ONEARMY/Precious-plastic-starterkit-extrusion/0. Start/Intro - Extrusion Workspace.pdf

www.preciousplastic.com/starterkits/showcase/extrusion

tiny.cc/starterkit-extrusion

Hi there!
Good to see you managed to get the download package of the

Extrusion Workspace Starter Kit!
If you haven’t done yet, make sure to have a look at the showcase page and quick introduction of this Starter Kit.

This package contains all the files you need to learn, plan and set up your Extrusion Workspace. It goes hand in hand with the step-by-step guide how to “Set up an Injection Workspace”.

There we explain the whole process of getting started, how to use the files in this download package and include links to relevant videos and documents. So don’t miss that!

Feel free to use whatever you need. Good luck!

-The Precious Plastic crew

# introduction
