ONEARMY/Precious-plastic-starterkit-extrusion/2. Plan your Business/2. Example (Extrusion)/Beamtastic - Action plan.png

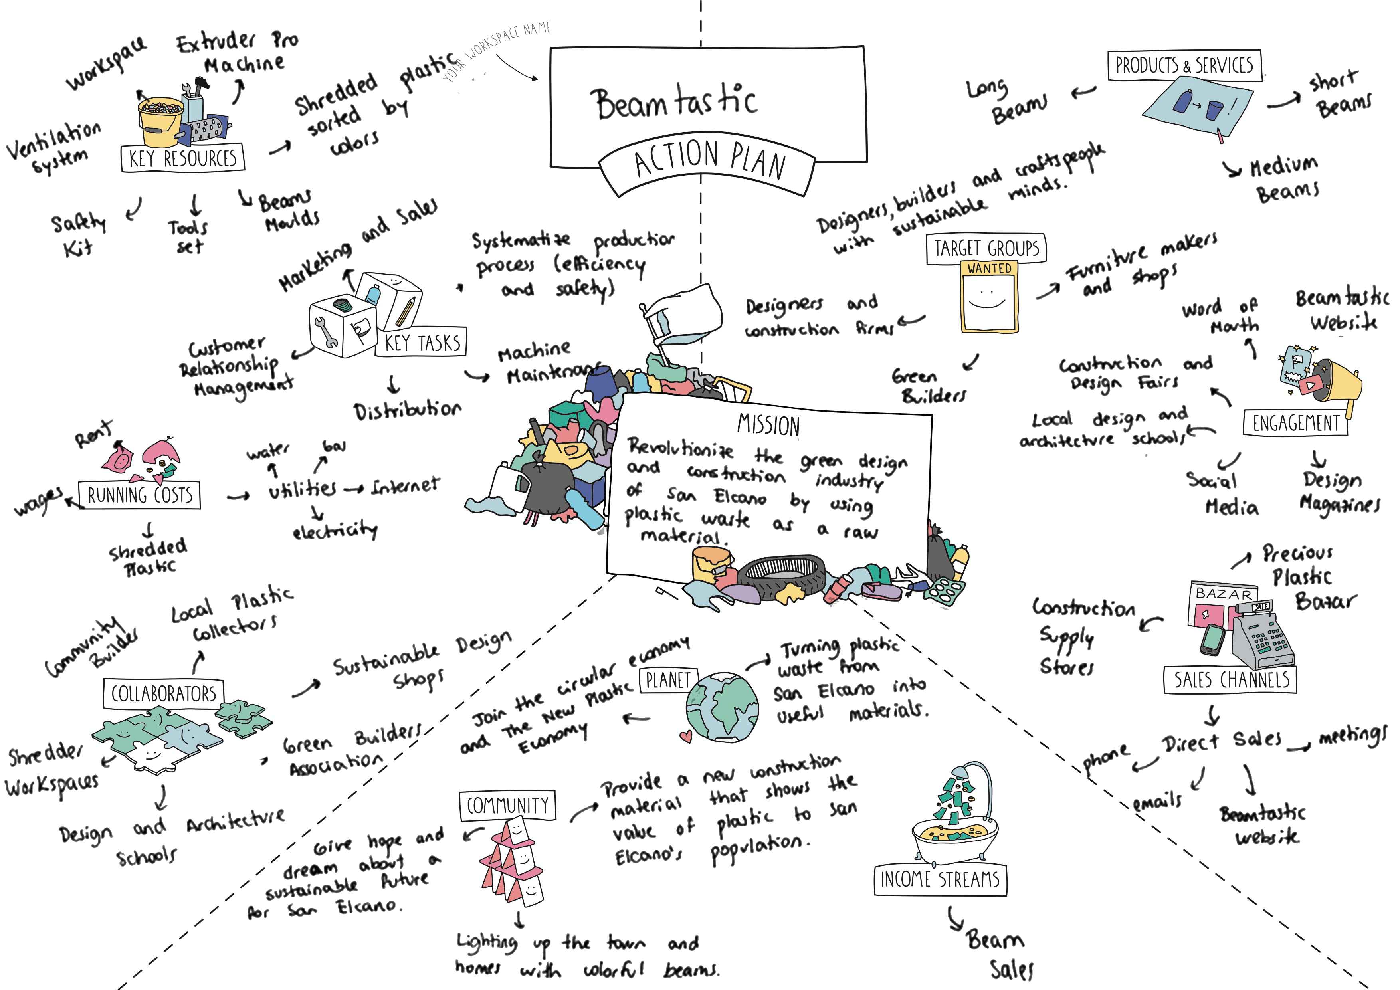
2. Plan your Business/2. Example (Extrusion)/Beamtastic - Action plan.png
