ONEARMY/Precious-plastic-starterkit-extrusion/6. Run your Workspace/1. Plastic Type Stamps/Stamps/HDPE.png

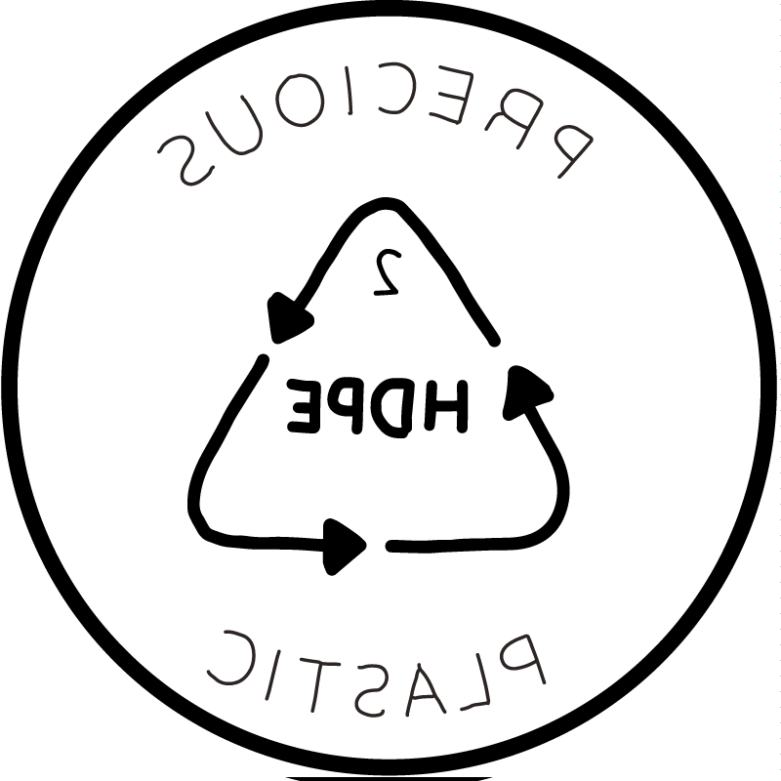
6. Run your Workspace/1. Plastic Type Stamps/Stamps/HDPE.png
