ONEARMY/Precious-plastic-starterkit-extrusion/6. Run your Workspace/3. Share/2. Project Images/Process/Recycling-process-2.jpg

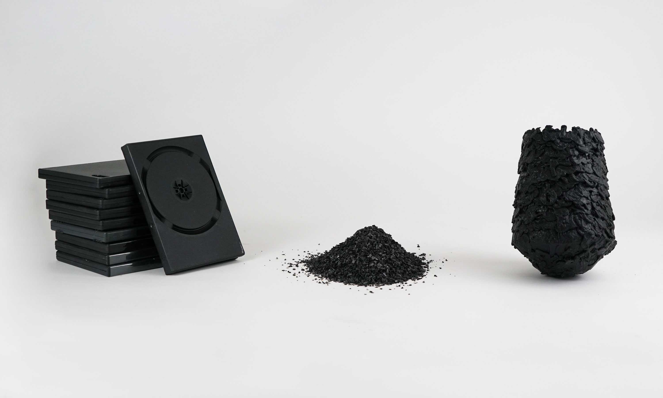
6. Run your Workspace/3. Share/2. Project Images/Process/Recycling-process-2.jpg
