ONEARMY/Precious-plastic-starterkit-extrusion/6. Run your Workspace/3. Share/2. Project Images/Products/Dome.jpg

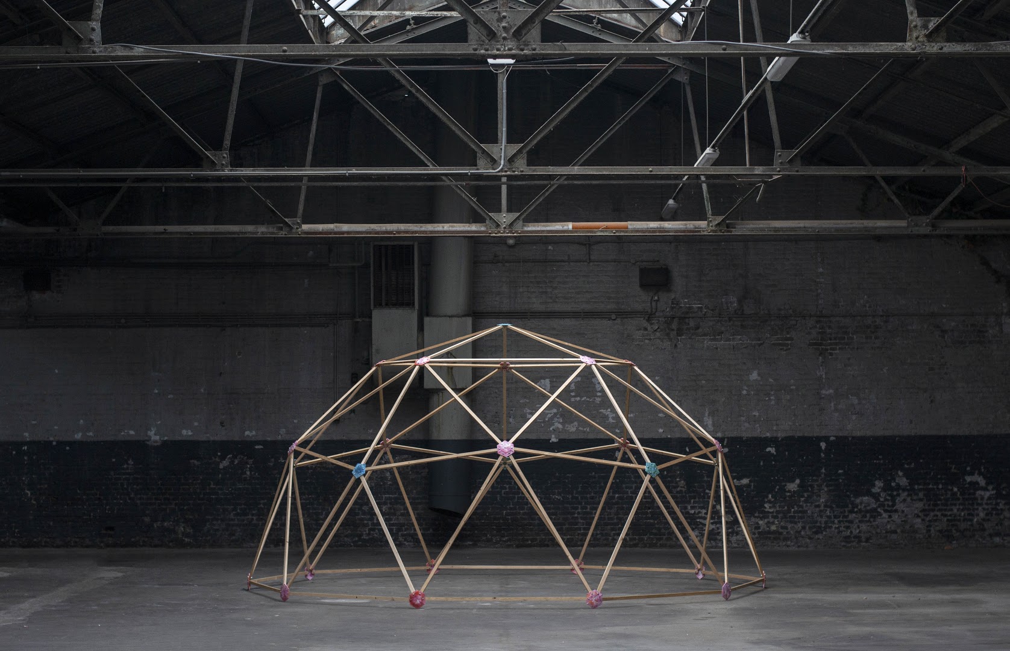
6. Run your Workspace/3. Share/2. Project Images/Products/Dome.jpg
