ONEARMY/Precious-plastic-starterkit-extrusion/3. Build the machine/Extrusion-Pro-Files/1-3D CAD/Extruder Solidworks CAD/EXTPRO-V1 1140.00-A Barrel.SLDASM

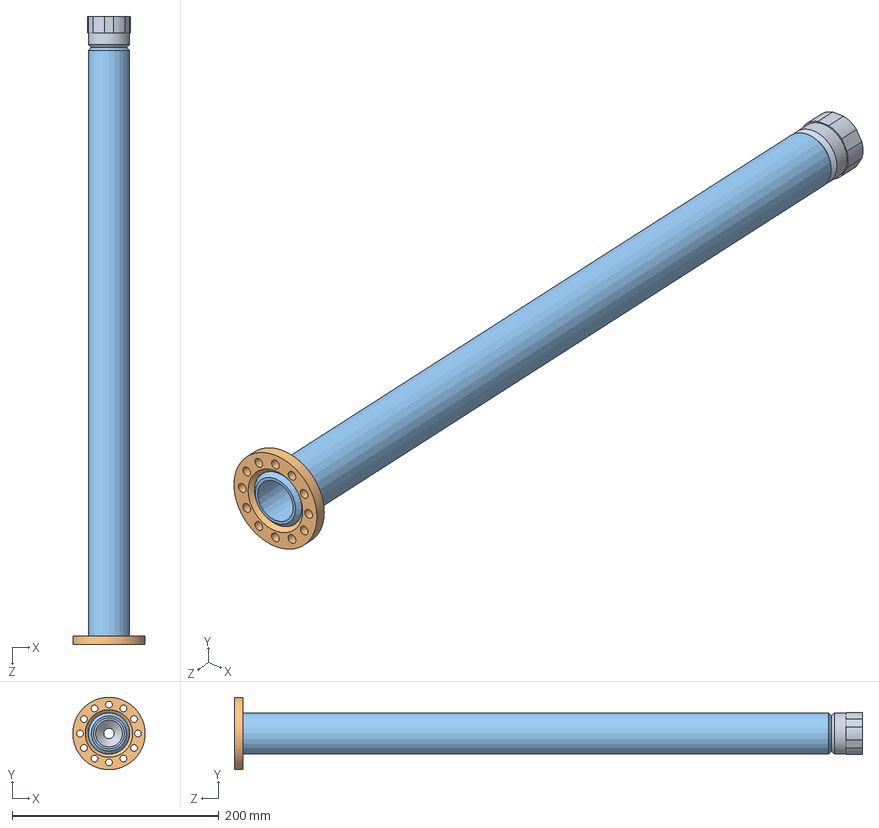
[picture p52: CAD file, 2020-01-07]
3. Build the machine/Extrusion-Pro-Files/1-3D CAD/Extruder Solidworks CAD/EXTPRO-V1 1140.00-A Barrel.SLDASM
70.0 x 70.0 x 608.0 mm
EXTPRO-V1 1140.01-A Barrel
EXTPRO-V1 1140.02-A Barrel flange
EXTPRO-V1 1140.03-A Barrel tip
