ONEARMY/Precious-plastic-starterkit-extrusion/3. Build the machine/Extrusion-Pro-Files/1-3D CAD/Extruder Solidworks CAD/EXTPRO-V1 1110.00-A Gearbox flange.sldasm

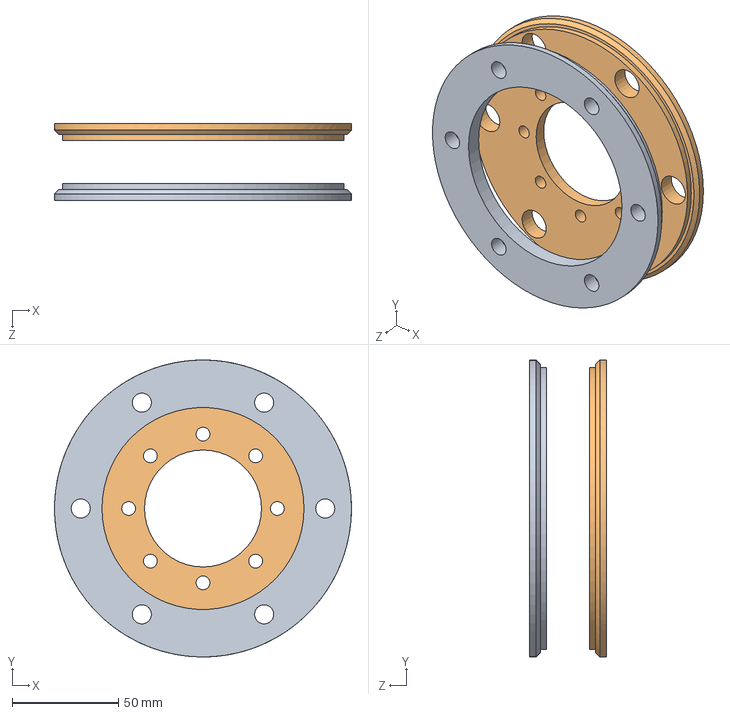
[picture p53: CAD file, 2020-01-07]
3. Build the machine/Extrusion-Pro-Files/1-3D CAD/Extruder Solidworks CAD/EXTPRO-V1 1110.00-A Gearbox flange.sldasm
139.7 x 139.7 x 36.0 mm
EXTPRO-V1 1110.02-A Flange 1
EXTPRO-V1 1110.03-A Flange 2
