ONEARMY/Precious-plastic-starterkit-extrusion/3. Build the machine/Extrusion-Pro-Files/1-3D CAD/Extruder Solidworks CAD/EXTPRO-V1 1121.00-A Bearing body.SLDASM

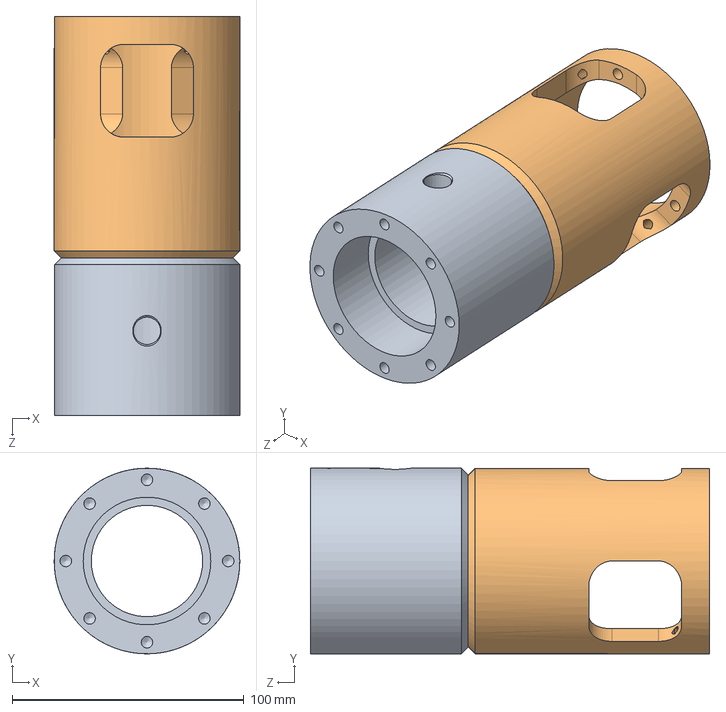
[picture p54: CAD file, 2020-01-07]
3. Build the machine/Extrusion-Pro-Files/1-3D CAD/Extruder Solidworks CAD/EXTPRO-V1 1121.00-A Bearing body.SLDASM
80.0 x 80.0 x 172.0 mm
EXTPRO-V1 1121.01-A Transition Piece
EXTPRO-V1 1121.02-A Bearing body
