ONEARMY/Precious-plastic-starterkit-extrusion/4. Set up the space/CAD Files/Adjustable mould support surface/Adjustmable mould support surface.STEP

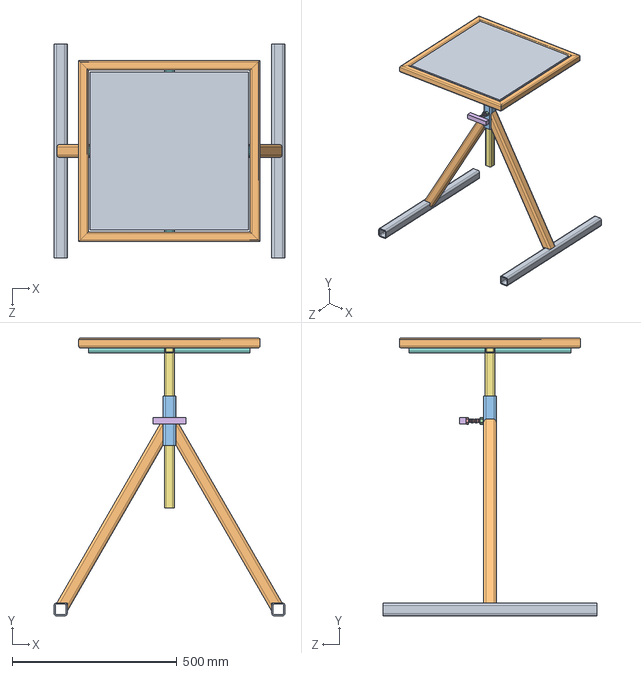
[picture p65: CAD file, 2020-01-07]
4. Set up the space/CAD Files/Adjustable mould support surface/Adjustmable mould support surface.STEP
700.0 x 843.0 x 650.0 mm
