ONEARMY/Precious-plastic-starterkit-extrusion/4. Set up the space/CAD Files/Beam mould hanger/Beam mould hanger.STEP

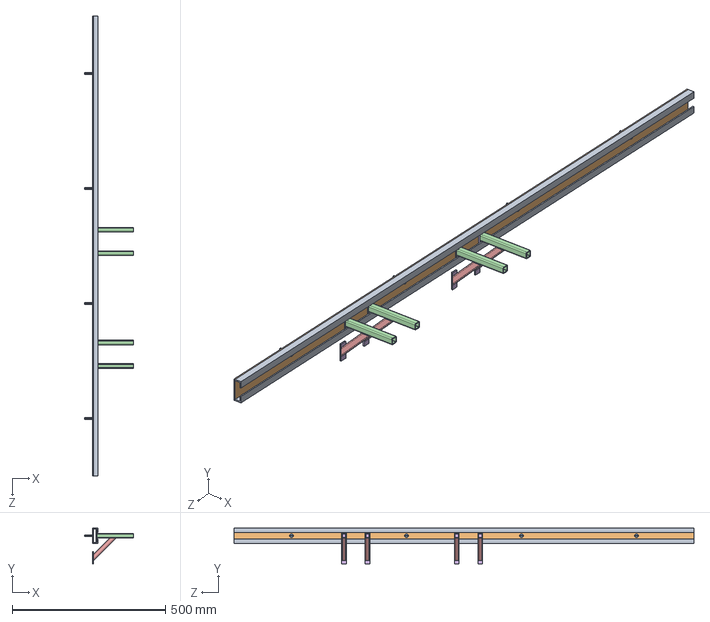
[picture p66: CAD file, 2020-01-07]
4. Set up the space/CAD Files/Beam mould hanger/Beam mould hanger.STEP
161.0 x 116.7 x 1500.0 mm
