ONEARMY/Precious-plastic-starterkit-extrusion/4. Set up the space/CAD Files/Beam storage rack/Beam storage rack.STEP

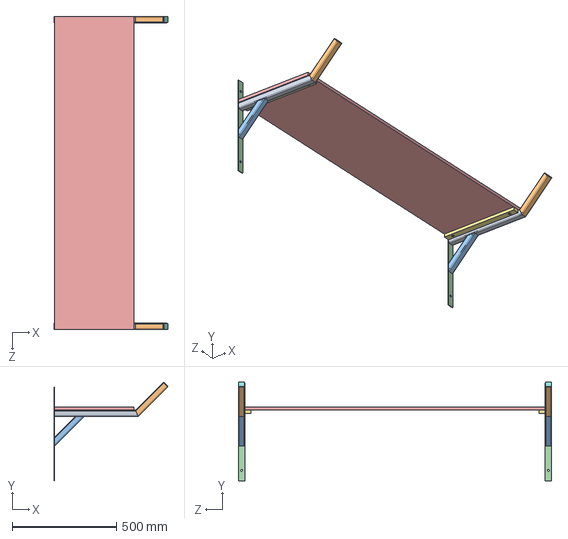
[picture p67: CAD file, 2020-01-07]
4. Set up the space/CAD Files/Beam storage rack/Beam storage rack.STEP
545.8 x 472.6 x 1500.0 mm
