ONEARMY/Precious-plastic-starterkit-extrusion/4. Set up the space/CAD Files/Mobile tool station/Mobile tool station.STEP

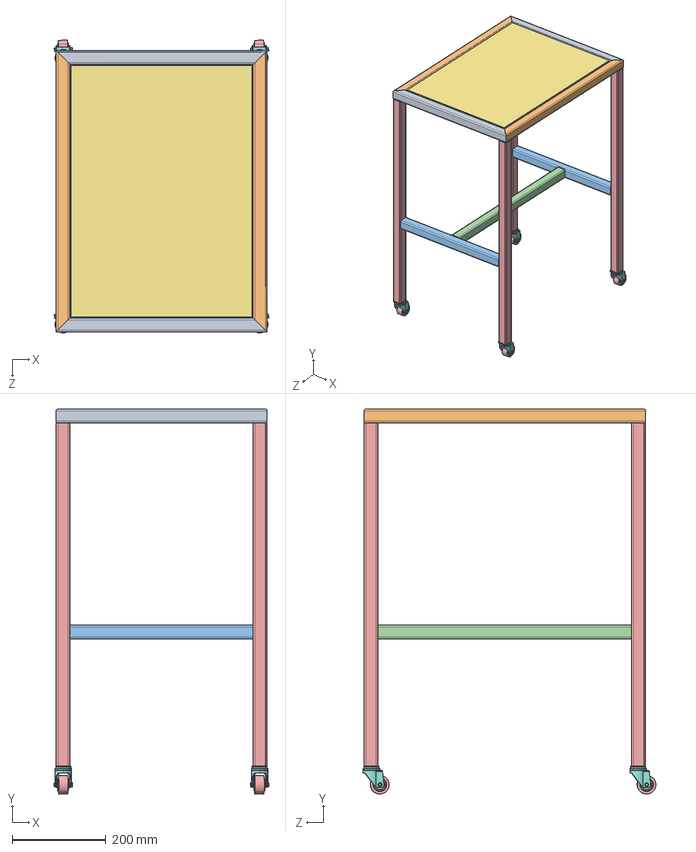
[picture p68: CAD file, 2020-01-07]
4. Set up the space/CAD Files/Mobile tool station/Mobile tool station.STEP
457.0 x 820.0 x 623.8 mm
