ONEARMY/Precious-plastic-starterkit-extrusion/4. Set up the space/CAD Files/Shredded plastic storage shelf/Shredded plastic storage shelf.STEP

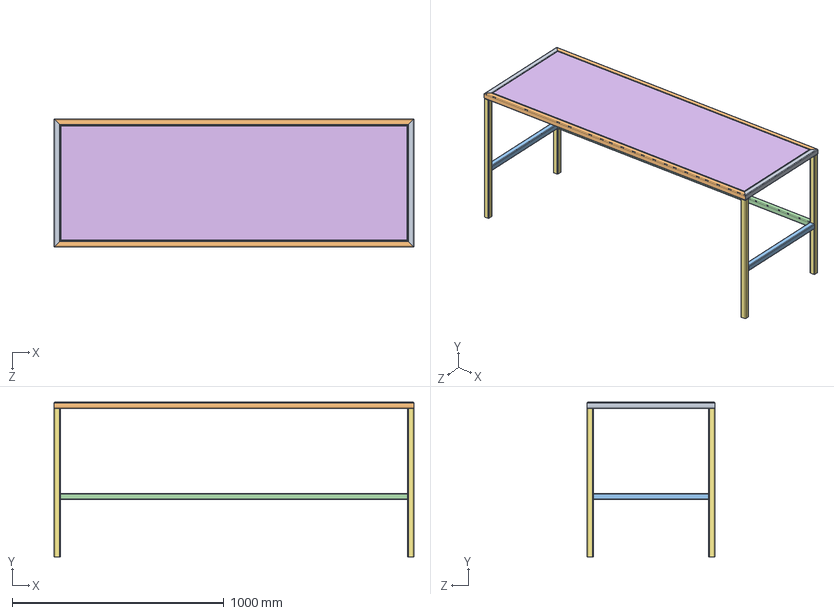
[picture p69: CAD file, 2020-01-07]
4. Set up the space/CAD Files/Shredded plastic storage shelf/Shredded plastic storage shelf.STEP
1700.0 x 730.0 x 605.0 mm
