ONEARMY/Precious-plastic-starterkit-extrusion/4. Set up the space/CAD Files/Shredded plastic trolley/Shredded plastic trolley.STEP

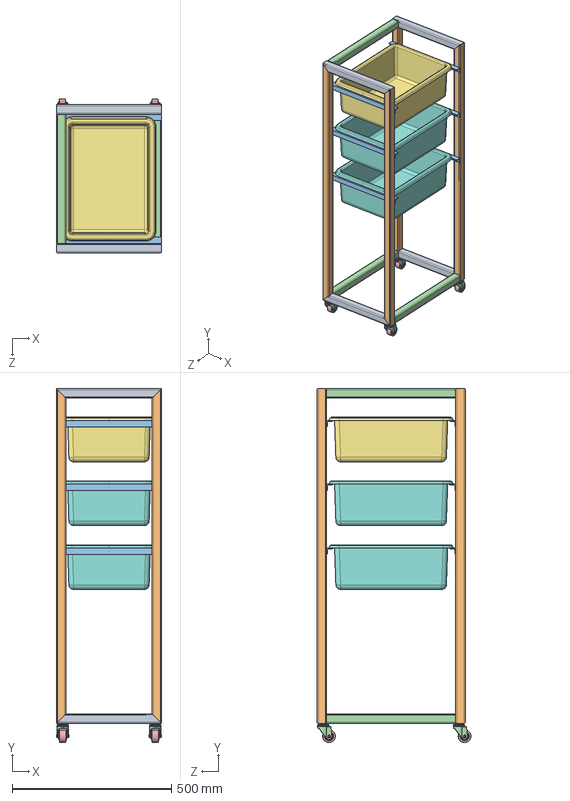
[picture p70: CAD file, 2020-01-07]
4. Set up the space/CAD Files/Shredded plastic trolley/Shredded plastic trolley.STEP
330.0 x 1110.0 x 482.9 mm
