ONEARMY/Precious-plastic-starterkit-extrusion/4. Set up the space/CAD Files/Workbench/Workbench.STEP

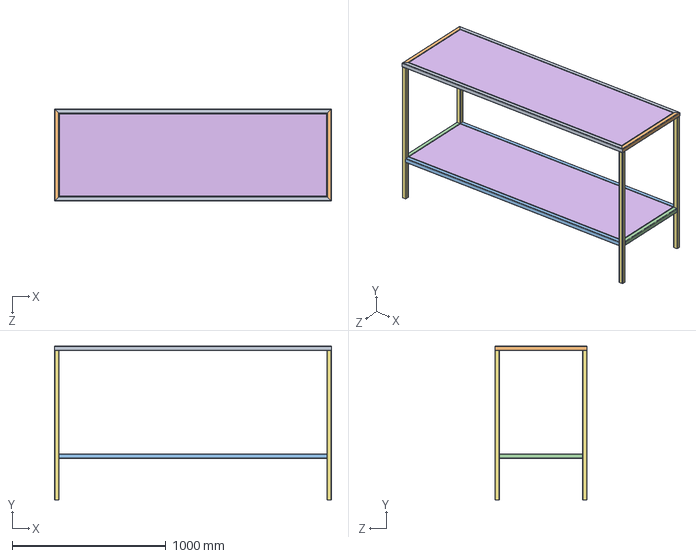
[picture p71: CAD file, 2020-01-07]
4. Set up the space/CAD Files/Workbench/Workbench.STEP
1800.0 x 1000.0 x 600.0 mm
