ONEARMY/Precious-plastic-starterkit-extrusion/3. Build the machine/Extrusion-Pro-Files/2-Laser cut files/STEP/Electronics box (CarbonSteel)/EXTPRO-V1 2100.06-A Cover attachment - QTY_4.STEP

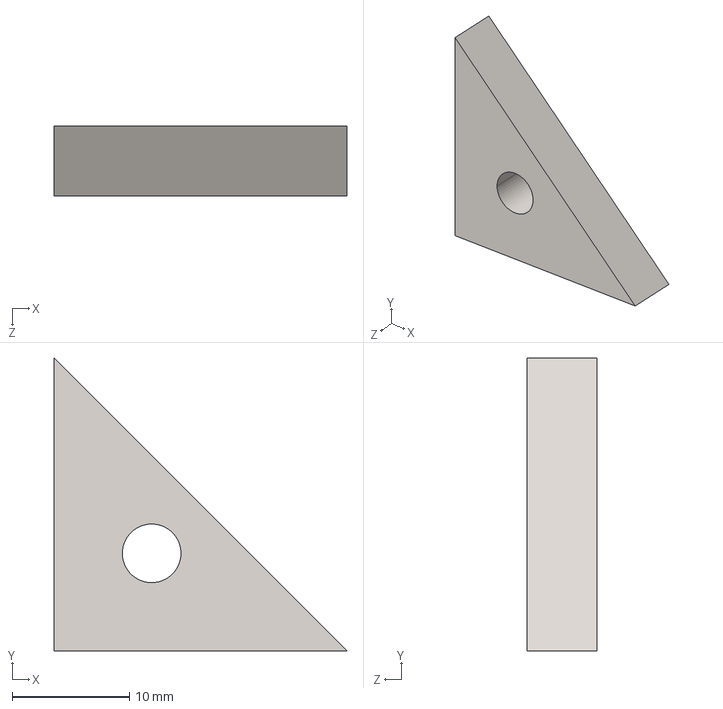
[picture p74: CAD file, 2020-01-07]
3. Build the machine/Extrusion-Pro-Files/2-Laser cut files/STEP/Electronics box (CarbonSteel)/EXTPRO-V1 2100.06-A Cover attachment - QTY_4.STEP
25.0 x 25.0 x 6.00 mm
