ONEARMY/Precious-plastic-starterkit-extrusion/3. Build the machine/Extrusion-Pro-Files/2-Laser cut files/STEP/Flanges (CarbonSteel)/EXTPRO-V1 1140.02-A Barrel flange - QTY_1.STEP

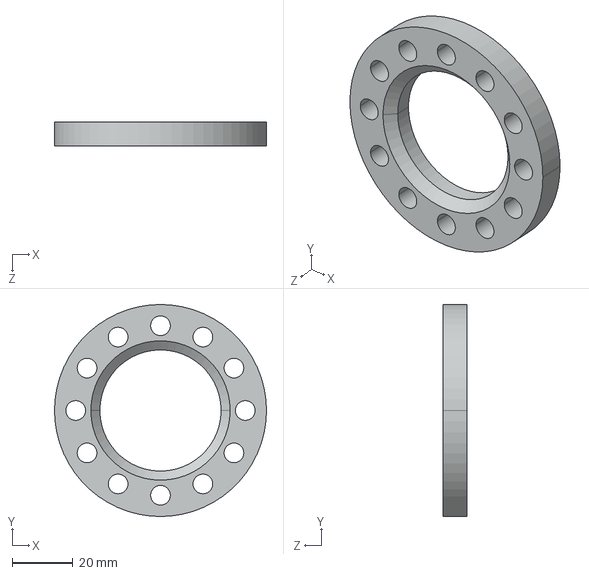
[picture p75: CAD file, 2020-01-07]
3. Build the machine/Extrusion-Pro-Files/2-Laser cut files/STEP/Flanges (CarbonSteel)/EXTPRO-V1 1140.02-A Barrel flange - QTY_1.STEP
70.0 x 70.0 x 8.00 mm
