ONEARMY/Precious-plastic-starterkit-extrusion/3. Build the machine/Upgrades/Barrel Support/1-3D CAD/EXTPRO-V1 3000.05-A Barrel support 2.SLDPRT

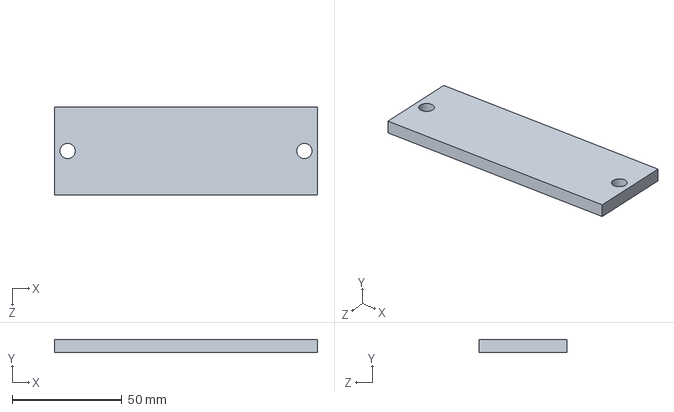
[picture p76: CAD file, 2020-01-07]
3. Build the machine/Upgrades/Barrel Support/1-3D CAD/EXTPRO-V1 3000.05-A Barrel support 2.SLDPRT
120.0 x 6.00 x 40.0 mm
