ONEARMY/Precious-plastic-starterkit-extrusion/3. Build the machine/Extrusion-Pro-Files/2-Laser cut files/DXF/Electronics box (1mm_CarbonSteel)/EXTPRO-V1 2100.03-A Side 2 - QTY_1.DXF

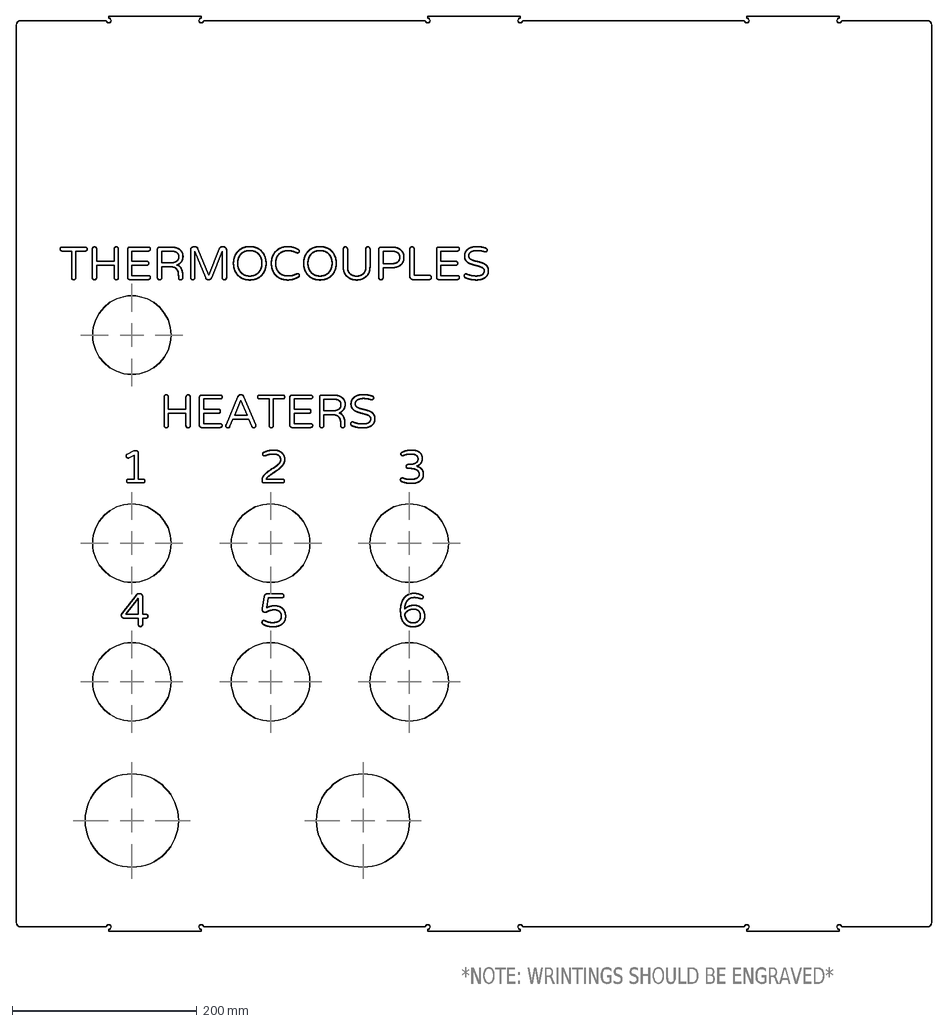
[picture p77: CAD file, 2020-01-07]
3. Build the machine/Extrusion-Pro-Files/2-Laser cut files/DXF/Electronics box (1mm_CarbonSteel)/EXTPRO-V1 2100.03-A Side 2 - QTY_1.DXF
*NOTE: WRINTINGS SHOULD BE ENGRAVED*
