ONEARMY/Precious-plastic-starterkit-extrusion/3. Build the machine/Extrusion-Pro-Files/2-Laser cut files/DXF/Flanges (8mm_CarbonSteel)/EXTPRO-V1 1110.03-A Flange 2 - QTY_1.DXF

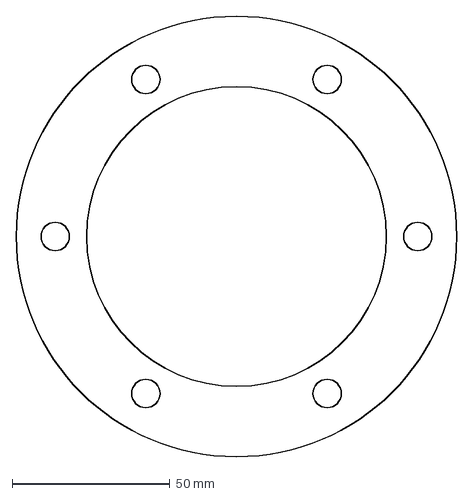
[picture p78: CAD file, 2020-01-07]
3. Build the machine/Extrusion-Pro-Files/2-Laser cut files/DXF/Flanges (8mm_CarbonSteel)/EXTPRO-V1 1110.03-A Flange 2 - QTY_1.DXF
139.7 x 139.7 mm
