ONEARMY/Precious-plastic-starterkit-extrusion/3. Build the machine/Extrusion-Pro-Files/2-Laser cut files/DXF/Electronics box (1mm_CarbonSteel)/EXTPRO-V1 2100.04-A Side 1 - QTY_1.DXF

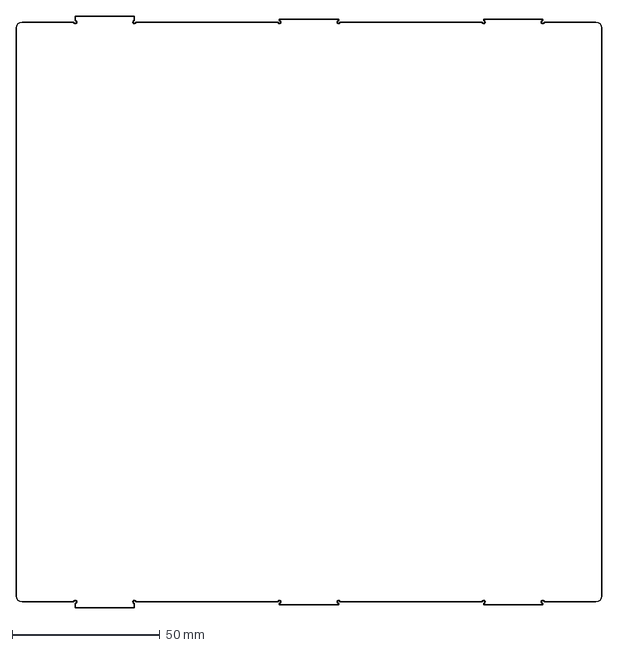
[picture p80: CAD file, 2020-01-07]
3. Build the machine/Extrusion-Pro-Files/2-Laser cut files/DXF/Electronics box (1mm_CarbonSteel)/EXTPRO-V1 2100.04-A Side 1 - QTY_1.DXF
198.0 x 200.0 mm
