ONEARMY/Precious-plastic-starterkit-extrusion/3. Build the machine/Extrusion-Pro-Files/2-Laser cut files/DXF/Flanges (8mm_CarbonSteel)/EXTPRO-V1 1130.03-A Barrel flange 2 - QTY_1.DXF

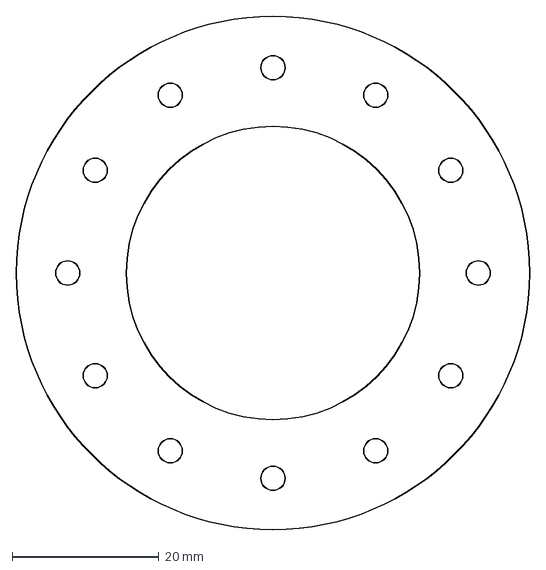
[picture p81: CAD file, 2020-01-07]
3. Build the machine/Extrusion-Pro-Files/2-Laser cut files/DXF/Flanges (8mm_CarbonSteel)/EXTPRO-V1 1130.03-A Barrel flange 2 - QTY_1.DXF
70.0 x 70.0 mm
