ONEARMY/Precious-plastic-starterkit-extrusion/3. Build the machine/Extrusion-Pro-Files/2-Laser cut files/STEP/Electronics box (CarbonSteel)/EXTPRO-V1 2100.03-A Side 2 - QTY_1.STEP

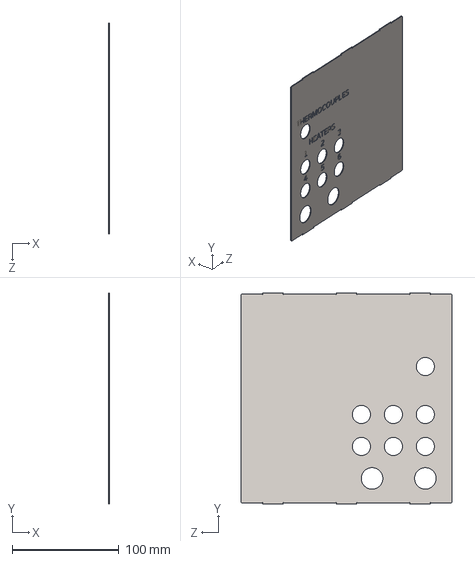
[picture p82: CAD file, 2020-01-07]
3. Build the machine/Extrusion-Pro-Files/2-Laser cut files/STEP/Electronics box (CarbonSteel)/EXTPRO-V1 2100.03-A Side 2 - QTY_1.STEP
1.00 x 198.0 x 198.0 mm
