ONEARMY/Precious-plastic-starterkit-extrusion/3. Build the machine/Extrusion-Pro-Files/2-Laser cut files/STEP/Flanges (CarbonSteel)/EXTPRO-V1 1110.03-A Motor side flange - QTY_1.STEP

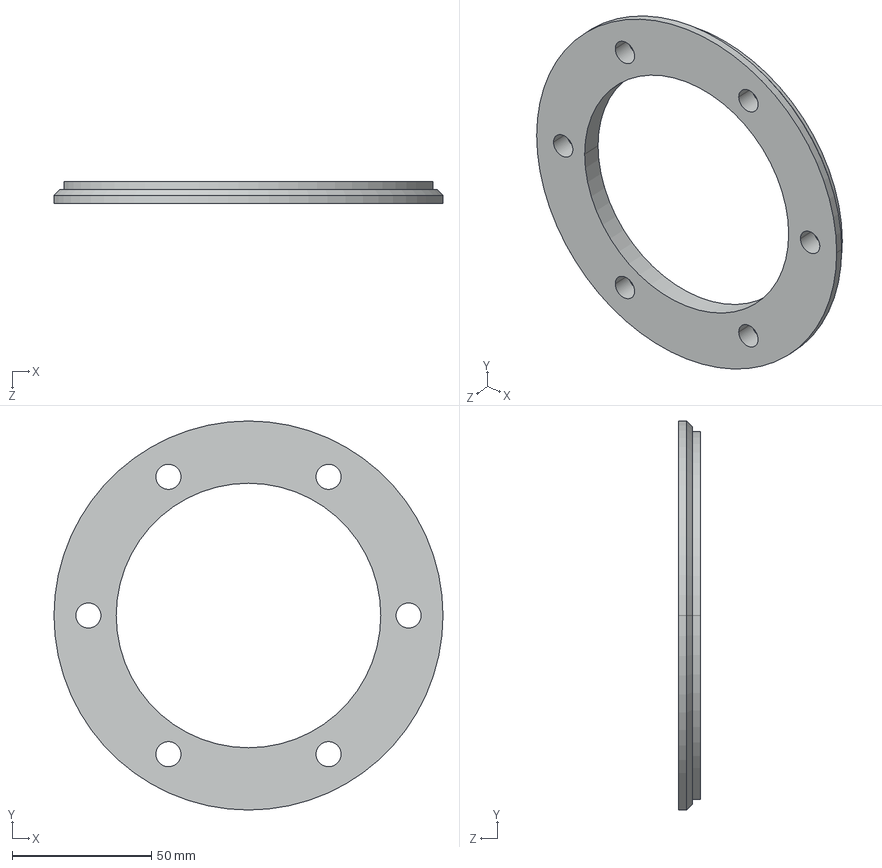
[picture p83: CAD file, 2020-01-07]
3. Build the machine/Extrusion-Pro-Files/2-Laser cut files/STEP/Flanges (CarbonSteel)/EXTPRO-V1 1110.03-A Motor side flange - QTY_1.STEP
139.7 x 139.7 x 8.00 mm
