ONEARMY/Precious-plastic-starterkit-extrusion/3. Build the machine/Extrusion-Pro-Files/1-3D CAD/Extruder Solidworks CAD/EXTPRO-V1 03 Shaft Clamp.sldprt

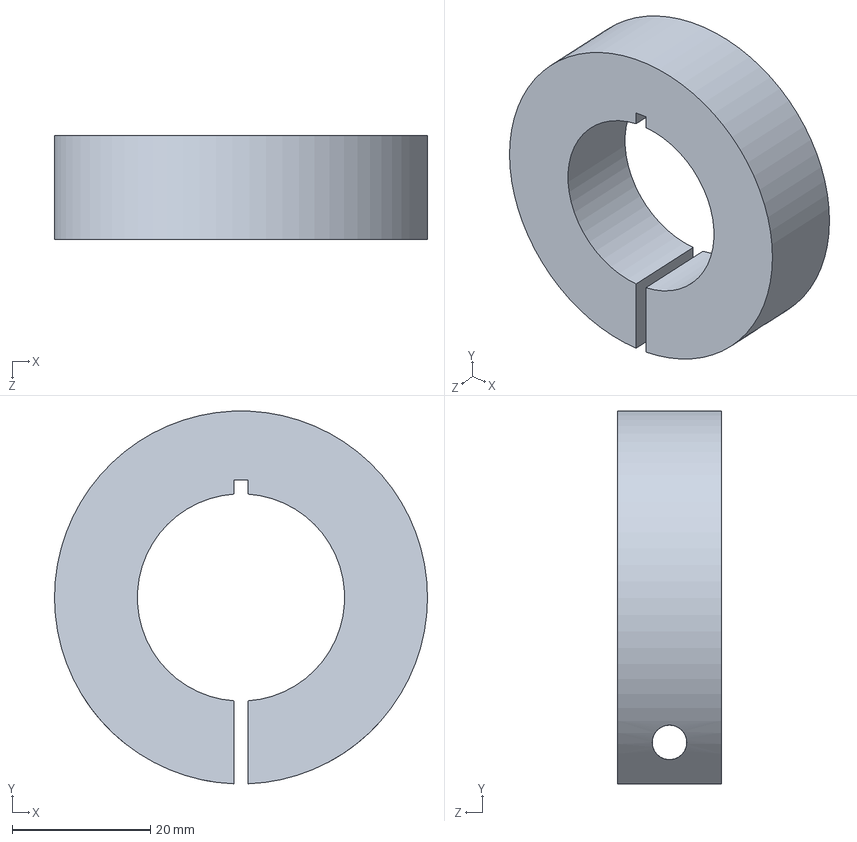
[picture p84: CAD file, 2020-01-07]
3. Build the machine/Extrusion-Pro-Files/1-3D CAD/Extruder Solidworks CAD/EXTPRO-V1 03 Shaft Clamp.sldprt
54.0 x 54.0 x 15.0 mm
