ONEARMY/Precious-plastic-starterkit-extrusion/3. Build the machine/Extrusion-Pro-Files/2-Laser cut files/DXF/Electronics box (1mm_CarbonSteel)/EXTPRO-V1 2100.01-A Cover - QTY_1.DXF

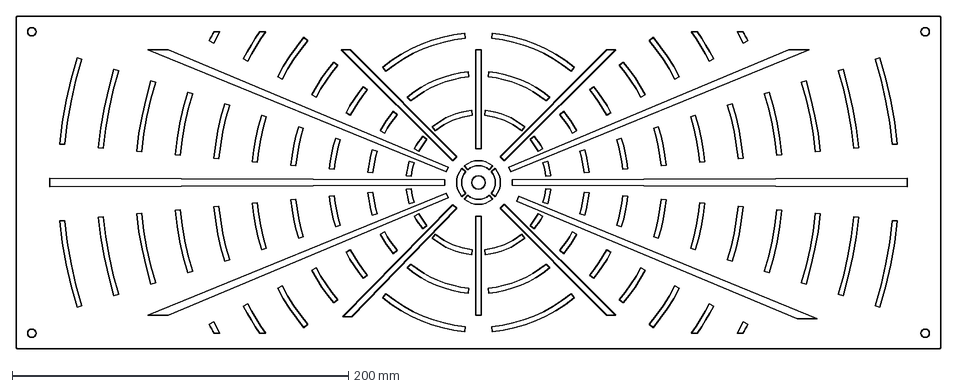
[picture p85: CAD file, 2020-01-07]
3. Build the machine/Extrusion-Pro-Files/2-Laser cut files/DXF/Electronics box (1mm_CarbonSteel)/EXTPRO-V1 2100.01-A Cover - QTY_1.DXF
550.0 x 198.0 mm
