ONEARMY/Precious-plastic-starterkit-extrusion/3. Build the machine/Extrusion-Pro-Files/2-Laser cut files/STEP/Electronics box (CarbonSteel)/EXTPRO-V1 2100.05-A Side 3 - QTY_2.STEP

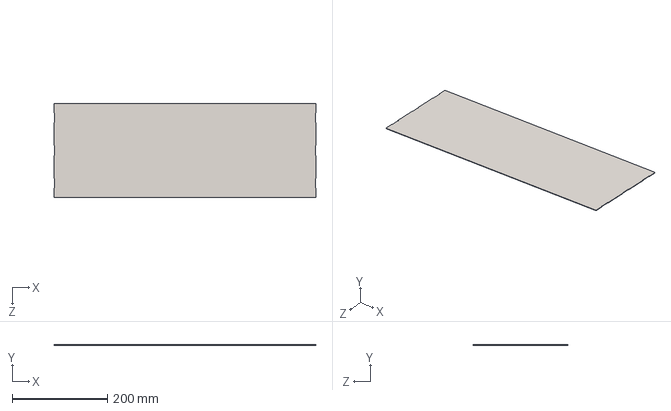
[picture p86: CAD file, 2020-01-07]
3. Build the machine/Extrusion-Pro-Files/2-Laser cut files/STEP/Electronics box (CarbonSteel)/EXTPRO-V1 2100.05-A Side 3 - QTY_2.STEP
550.0 x 1.00 x 198.0 mm
