ONEARMY/Precious-plastic-starterkit-extrusion/3. Build the machine/Extrusion-Pro-Files/2-Laser cut files/STEP/Electronics box (CarbonSteel)/EXTPRO-V1 2100.02-A Front - QTY_1.STEP

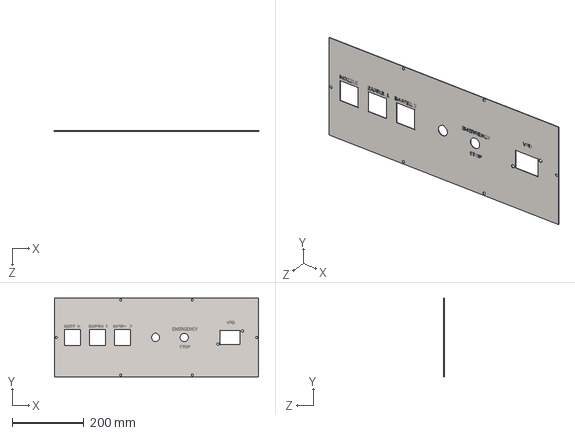
[picture p87: CAD file, 2020-01-07]
3. Build the machine/Extrusion-Pro-Files/2-Laser cut files/STEP/Electronics box (CarbonSteel)/EXTPRO-V1 2100.02-A Front - QTY_1.STEP
570.0 x 220.0 x 1.00 mm
