ONEARMY/Precious-plastic-starterkit-extrusion/3. Build the machine/Extrusion-Pro-Files/1-3D CAD/Extruder Solidworks CAD/EXTPRO-V1 1140.03-A Barrel tip.sldprt

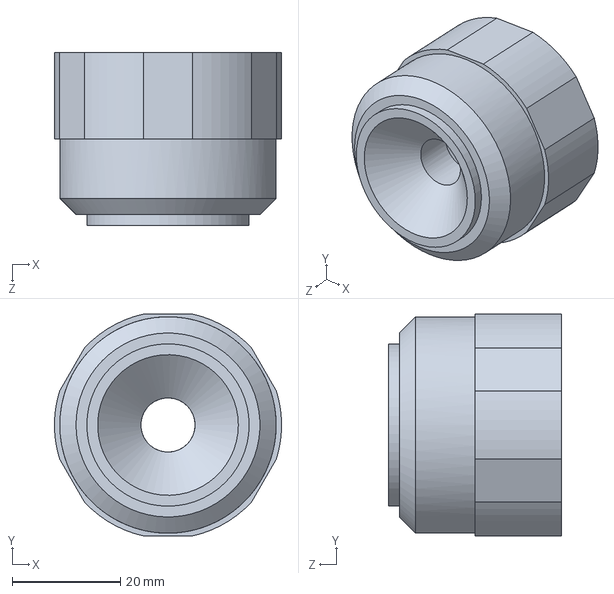
[picture p88: CAD file, 2020-01-07]
3. Build the machine/Extrusion-Pro-Files/1-3D CAD/Extruder Solidworks CAD/EXTPRO-V1 1140.03-A Barrel tip.sldprt
42.0 x 41.0 x 32.0 mm
