ONEARMY/Precious-plastic-starterkit-extrusion/3. Build the machine/Extrusion-Pro-Files/1-3D CAD/Extruder Solidworks CAD/EXTPRO-V1 02 Bearing seal-din3760-as_42x55x8-fkm.SLDPRT

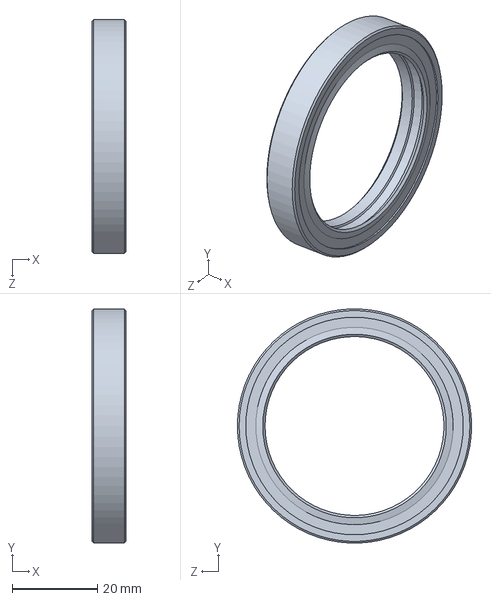
[picture p93: CAD file, 2020-01-07]
3. Build the machine/Extrusion-Pro-Files/1-3D CAD/Extruder Solidworks CAD/EXTPRO-V1 02 Bearing seal-din3760-as_42x55x8-fkm.SLDPRT
8.00 x 54.9 x 55.0 mm
