ONEARMY/Precious-plastic-starterkit-extrusion/3. Build the machine/Extrusion-Pro-Files/1-3D CAD/Extruder Solidworks CAD/EXTPRO-V1 3000.04-A Frame foot.SLDPRT

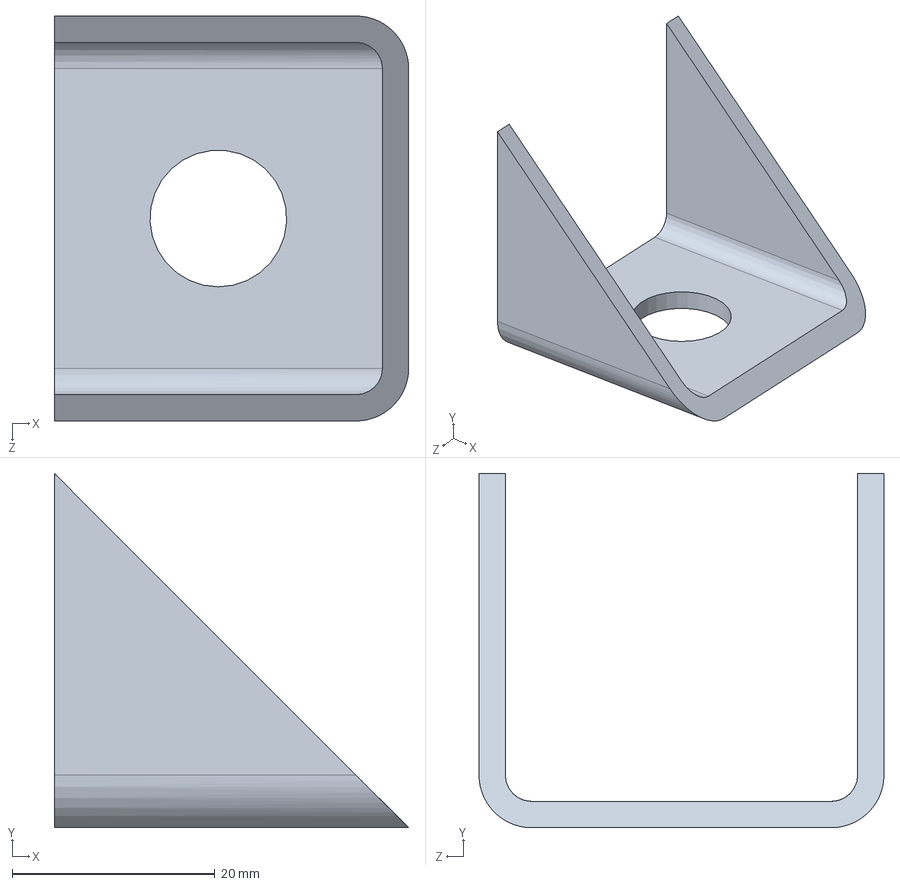
[picture p94: CAD file, 2020-01-07]
3. Build the machine/Extrusion-Pro-Files/1-3D CAD/Extruder Solidworks CAD/EXTPRO-V1 3000.04-A Frame foot.SLDPRT
35.0 x 35.0 x 40.0 mm
