ONEARMY/Precious-plastic-starterkit-extrusion/3. Build the machine/Extrusion-Pro-Files/1-3D CAD/Extruder Solidworks CAD/EXTPRO-V1 2000.01-A Electronics box support.SLDPRT

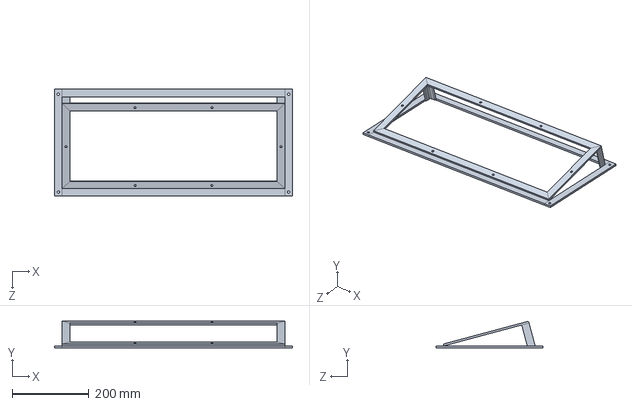
[picture p95: CAD file, 2020-01-07]
3. Build the machine/Extrusion-Pro-Files/1-3D CAD/Extruder Solidworks CAD/EXTPRO-V1 2000.01-A Electronics box support.SLDPRT
620.0 x 69.4 x 278.1 mm
