ONEARMY/Precious-plastic-starterkit-extrusion/3. Build the machine/Extrusion-Pro-Files/1-3D CAD/Extruder Solidworks CAD/EXTPRO-V1 1120.01-A Seal bearing spacer.sldprt

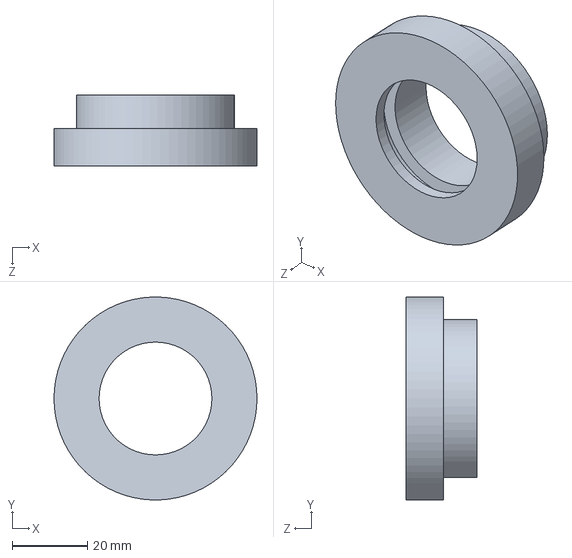
[picture p98: CAD file, 2020-01-07]
3. Build the machine/Extrusion-Pro-Files/1-3D CAD/Extruder Solidworks CAD/EXTPRO-V1 1120.01-A Seal bearing spacer.sldprt
54.0 x 53.9 x 19.0 mm
