ONEARMY/Precious-plastic-starterkit-extrusion/3. Build the machine/Extrusion-Pro-Files/1-3D CAD/Extruder Solidworks CAD/EXTPRO-V1 1120.02-A Coupling Shaft.sldprt

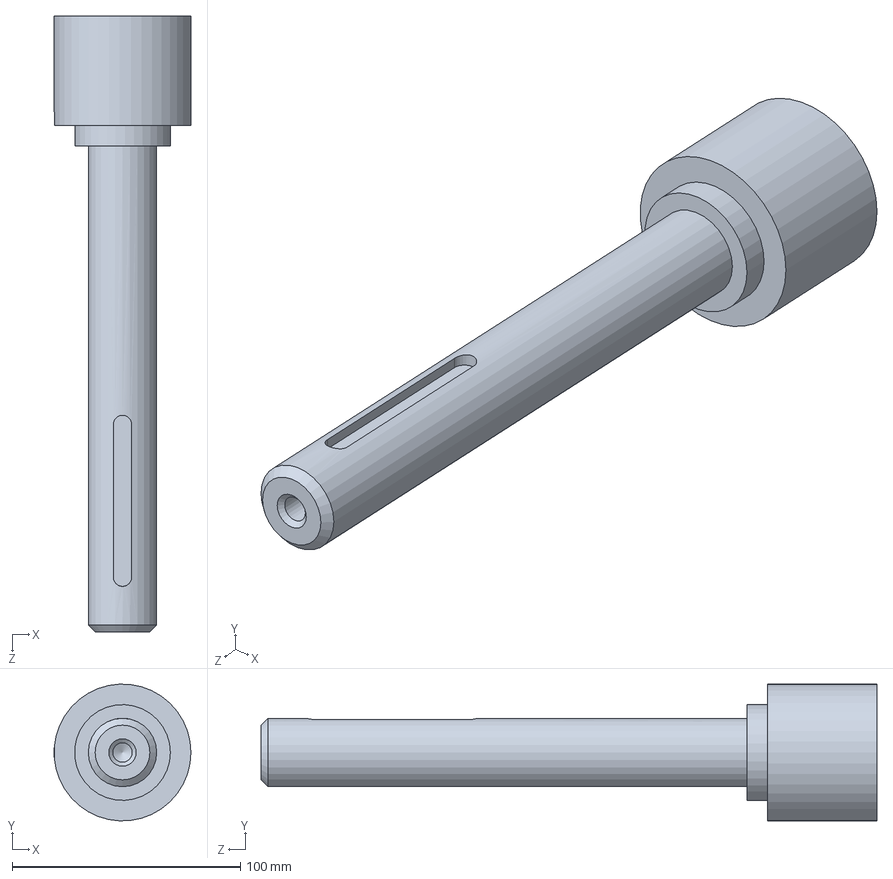
[picture p103: CAD file, 2020-01-07]
3. Build the machine/Extrusion-Pro-Files/1-3D CAD/Extruder Solidworks CAD/EXTPRO-V1 1120.02-A Coupling Shaft.sldprt
60.0 x 60.0 x 270.0 mm
