ONEARMY/Precious-plastic-starterkit-extrusion/3. Build the machine/Extrusion-Pro-Files/1-3D CAD/Extruder Solidworks CAD/EXTPRO-V1 3000.02-A Top shelf.SLDPRT

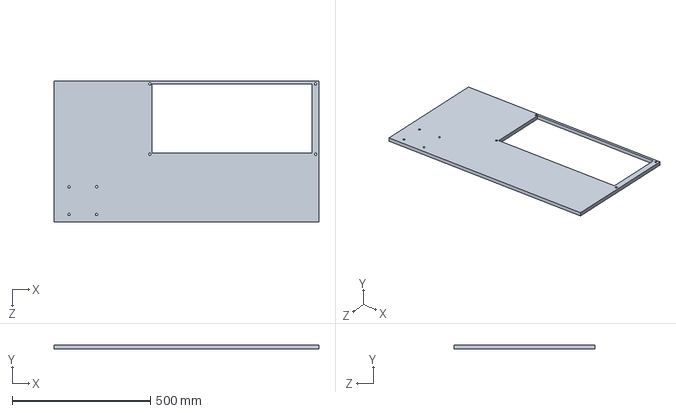
[picture p107: CAD file, 2020-01-07]
3. Build the machine/Extrusion-Pro-Files/1-3D CAD/Extruder Solidworks CAD/EXTPRO-V1 3000.02-A Top shelf.SLDPRT
960.0 x 15.0 x 510.0 mm
