ONEARMY/Precious-plastic-starterkit-extrusion/3. Build the machine/Extrusion-Pro-Files/1-3D CAD/Extruder Solidworks CAD/EXTPRO-V1 11 Heating element 40x50 350W.SLDPRT

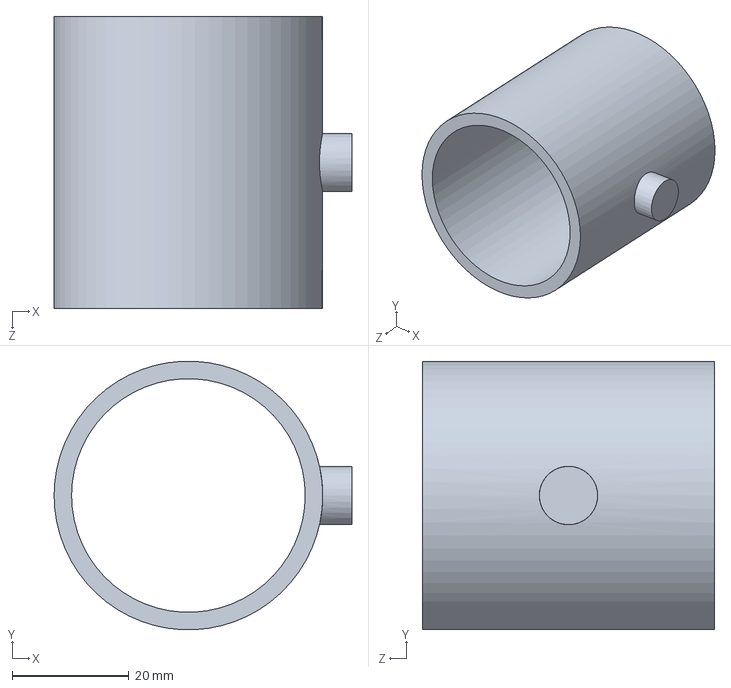
[picture p110: CAD file, 2020-01-07]
3. Build the machine/Extrusion-Pro-Files/1-3D CAD/Extruder Solidworks CAD/EXTPRO-V1 11 Heating element 40x50 350W.SLDPRT
51.0 x 45.9 x 50.0 mm
