ONEARMY/Precious-plastic-starterkit-extrusion/3. Build the machine/Extrusion-Pro-Files/1-3D CAD/Extruder Solidworks CAD/EXTPRO-V1 13 Heating element 40x20 150W.SLDPRT

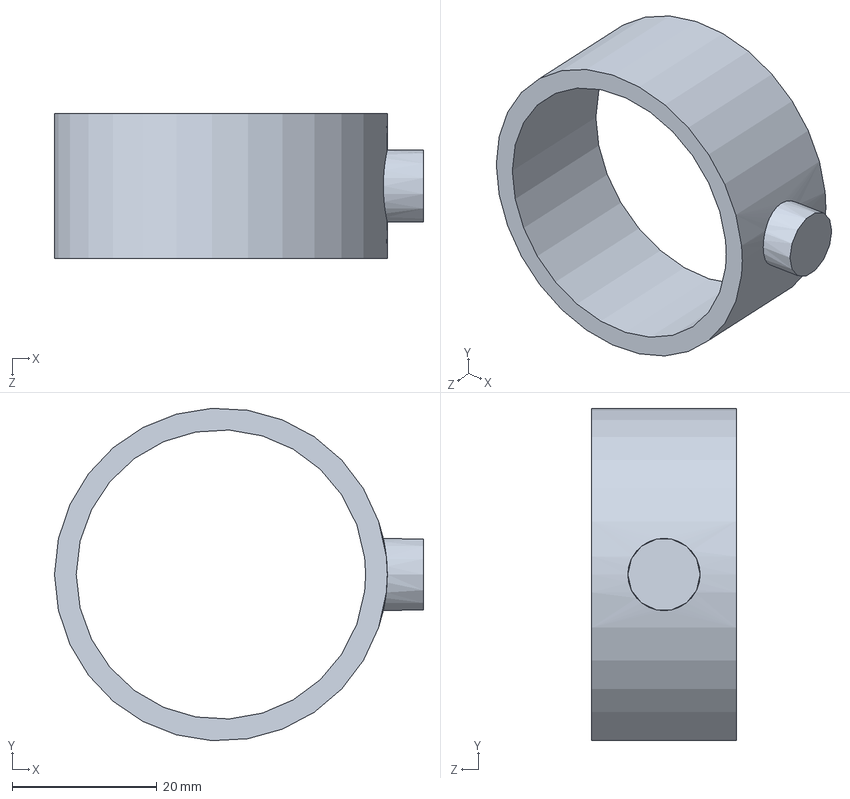
[picture p111: CAD file, 2020-01-07]
3. Build the machine/Extrusion-Pro-Files/1-3D CAD/Extruder Solidworks CAD/EXTPRO-V1 13 Heating element 40x20 150W.SLDPRT
51.0 x 45.9 x 20.0 mm
