ONEARMY/Precious-plastic-starterkit-extrusion/3. Build the machine/Extrusion-Pro-Files/1-3D CAD/Extruder Solidworks CAD/EXTPRO-V1 1130.02-A Barrel flange 1.SLDPRT

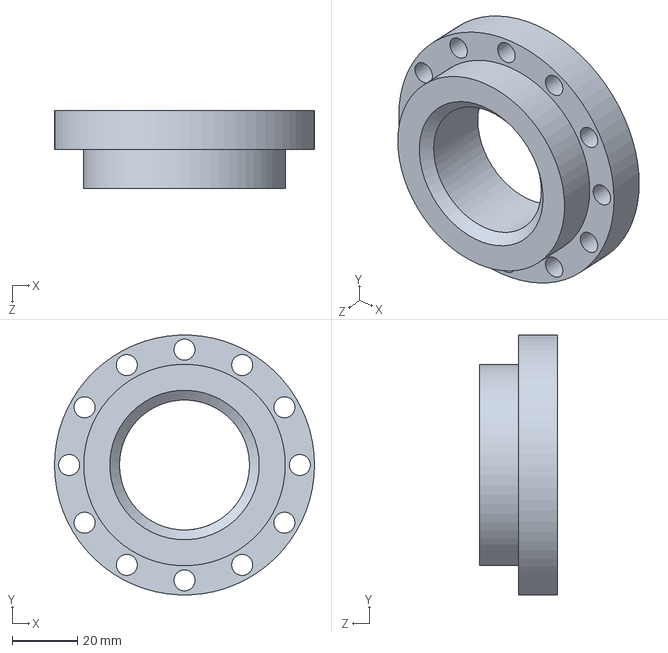
[picture p113: CAD file, 2020-01-07]
3. Build the machine/Extrusion-Pro-Files/1-3D CAD/Extruder Solidworks CAD/EXTPRO-V1 1130.02-A Barrel flange 1.SLDPRT
80.0 x 79.9 x 24.0 mm
