ONEARMY/Precious-plastic-starterkit-extrusion/3. Build the machine/Extrusion-Pro-Files/1-3D CAD/Extruder Solidworks CAD/EXTPRO-V1 01 Motor BAZ39-LE100ZLSB4P.SLDPRT

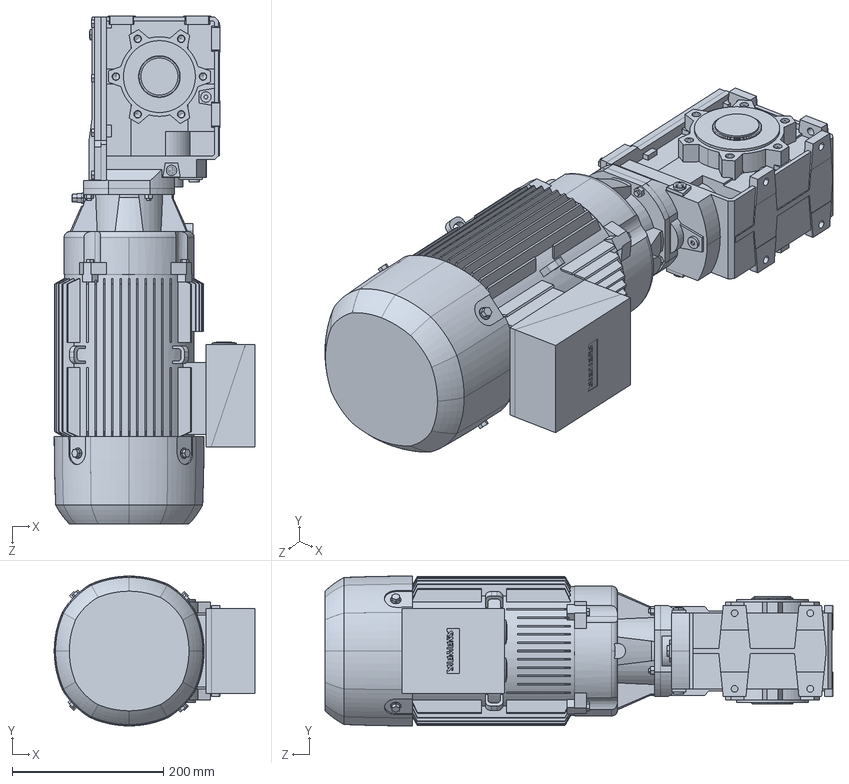
[picture p117: CAD file, 2020-01-07]
3. Build the machine/Extrusion-Pro-Files/1-3D CAD/Extruder Solidworks CAD/EXTPRO-V1 01 Motor BAZ39-LE100ZLSB4P.SLDPRT
265.0 x 198.0 x 671.0 mm
