ONEARMY/Precious-plastic-starterkit-extrusion/3. Build the machine/Extrusion-Pro-Files/1-3D CAD/Extruder Solidworks CAD/EXTPRO-V1 04 Tapered bearing 32006X.SLDPRT

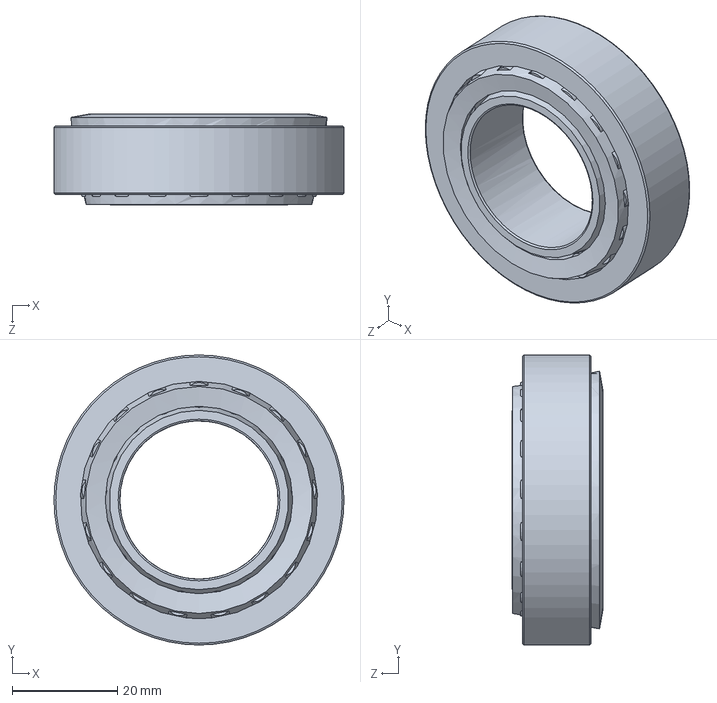
[picture p118: CAD file, 2020-01-07]
3. Build the machine/Extrusion-Pro-Files/1-3D CAD/Extruder Solidworks CAD/EXTPRO-V1 04 Tapered bearing 32006X.SLDPRT
55.0 x 55.0 x 17.3 mm
