ONEARMY/Precious-plastic-starterkit-extrusion/3. Build the machine/Extrusion-Pro-Files/1-3D CAD/Extruder Solidworks CAD/EXTPRO-V1 1130.01-A Barrel inlet.SLDPRT

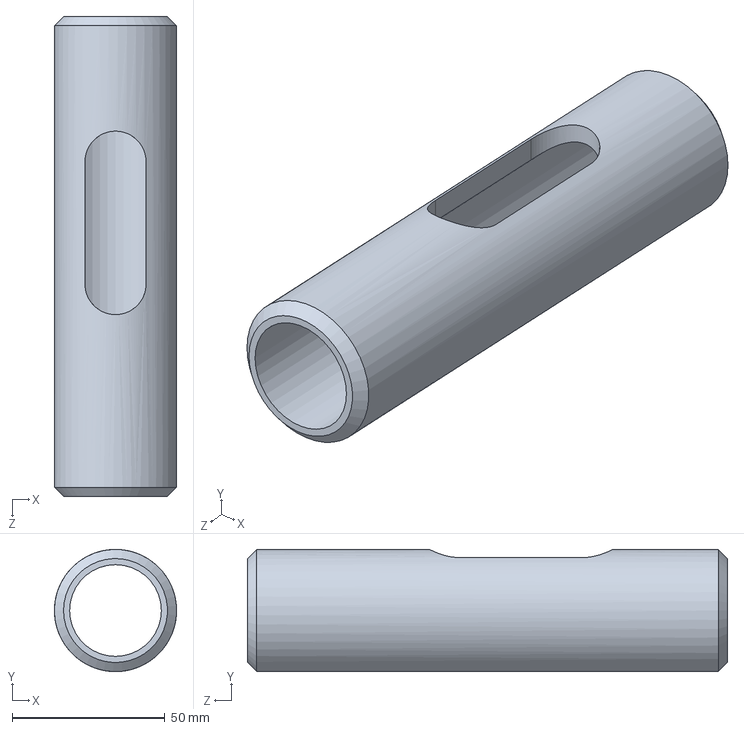
[picture p124: CAD file, 2020-01-07]
3. Build the machine/Extrusion-Pro-Files/1-3D CAD/Extruder Solidworks CAD/EXTPRO-V1 1130.01-A Barrel inlet.SLDPRT
40.0 x 40.0 x 157.0 mm
