ONEARMY/Precious-plastic-starterkit-extrusion/3. Build the machine/Extrusion-Pro-Files/1-3D CAD/Extruder Solidworks CAD/EXTPRO-V1 1130.00-A Barrel inlet.SLDASM

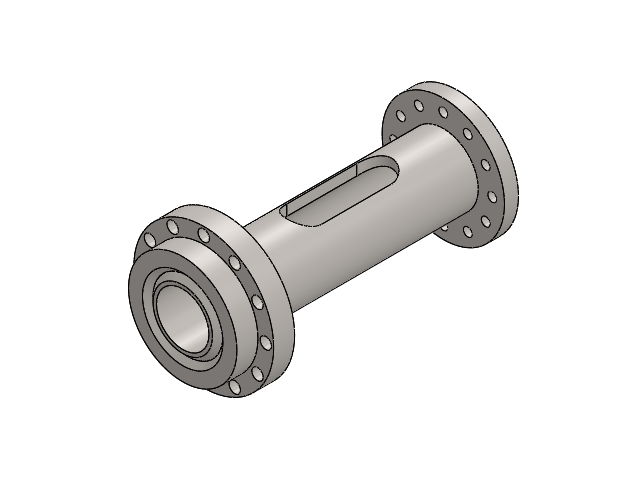
[picture p126: CAD file, 2020-01-07]
3. Build the machine/Extrusion-Pro-Files/1-3D CAD/Extruder Solidworks CAD/EXTPRO-V1 1130.00-A Barrel inlet.SLDASM
EXTPRO-V1 1130.01-A Barrel inlet
EXTPRO-V1 1130.02-A Barrel flange 1
EXTPRO-V1 1130.03-A Barrel flange 2
