ONEARMY/Precious-plastic-starterkit-extrusion/3. Build the machine/Extrusion-Pro-Files/3-2D blueprints/EXTPRO-V1 1120.00-A Bearing Body _ Shaft.PDF

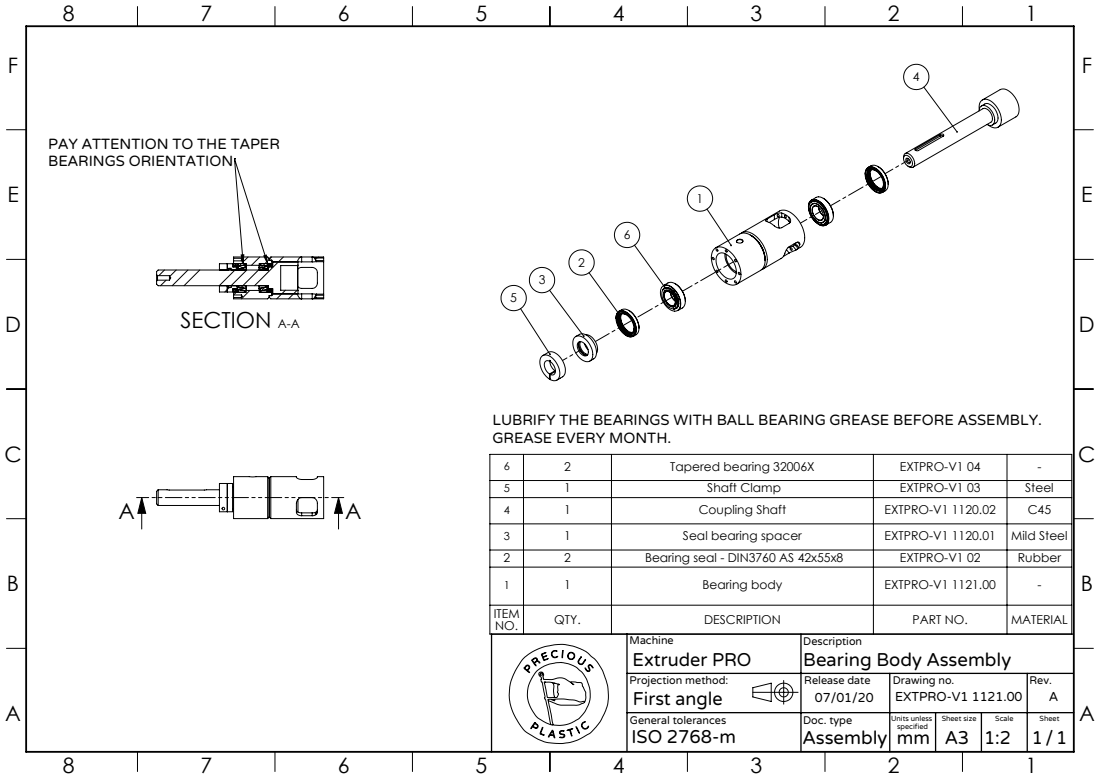
[picture p142: page 1]
SECTION A-A

PAY ATTENTION TO THE TAPER
BEARINGS ORIENTATION

LUBRIFY THE BEARINGS WITH BALL BEARING GREASE BEFORE ASSEMBLY.
GREASE EVERY MONTH.

6 | 2 | Tapered bearing 32006X | EXTPRO-V1 04 | -
5 | 1 | Shaft Clamp | EXTPRO-V1 03 | Steel
4 | 1 | Coupling Shaft | EXTPRO-V1 1120.02 | C45
3 | 1 | Seal bearing spacer | EXTPRO-V1 1120.01 | Mild Steel
2 | 2 | Bearing seal - DIN3760 AS 42x55x8 | EXTPRO-V1 02 | Rubber
1 | 1 | Bearing body | EXTPRO-V1 1121.00 | -
ITEM NO. | QTY. | DESCRIPTION | PART NO. | MATERIAL

Machine Extruder PRO | Description Bearing Body Assembly
Projection method: First angle | Release date 07/01/20 | Drawing no. EXTPRO-V1 1121.00 | Rev. A
General tolerances ISO 2768-m | Doc. type Assembly | Units unless specified mm | Sheet size A3 | Scale 1:2 | Sheet 1 1 /
