ONEARMY/Precious-plastic-starterkit-extrusion/3. Build the machine/Extrusion-Pro-Files/3-2D blueprints/EXTPRO-V1 1120.01-A Seal bearing spacer.PDF

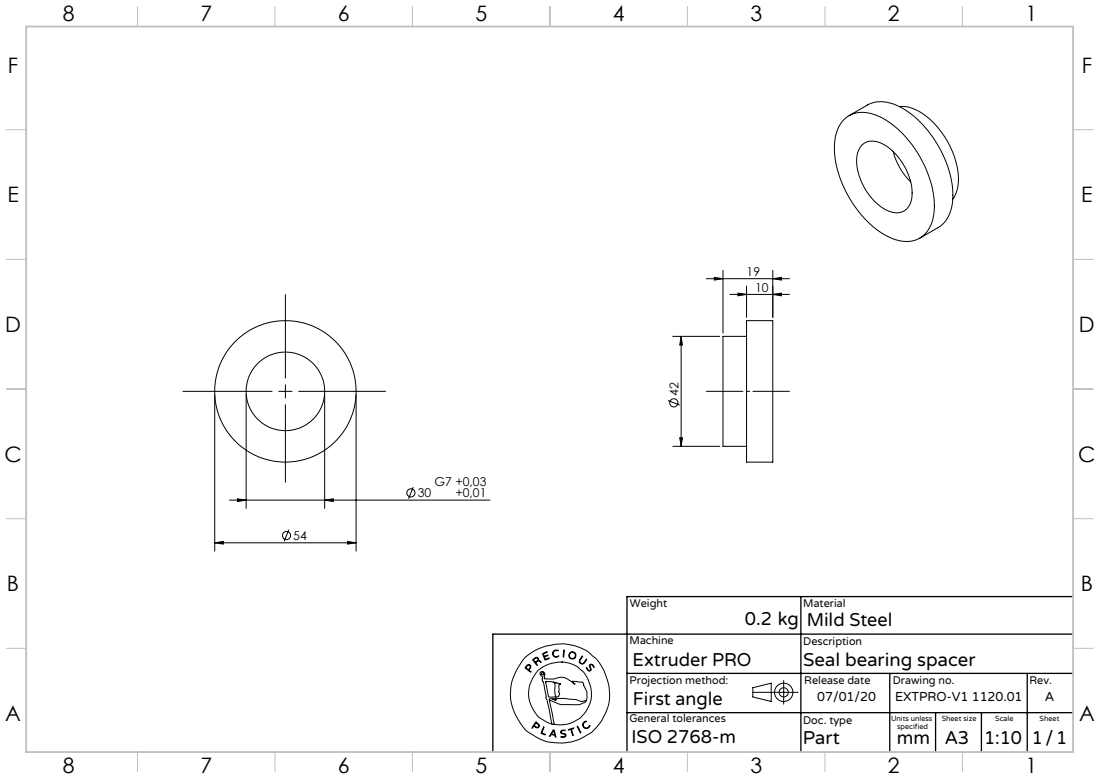
[picture p143: page 1]

Weight 0.2 kg | Material Mild Steel

Machine Extruder PRO | Description Seal bearing spacer
Projection method: First angle | Release date 07/01/20 | Drawing no. EXTPRO-V1 1120.01 | Rev. A
General tolerances ISO 2768-m | Doc. type Part | Units unless specified mm | Sheet size A3 | Scale 1:10 | Sheet 1 1 /
