ONEARMY/Precious-plastic-starterkit-extrusion/3. Build the machine/Extrusion-Pro-Files/3-2D blueprints/EXTPRO-V1 1120.02-A Coupling shaft.PDF

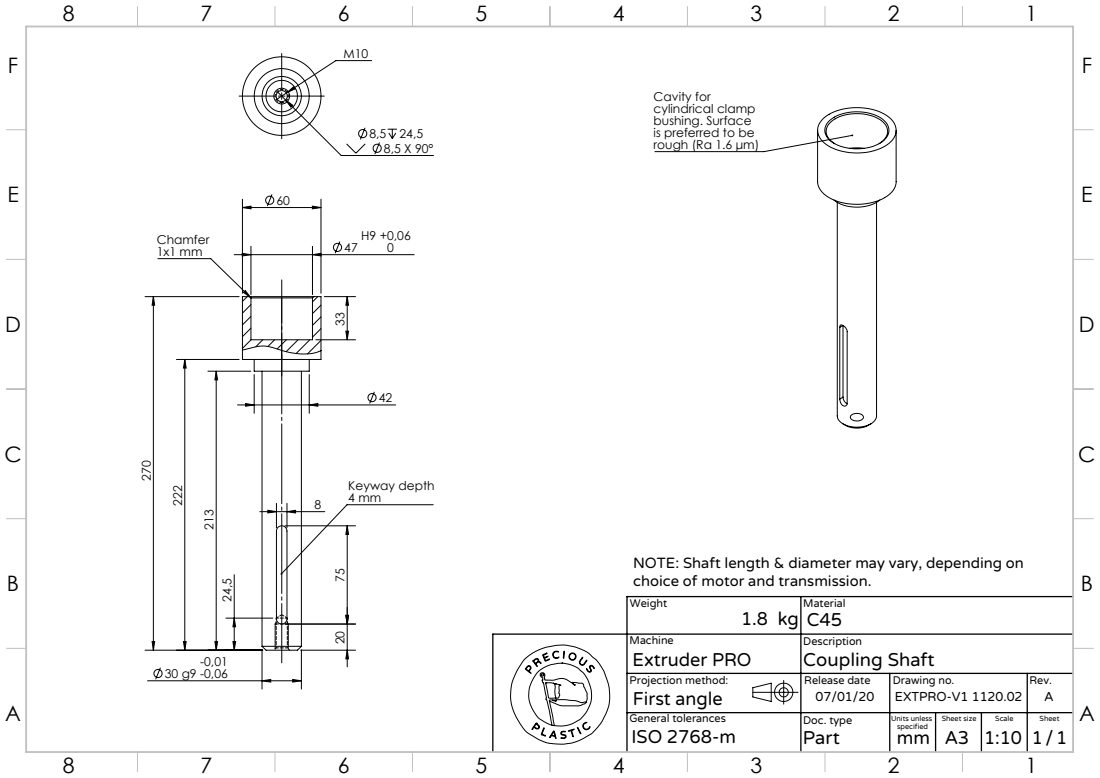
[picture p144: page 1]
Keyway depth 4 mm

Cavity for
cylindrical clamp
bushing. Surface
is preferred to be
rough (Ra 1.6 μm)

NOTE: Shaft length & diameter may vary, depending on
choice of motor and transmission.

Weight 1.8 kg | Material C45

Machine Extruder PRO | Description Coupling Shaft
Projection method: First angle | Release date 07/01/20 | Drawing no. EXTPRO-V1 1120.02 | Rev. A
General tolerances ISO 2768-m | Doc. type Part | Units unless specified mm | Sheet size A3 | Scale 1:10 | Sheet 1 1 /
