ONEARMY/Precious-plastic-starterkit-extrusion/3. Build the machine/Extrusion-Pro-Files/3-2D blueprints/EXTPRO-V1 1121.00-A Bearing Body.PDF

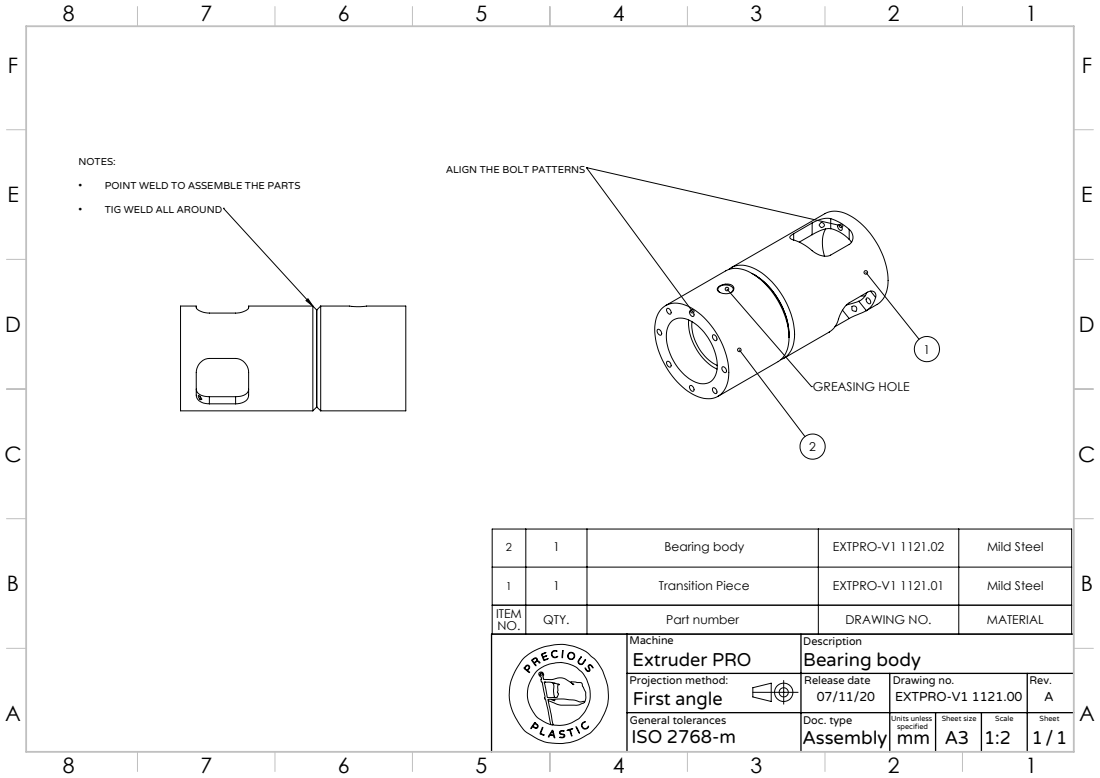
[picture p145: page 1]
GREASING HOLE; First angle; Projection method:

ALIGN THE BOLT PATTERNS

• POINT WELD TO ASSEMBLE THE PARTS

• TIG WELD ALL AROUND

2 | 1 | Bearing body | EXTPRO-V1 1121.02 | Mild Steel

1 | 1 | Transition Piece | EXTPRO-V1 1121.01 | Mild Steel
ITEM NO. | QTY. | Part number | DRAWING NO. | MATERIAL

Machine Extruder PRO | Description Bearing body

Release date 07/11/20 | Drawing no. EXTPRO-V1 1121.00 | Rev. A

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
