ONEARMY/Precious-plastic-starterkit-extrusion/3. Build the machine/Extrusion-Pro-Files/3-2D blueprints/EXTPRO-V1 1121.01-A Transition Piece.PDF

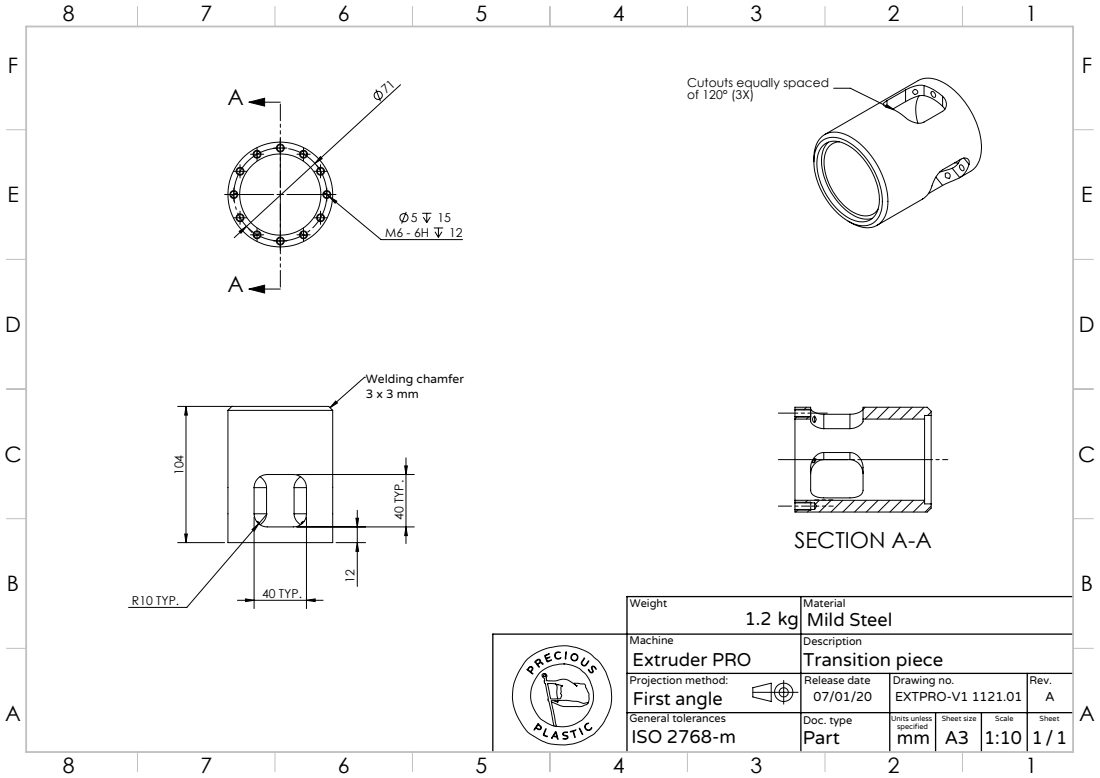
[picture p146: page 1]
SECTION A-A; 40 TYP.; R10 TYP.; Welding chamfer 3 x 3 mm

Cutouts equally spaced

Weight 1.2 kg | Material Mild Steel

Machine Extruder PRO | Description Transition piece
Projection method: First angle | Release date 07/01/20 | Drawing no. EXTPRO-V1 1121.01 | Rev. A
General tolerances ISO 2768-m | Doc. type Part | Units unless specified mm | Sheet size A3 | Scale 1:10 | Sheet 1 1 /
