ONEARMY/Precious-plastic-starterkit-extrusion/3. Build the machine/Extrusion-Pro-Files/3-2D blueprints/EXTPRO-V1 1121.02-A Bearing body.PDF

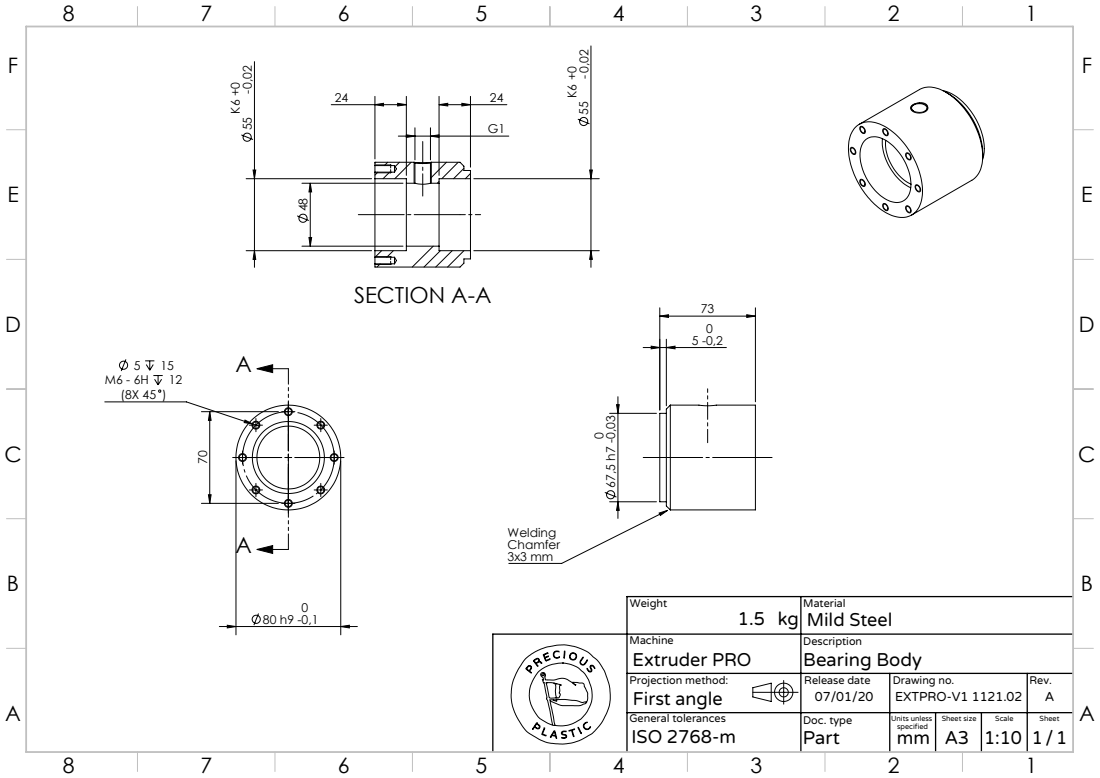
[picture p147: page 1]
SECTION A-A

Weight 1.5 kg | Material Mild Steel

Machine Extruder PRO | Description Bearing Body
Projection method: First angle | Release date 07/01/20 | Drawing no. EXTPRO-V1 1121.02 | Rev. A
General tolerances ISO 2768-m | Doc. type Part | Units unless specified mm | Sheet size A3 | Scale 1:10 | Sheet 1 1 /
