ONEARMY/Precious-plastic-starterkit-extrusion/3. Build the machine/Extrusion-Pro-Files/3-2D blueprints/EXTPRO-V1 1130.00-A Barrel inlet.PDF

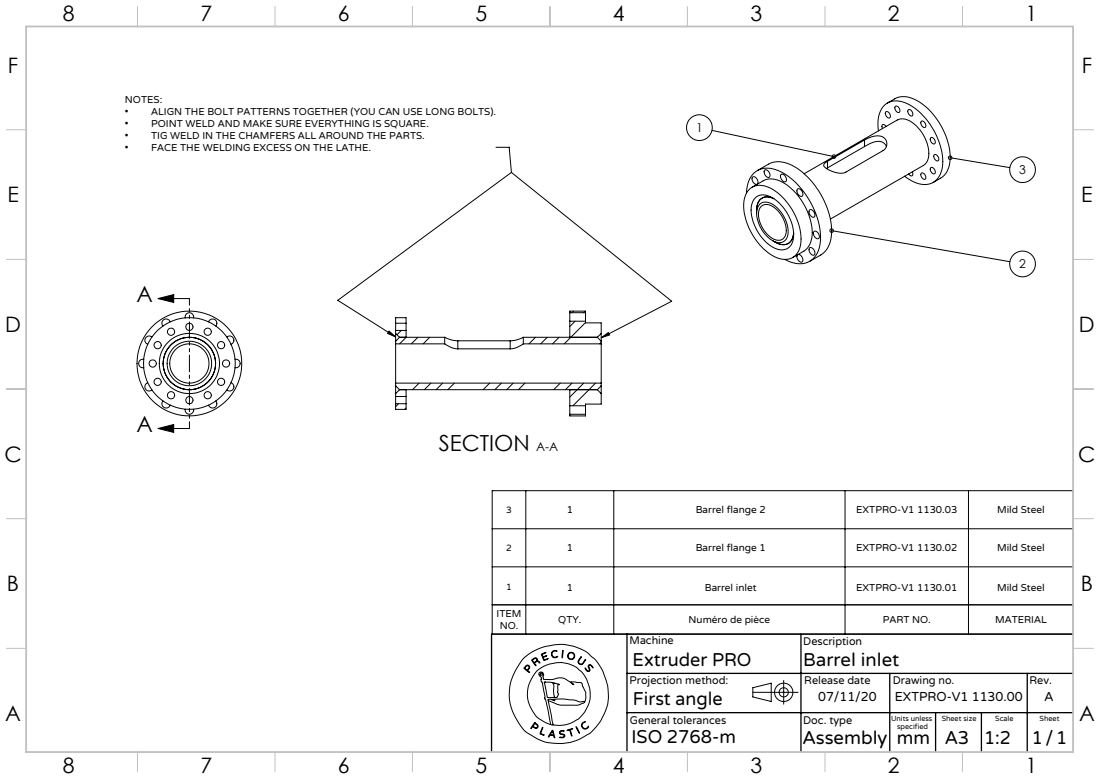
[picture p148: page 1]
SECTION A-A; First angle; Projection method:

NOTES:
• ALIGN THE BOLT PATTERNS TOGETHER (YOU CAN USE LONG BOLTS).
• POINT WELD AND MAKE SURE EVERYTHING IS SQUARE.
• TIG WELD IN THE CHAMFERS ALL AROUND THE PARTS.
• FACE THE WELDING EXCESS ON THE LATHE.

3 | 1 | Barrel flange 2 | EXTPRO-V1 1130.03 | Mild Steel

2 | 1 | Barrel flange 1 | EXTPRO-V1 1130.02 | Mild Steel

1 | 1 | Barrel inlet | EXTPRO-V1 1130.01 | Mild Steel

ITEM NO. | QTY. | Numéro de pièce | PART NO. | MATERIAL

Machine Extruder PRO | Description Barrel inlet

Release date 07/11/20 | Drawing no. EXTPRO-V1 1130.00 | Rev. A

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
