ONEARMY/Precious-plastic-starterkit-extrusion/3. Build the machine/Extrusion-Pro-Files/3-2D blueprints/EXTPRO-V1 1130.01-A Barrel inlet.PDF

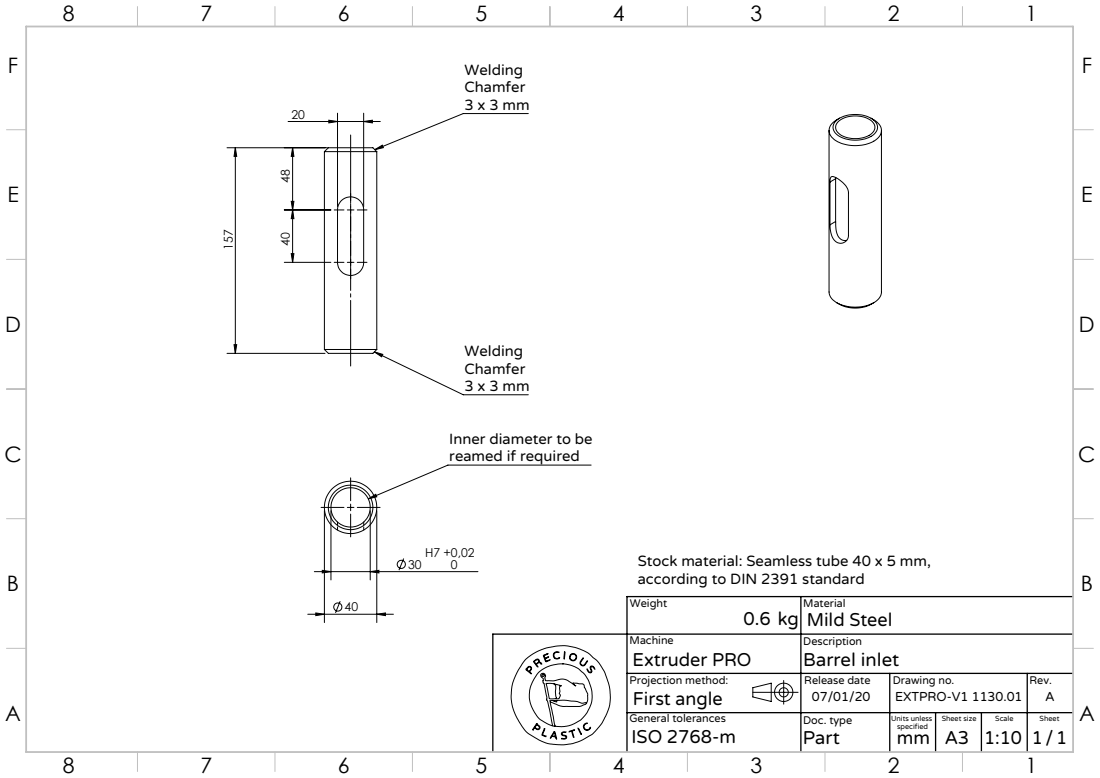
[picture p149: page 1]

Inner diameter to be
reamed if required

Stock material: Seamless tube 40 x 5 mm,
according to DIN 2391 standard

Weight 0.6 kg | Material Mild Steel

Machine Extruder PRO | Description Barrel inlet
Projection method: First angle | Release date 07/01/20 | Drawing no. EXTPRO-V1 1130.01 | Rev. A
General tolerances ISO 2768-m | Doc. type Part | Units unless specified mm | Sheet size A3 | Scale 1:10 | Sheet 1 1 /
