ONEARMY/Precious-plastic-starterkit-extrusion/3. Build the machine/Extrusion-Pro-Files/3-2D blueprints/EXTPRO-V1 1130.02-A Barrel flange 1.PDF

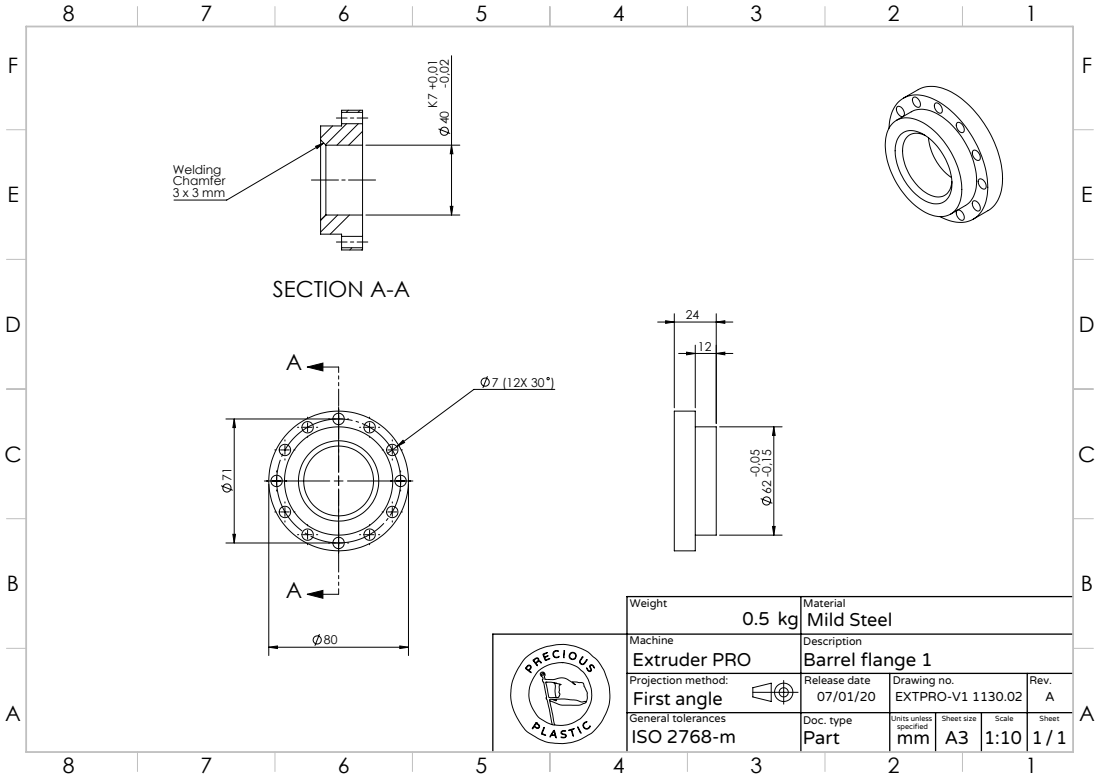
[picture p150: page 1]
SECTION A-A

Weight 0.5 kg | Material Mild Steel

Machine Extruder PRO | Description Barrel flange 1
Projection method: First angle | Release date 07/01/20 | Drawing no. EXTPRO-V1 1130.02 | Rev. A
General tolerances ISO 2768-m | Doc. type Part | Units unless specified mm | Sheet size A3 | Scale 1:10 | Sheet 1 1 /
