ONEARMY/Precious-plastic-starterkit-extrusion/3. Build the machine/Extrusion-Pro-Files/3-2D blueprints/EXTPRO-V1 1130.03-A Barrel flange 2.PDF

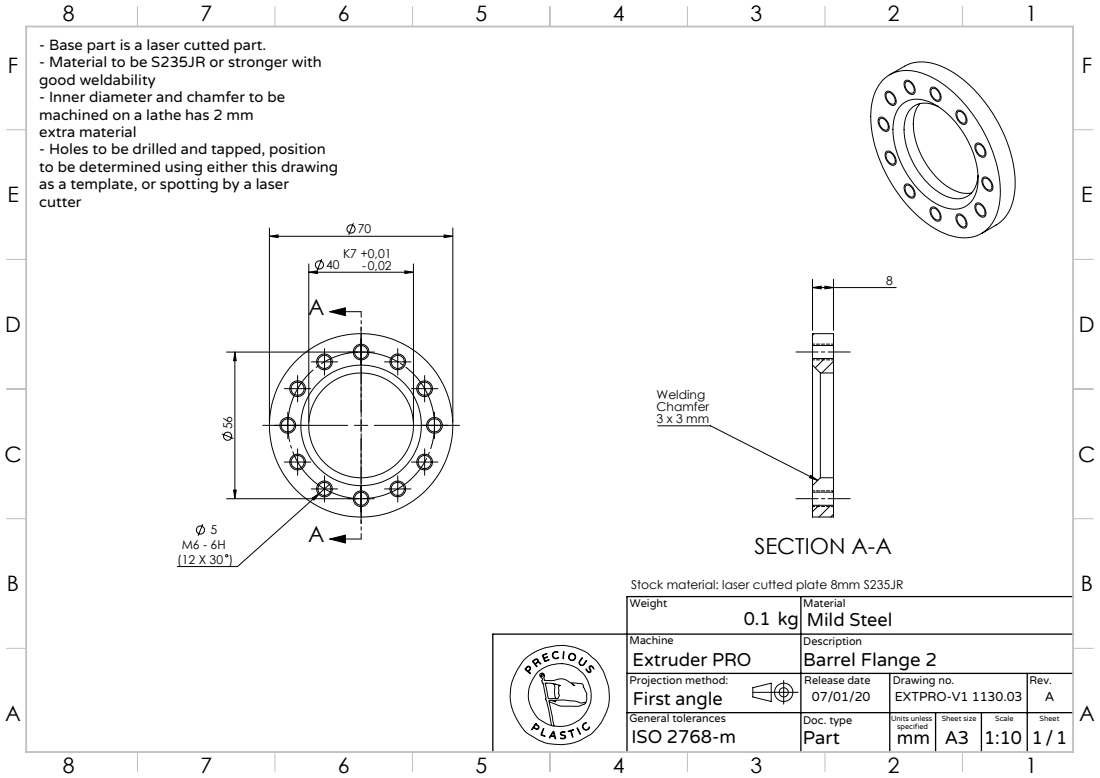
[picture p151: page 1]
SECTION A-A

- Material to be S235JR or stronger with
good weldability
- Inner diameter and chamfer to be
machined on a lathe has 2 mm
extra material
- Holes to be drilled and tapped, position
to be determined using either this drawing
as a template, or spotting by a laser
cutter

- Base part is a laser cutted part.

Stock material: laser cutted plate 8mm S235JR

Weight 0.1 kg | Material Mild Steel

Machine Extruder PRO | Description Barrel Flange 2
Projection method: First angle | Release date 07/01/20 | Drawing no. EXTPRO-V1 1130.03 | Rev. A
General tolerances ISO 2768-m | Doc. type Part | Units unless specified mm | Sheet size A3 | Scale 1:10 | Sheet 1 1 /
