ONEARMY/Precious-plastic-starterkit-extrusion/3. Build the machine/Extrusion-Pro-Files/3-2D blueprints/EXTPRO-V1 1140.00-A Barrel.PDF

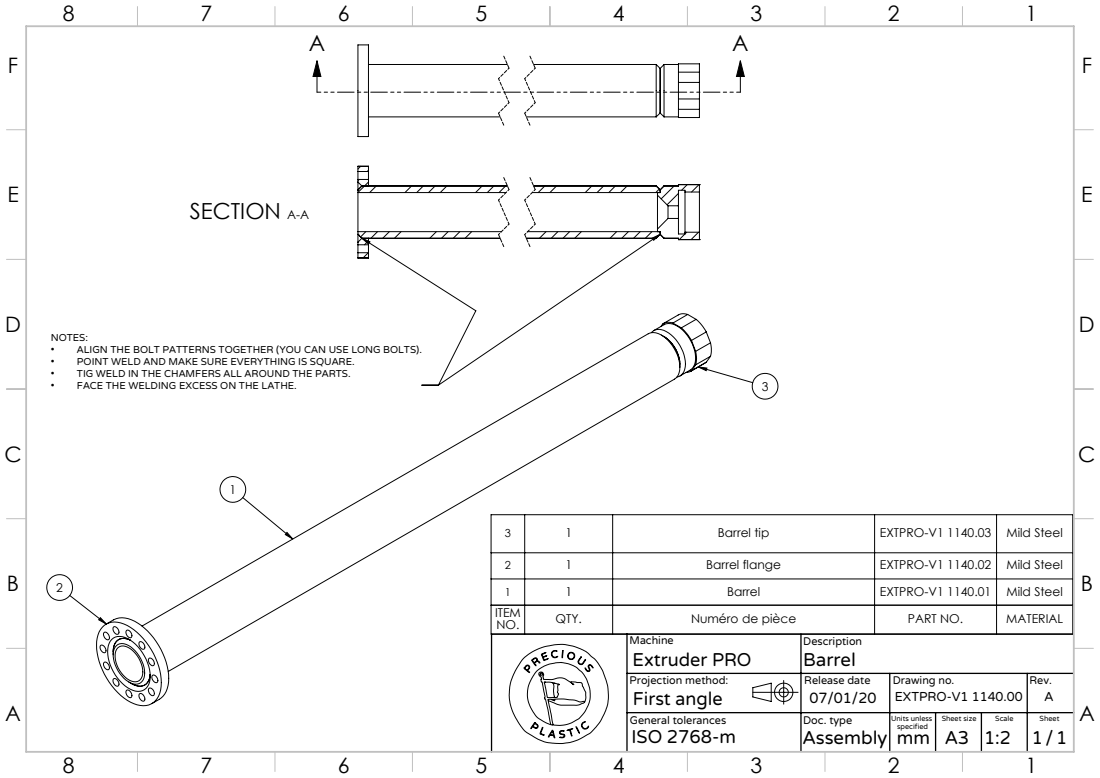
[picture p152: page 1]
SECTION A-A; First angle; Projection method:

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

3 | 1 | Barrel tip | EXTPRO-V1 1140.03 | Mild Steel

2 | 1 | Barrel flange | EXTPRO-V1 1140.02 | Mild Steel
1 | 1 | Barrel | EXTPRO-V1 1140.01 | Mild Steel
ITEM NO. | QTY. | Numéro de pièce | PART NO. | MATERIAL

Machine Extruder PRO | Description Barrel

Release date 07/01/20 | Drawing no. EXTPRO-V1 1140.00 | Rev. A

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
