ONEARMY/Precious-plastic-starterkit-extrusion/3. Build the machine/Extrusion-Pro-Files/3-2D blueprints/EXTPRO-V1 1140.01-A Barrel.PDF

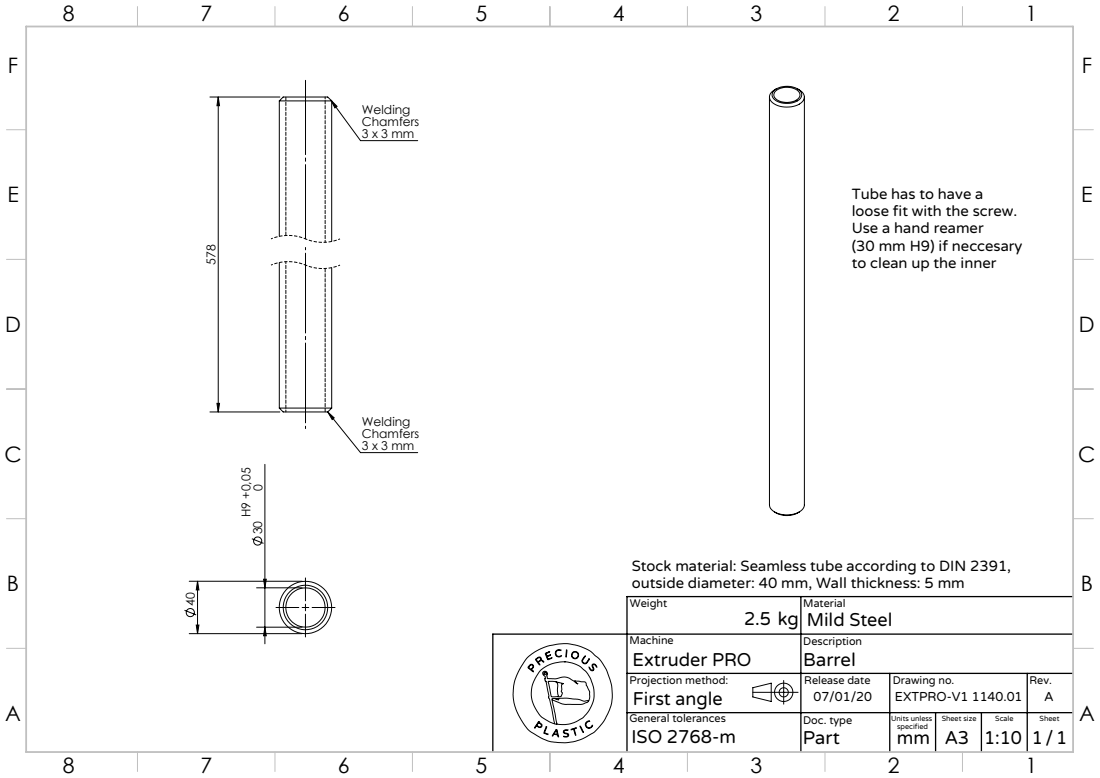
[picture p153: page 1]

Tube has to have a
loose fit with the screw.
Use a hand reamer
(30 mm H9) if neccesary
to clean up the inner

Stock material: Seamless tube according to DIN 2391,
outside diameter: 40 mm, Wall thickness: 5 mm

Weight 2.5 kg | Material Mild Steel

Machine Extruder PRO | Description Barrel
Projection method: First angle | Release date 07/01/20 | Drawing no. EXTPRO-V1 1140.01 | Rev. A
General tolerances ISO 2768-m | Doc. type Part | Units unless specified mm | Sheet size A3 | Scale 1:10 | Sheet 1 1 /
