ONEARMY/Precious-plastic-starterkit-extrusion/3. Build the machine/Extrusion-Pro-Files/3-2D blueprints/EXTPRO-V1 1140.03-A Barrel tip.PDF

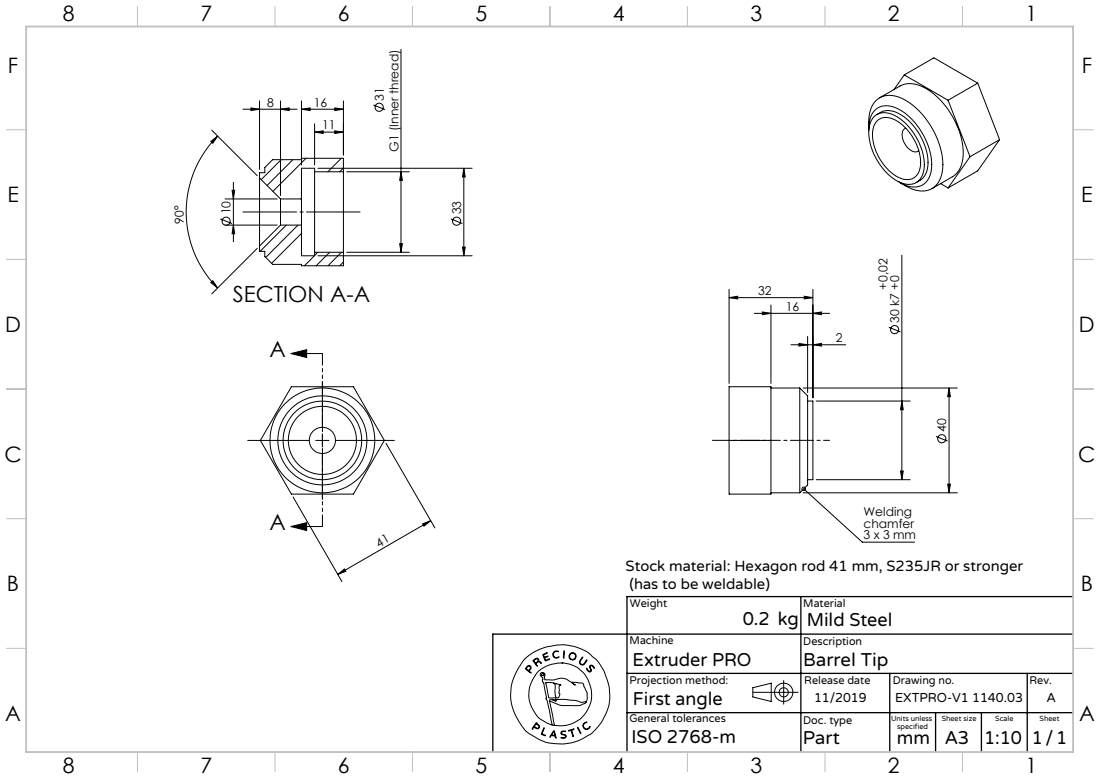
[picture p154: page 1]
G1 (Inner thread); SECTION A-A

Stock material: Hexagon rod 41 mm, S235JR or stronger
(has to be weldable)

Weight 0.2 kg | Material Mild Steel

Machine Extruder PRO | Description Barrel Tip
Projection method: First angle | Release date 11/2019 | Drawing no. EXTPRO-V1 1140.03 | Rev. A
General tolerances ISO 2768-m | Doc. type Part | Units unless specified mm | Sheet size A3 | Scale 1:10 | Sheet 1 1 /
