ONEARMY/Precious-plastic-starterkit-extrusion/3. Build the machine/Extrusion-Pro-Files/3-2D blueprints/EXTPRO-V1 1200.01-A - Top.PDF

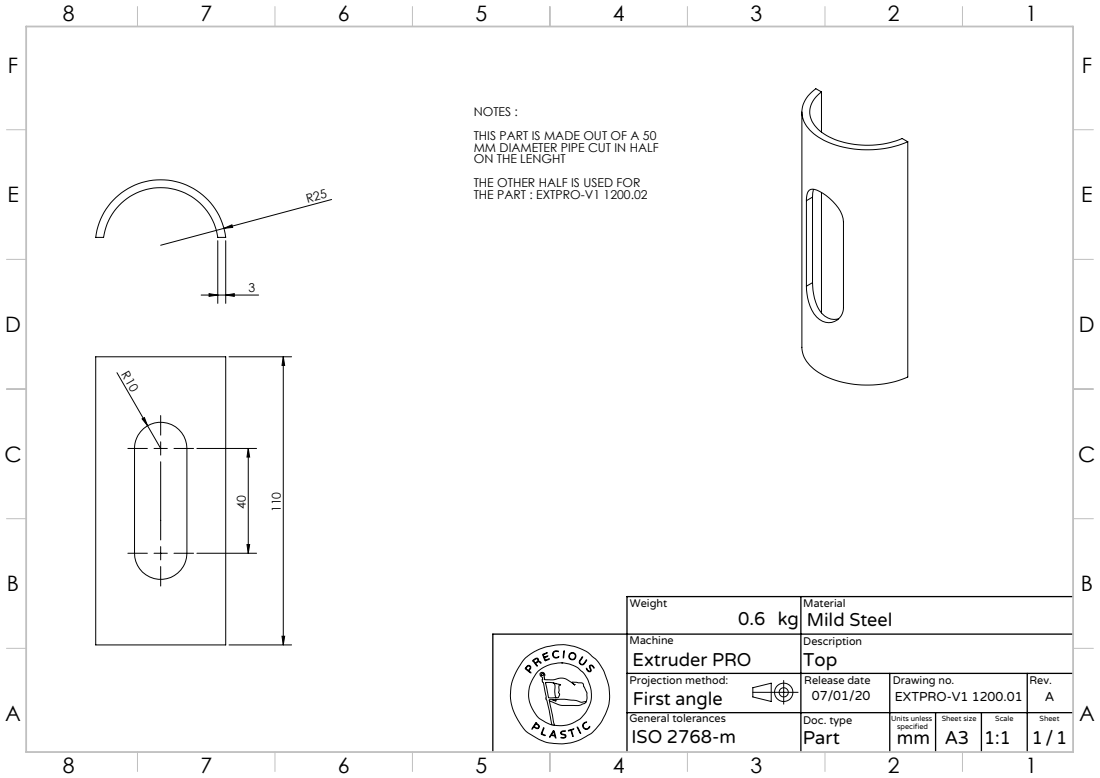
[picture p156: page 1]

NOTES :
THIS PART IS MADE OUT OF A 50
MM DIAMETER PIPE CUT IN HALF
ON THE LENGHT
THE OTHER HALF IS USED FOR
THE PART : EXTPRO-V1 1200.02

Weight 0.6 kg | Material Mild Steel

Machine Extruder PRO | Description Top
Projection method: First angle | Release date 07/01/20 | Drawing no. EXTPRO-V1 1200.01 | Rev. A
General tolerances ISO 2768-m | Doc. type Part | Units unless specified mm | Sheet size A3 | Scale 1:1 | Sheet 1 1 /
