ONEARMY/Precious-plastic-starterkit-extrusion/3. Build the machine/Extrusion-Pro-Files/3-2D blueprints/EXTPRO-V1 1200.02-A - Bottom.PDF

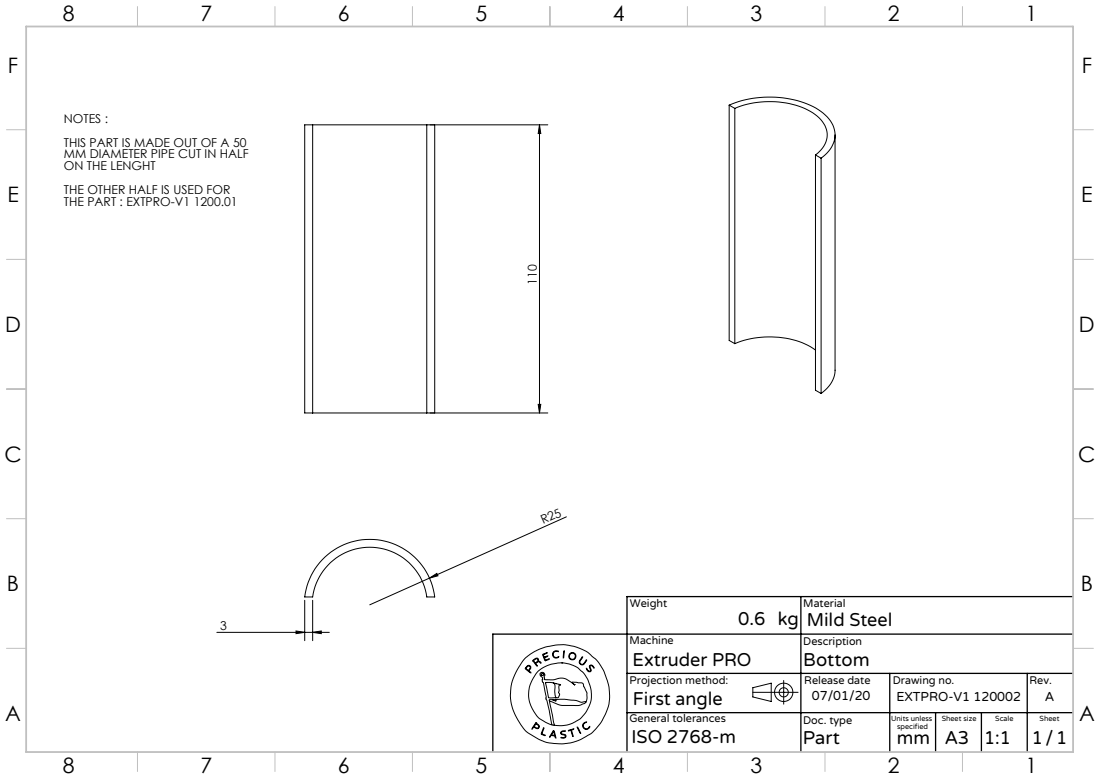
[picture p157: page 1]
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

THE OTHER HALF IS USED FOR
THE PART : EXTPRO-V1 1200.01

Weight 0.6 kg | Material Mild Steel

Machine Extruder PRO | Description Bottom
Projection method: First angle | Release date 07/01/20 | Drawing no. EXTPRO-V1 120002 | Rev. A
General tolerances ISO 2768-m | Doc. type Part | Units unless specified mm | Sheet size A3 | Scale 1:1 | Sheet 1 1 /
