ONEARMY/Precious-plastic-starterkit-extrusion/3. Build the machine/Extrusion-Pro-Files/3-2D blueprints/EXTPRO-V1 1200.03-A Insulation.PDF

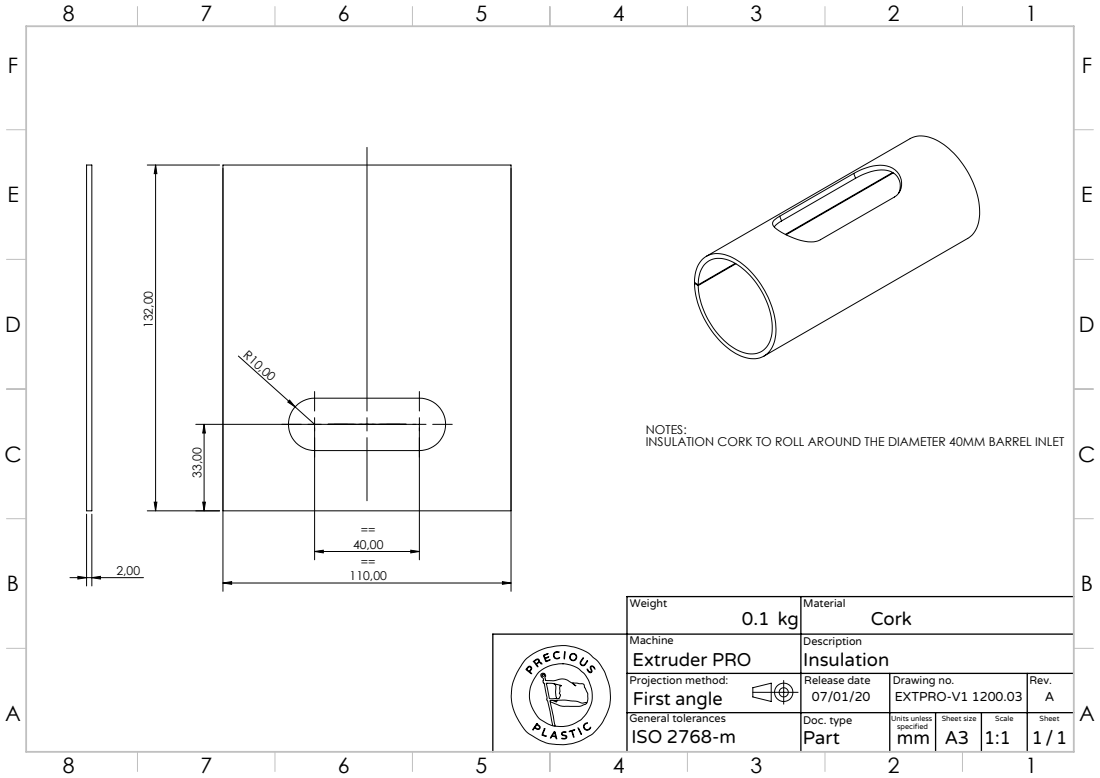
[picture p158: page 1]

NOTES:
INSULATION CORK TO ROLL AROUND THE DIAMETER 40MM BARREL INLET

Weight 0.1 | Material Cork kg

Machine Extruder PRO | Description Insulation
Projection method: First angle | Release date 07/01/20 | Drawing no. EXTPRO-V1 1200.03 | Rev. A
General tolerances ISO 2768-m | Doc. type Part | Units unless specified mm | Sheet size A3 | Scale 1:1 | Sheet 1 1 /
