ONEARMY/Precious-plastic-starterkit-extrusion/3. Build the machine/Extrusion-Pro-Files/3-2D blueprints/EXTPRO-V1 1200.04-A - Cone hopper.PDF

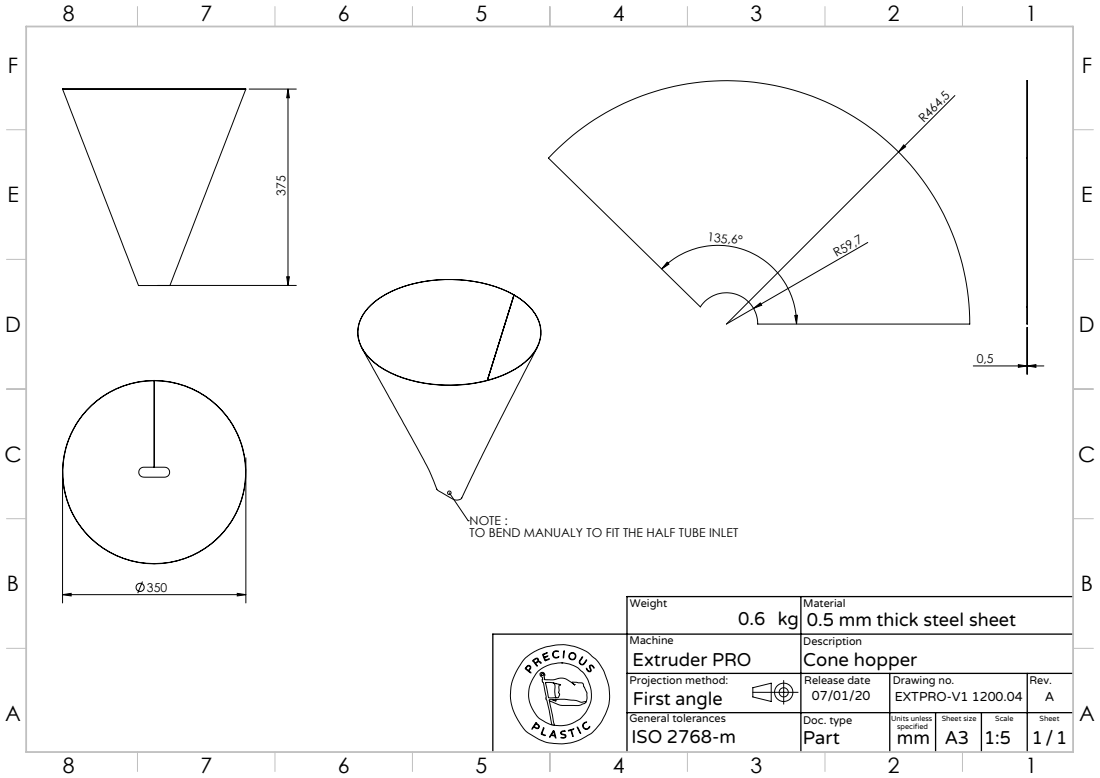
[picture p159: page 1]

NOTE :
TO BEND MANUALY TO FIT THE HALF TUBE INLET

Weight 0.6 kg | Material 0.5 mm thick steel sheet

Machine Extruder PRO | Description Cone hopper
Projection method: First angle | Release date 07/01/20 | Drawing no. EXTPRO-V1 1200.04 | Rev. A
General tolerances ISO 2768-m | Doc. type Part | Units unless specified mm | Sheet size A3 | Scale 1:5 | Sheet 1 1 /
