ONEARMY/Precious-plastic-starterkit-extrusion/3. Build the machine/Extrusion-Pro-Files/3-2D blueprints/EXTPRO-V1 2000.01-A Electronics box support.PDF

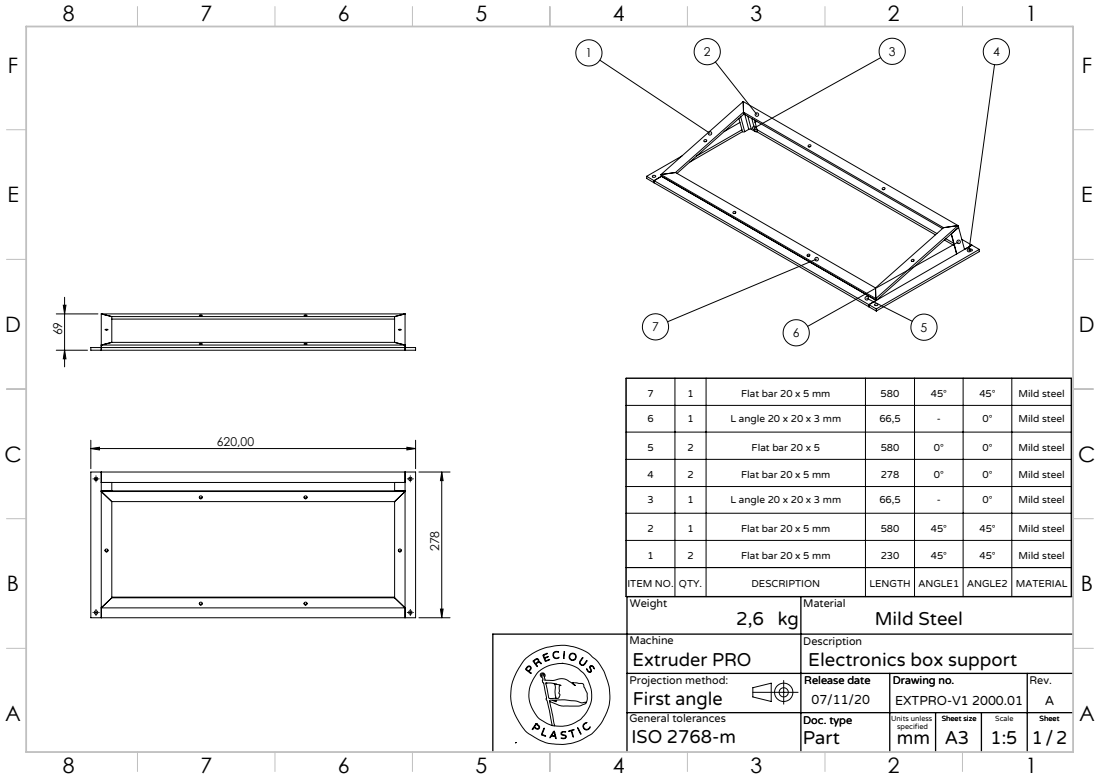
[picture p160: page 1]
First angle; Projection method:

7 | 1 | Flat bar 20 x 5 mm | 580 | 45° | 45° | Mild steel

6 | 1 | L angle 20 x 20 x 3 mm | 66,5 | - | 0° | Mild steel

5 | 2 | Flat bar 20 x 5 | 580 | 0° | 0° | Mild steel

4 | 2 | Flat bar 20 x 5 mm | 278 | 0° | 0° | Mild steel

3 | 1 | L angle 20 x 20 x 3 mm | 66,5 | - | 0° | Mild steel

2 | 1 | Flat bar 20 x 5 mm | 580 | 45° | 45° | Mild steel

1 | 2 | Flat bar 20 x 5 mm | 230 | 45° | 45° | Mild steel

ITEM NO. | QTY. | DESCRIPTION | LENGTH | ANGLE1 | ANGLE2 | MATERIAL
Weight 2,6 kg | Material Mild Steel
Machine Extruder PRO | Description Electronics box support

Release date Release date 07/11/20 | Drawing no. Drawing no. EXTPRO-V1 2000.01 | Rev. A

General tolerances ISO 2768-m | Doc. type Doc. type Part | Units unless specified mm | Sheet size Sheet size A3 | Scale 1:5 | Sheet Sheet 1 2 /

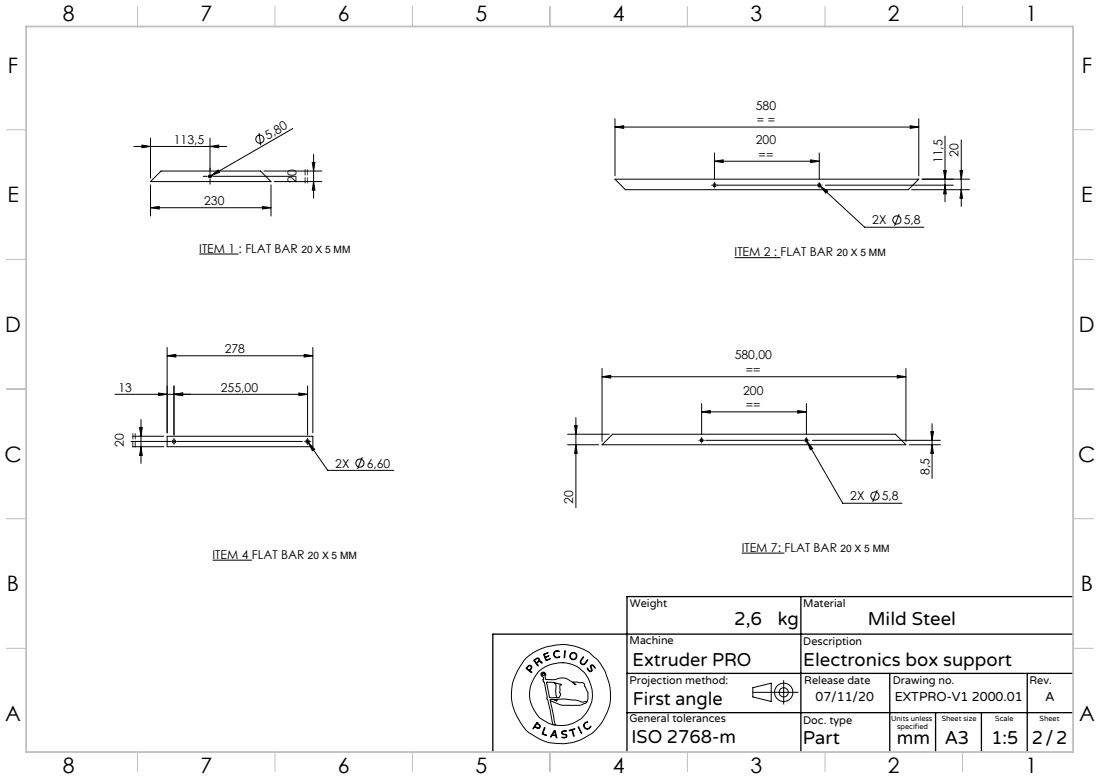
[picture p161: page 2]
ITEM 1 : FLAT BAR 20 X 5 MM; ITEM 2 : FLAT BAR 20 X 5 MM; First angle; Projection method:

ITEM 7: FLAT BAR 20 X 5 MM ITEM 4 FLAT BAR 20 X 5 MM

Weight 2,6 kg | Material Mild Steel

Machine Extruder PRO | Description Electronics box support

Release date 07/11/20 | Drawing no. EXTPRO-V1 2000.01 | Rev. A

General tolerances ISO 2768-m | Doc. type Part | Units unless specified mm | Sheet size A3 | Scale 1:5 | Sheet 2 2 /
