ONEARMY/Precious-plastic-starterkit-extrusion/3. Build the machine/Extrusion-Pro-Files/3-2D blueprints/EXTPRO-V1 3000.00-A Frame.PDF

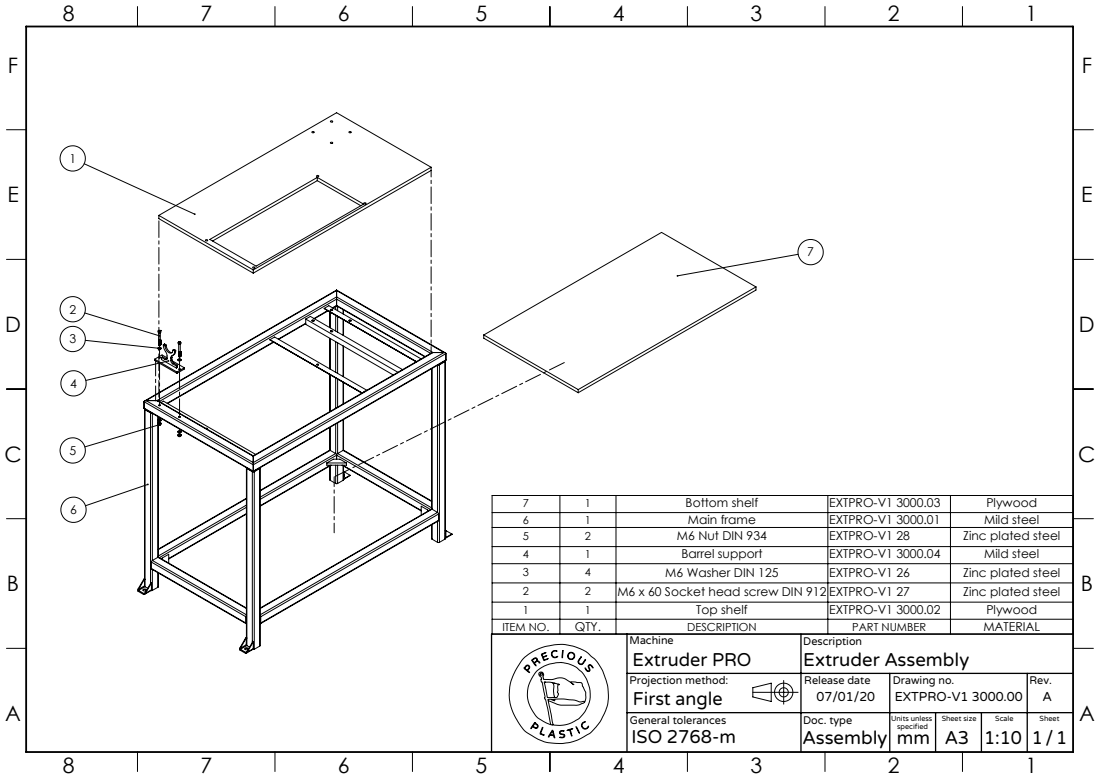
[picture p163: page 1]

7 | 1 | Bottom shelf | EXTPRO-V1 3000.03 | Plywood
6 | 1 | Main frame | EXTPRO-V1 3000.01 | Mild steel
5 | 2 | M6 Nut DIN 934 | EXTPRO-V1 28 | Zinc plated steel
4 | 1 | Barrel support | EXTPRO-V1 3000.04 | Mild steel
3 | 4 | M6 Washer DIN 125 | EXTPRO-V1 26 | Zinc plated steel
2 | 2 | M6 x 60 Socket head screw DIN 912 EXTPRO-V1 27 | | Zinc plated steel
1 | 1 | Top shelf | EXTPRO-V1 3000.02 | Plywood
ITEM NO. | QTY. | DESCRIPTION | PART NUMBER | MATERIAL

Machine Extruder PRO | Description Extruder Assembly
Projection method: First angle | Release date 07/01/20 | Drawing no. EXTPRO-V1 3000.00 | Rev. A
General tolerances ISO 2768-m | Doc. type Assembly | Units unless specified mm | Sheet size A3 | Scale 1:10 | Sheet 1 1 /
