ONEARMY/Precious-plastic-starterkit-extrusion/3. Build the machine/Extrusion-Pro-Files/3-2D blueprints/EXTPRO-V1 3000.01-A Main frame.PDF

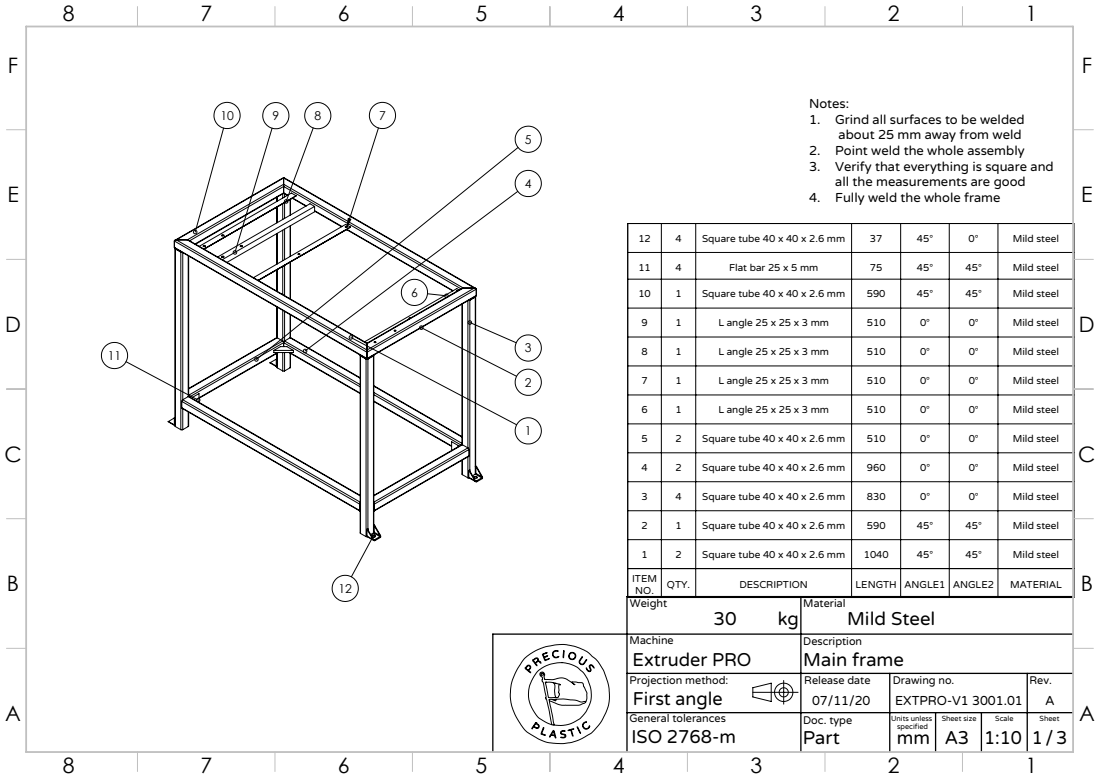
[picture p164: page 1]

Notes:
1. Grind all surfaces to be welded
about 25 mm away from weld
2. Point weld the whole assembly
3. Verify that everything is square and
all the measurements are good
4. Fully weld the whole frame

12 | 4 | Square tube 40 x 40 x 2.6 mm | 37 | 45° | 0° | Mild steel

11 | 4 | Flat bar 25 x 5 mm | 75 | 45° | 45° | Mild steel

10 | 1 | Square tube 40 x 40 x 2.6 mm | 590 | 45° | 45° | Mild steel

9 | 1 | L angle 25 x 25 x 3 mm | 510 | 0° | 0° | Mild steel

8 | 1 | L angle 25 x 25 x 3 mm | 510 | 0° | 0° | Mild steel

7 | 1 | L angle 25 x 25 x 3 mm | 510 | 0° | 0° | Mild steel

6 | 1 | L angle 25 x 25 x 3 mm | 510 | 0° | 0° | Mild steel

5 | 2 | Square tube 40 x 40 x 2.6 mm | 510 | 0° | 0° | Mild steel

4 | 2 | Square tube 40 x 40 x 2.6 mm | 960 | 0° | 0° | Mild steel

3 | 4 | Square tube 40 x 40 x 2.6 mm | 830 | 0° | 0° | Mild steel

2 | 1 | Square tube 40 x 40 x 2.6 mm | 590 | 45° | 45° | Mild steel

1 | 2 | Square tube 40 x 40 x 2.6 mm | 1040 | 45° | 45° | Mild steel

ITEM NO. | QTY. | DESCRIPTION | LENGTH | ANGLE1 | ANGLE2 | MATERIAL
Weight 30 | Material Mild Steel kg

Machine Extruder PRO | Description Main frame
Projection method: First angle | Release date 07/11/20 | Drawing no. EXTPRO-V1 3001.01 | Rev. A
General tolerances ISO 2768-m | Doc. type Part | Units unless specified mm | Sheet size A3 | Scale 1:10 | Sheet /

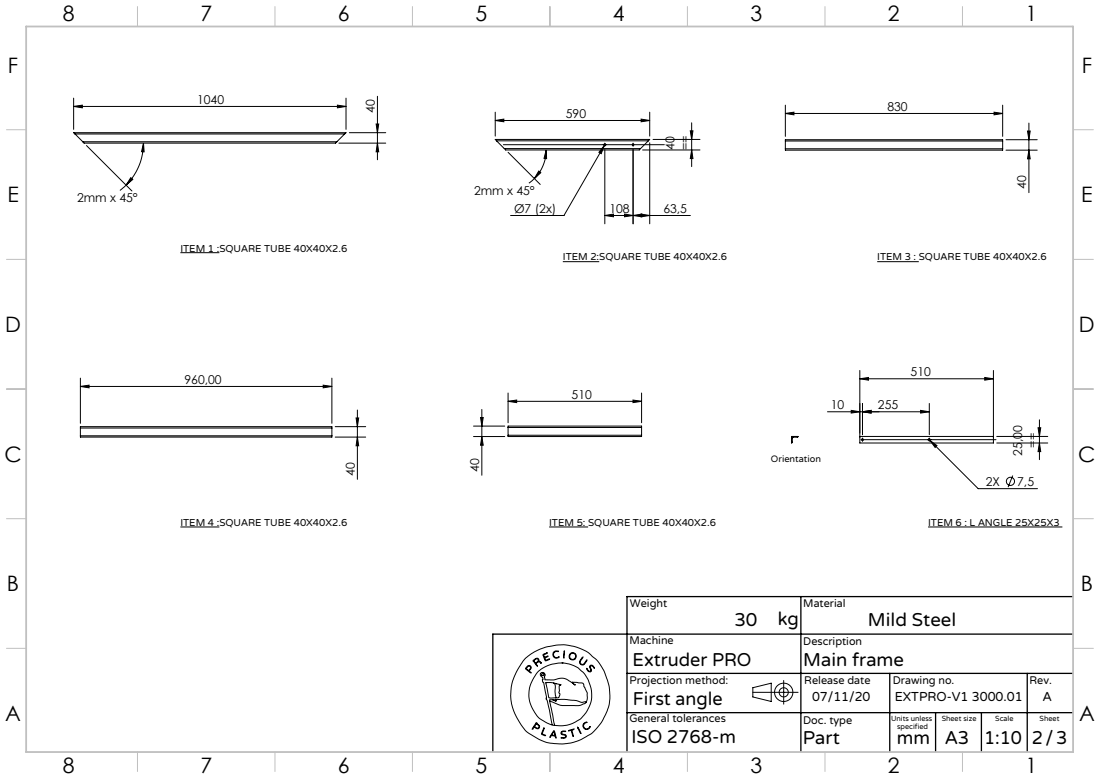
[picture p165: page 2]
ITEM 6 : L ANGLE 25X25X3; ITEM 4 :SQUARE TUBE 40X40X2.6; ITEM 5: SQUARE TUBE 40X40X2.6

ITEM 1 :SQUARE TUBE 40X40X2.6

ITEM 2:SQUARE TUBE 40X40X2.6

ITEM 3 : SQUARE TUBE 40X40X2.6

Weight 30 | Material Mild Steel kg

Machine Extruder PRO | Description Main frame
Projection method: First angle | Release date 07/11/20 | Drawing no. EXTPRO-V1 3000.01 | Rev. A

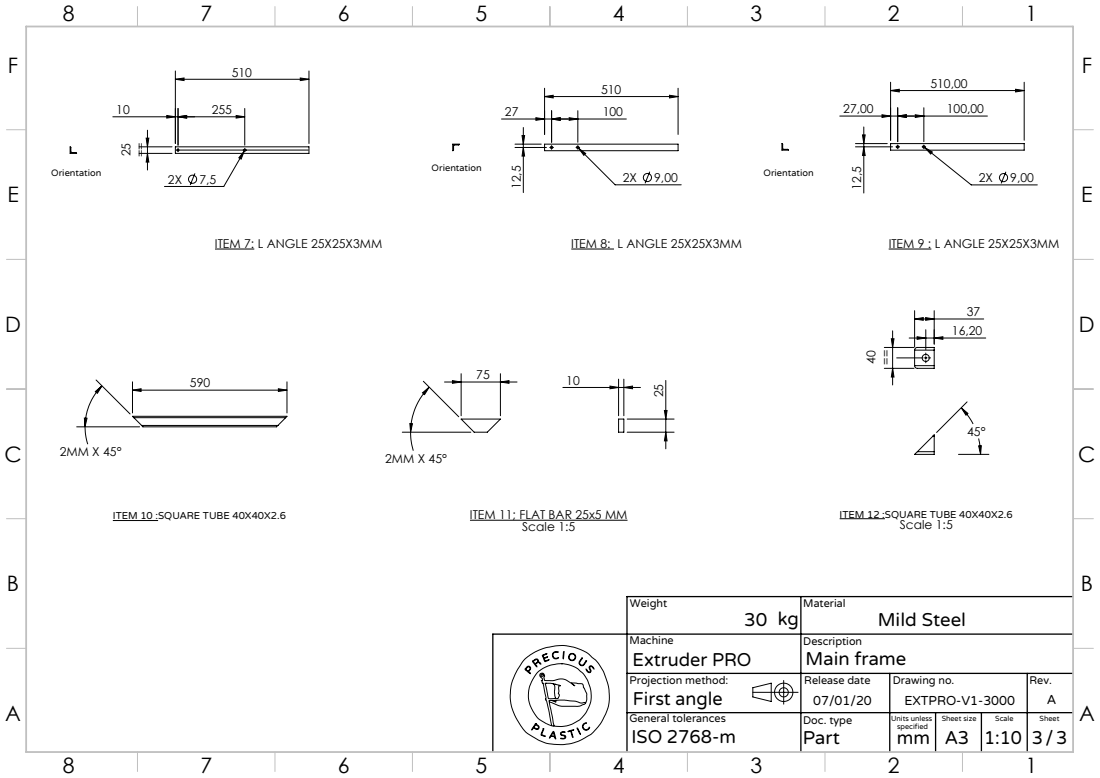
[picture p166: page 3]
ITEM 7: L ANGLE 25X25X3MM; ITEM 8: L ANGLE 25X25X3MM; ITEM 9 : L ANGLE 25X25X3MM; Scale 1:5

ITEM 11; FLAT BAR 25x5 MM

ITEM 10 :SQUARE TUBE 40X40X2.6

ITEM 12 :SQUARE TUBE 40X40X2.6

Weight 30 | Material Mild Steel kg

Machine Extruder PRO | Description Main frame
Projection method: First angle | Release date 07/01/20 | Drawing no. EXTPRO-V1-3000 | Rev. A
