ONEARMY/Precious-plastic-starterkit-extrusion/3. Build the machine/Extrusion-Pro-Files/3-2D blueprints/EXTPRO-V1 3000.02-A Top shelf.PDF

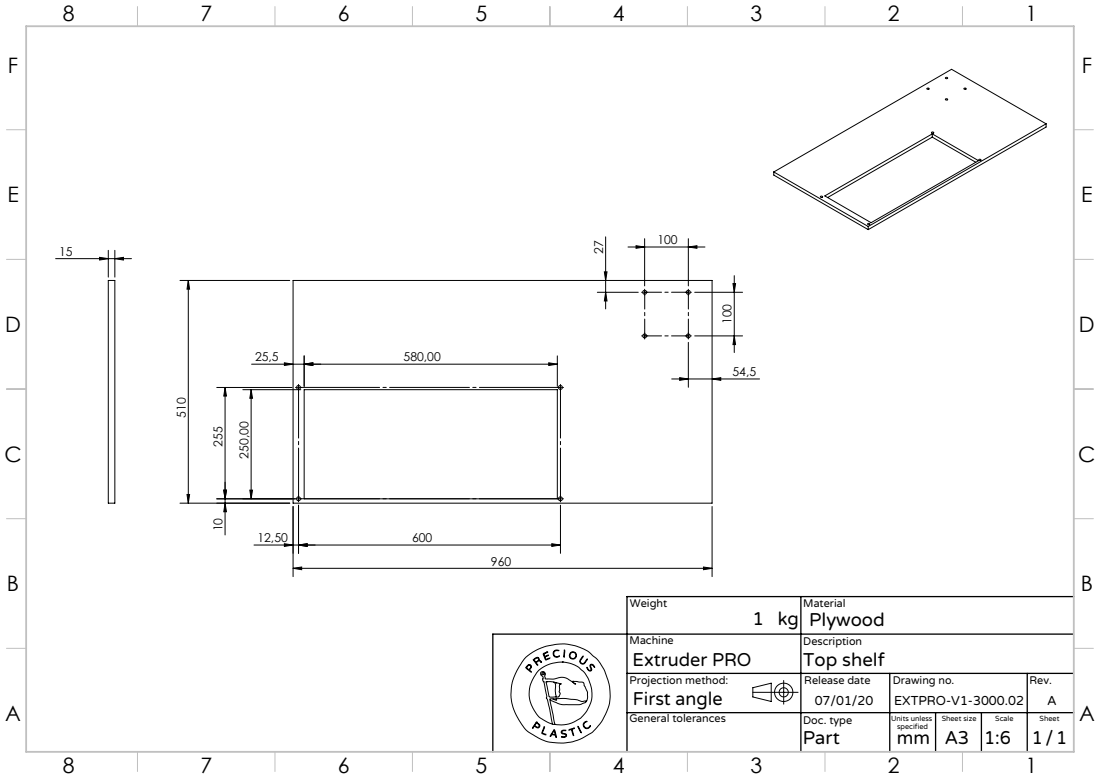
[picture p167: page 1]

Weight 1 kg | Material Plywood

Machine Extruder PRO | Description Top shelf
Projection method: First angle | Release date 07/01/20 | Drawing no. EXTPRO-V1-3000.02 | Rev. A
General tolerances | Doc. type Part | Units unless specified mm | Sheet size A3 | Scale 1:6 | Sheet 1 1 /
