ONEARMY/Precious-plastic-starterkit-extrusion/3. Build the machine/Extrusion-Pro-Files/3-2D blueprints/EXTPRO-V1 3000.03-A Bottom shelf.PDF

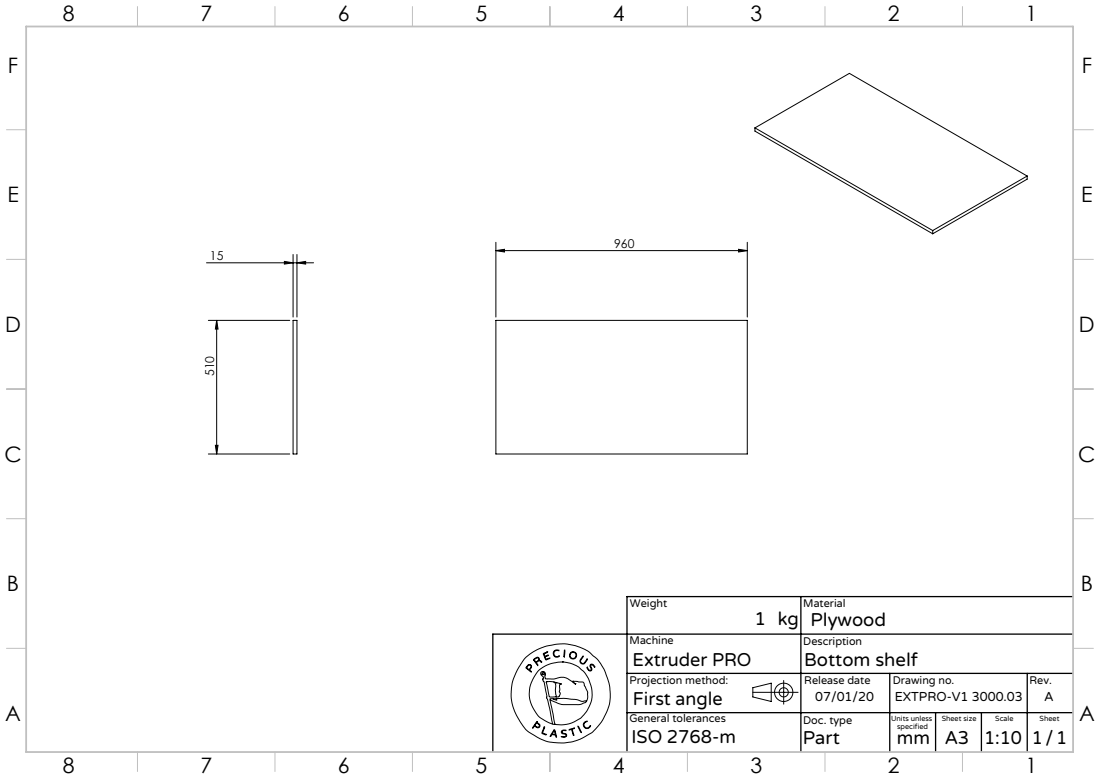
[picture p168: page 1]

Weight 1 kg | Material Plywood

Machine Extruder PRO | Description Bottom shelf
Projection method: First angle | Release date 07/01/20 | Drawing no. EXTPRO-V1 3000.03 | Rev. A
General tolerances ISO 2768-m | Doc. type Part | Units unless specified mm | Sheet size A3 | Scale 1:10 | Sheet 1 1 /
