ONEARMY/Precious-plastic-starterkit-extrusion/3. Build the machine/Upgrades/Barrel Support/3-2D bluprints/EXTPRO-V1-3000.05-A-Barrel-support-2.pdf

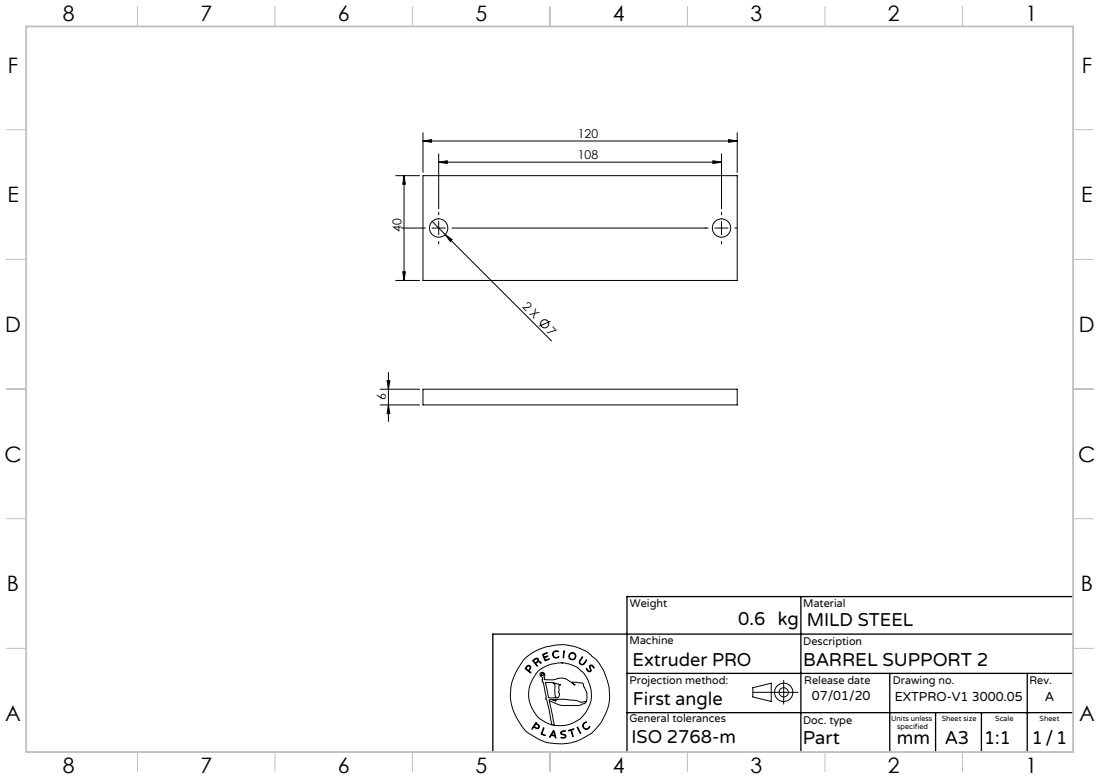
[picture p170: page 1]

Weight 0.6 kg | Material MILD STEEL

Machine Extruder PRO | Description BARREL SUPPORT 2
Projection method: First angle | Release date 07/01/20 | Drawing no. EXTPRO-V1 3000.05 | Rev. A
General tolerances ISO 2768-m | Doc. type Part | Units unless specified mm | Sheet size A3 | Scale 1:1 | Sheet 1 1 /
