ONEARMY/Precious-plastic-starterkit-extrusion/3. Build the machine/Upgrades/Heat Protection/2-2D Drawings/EXTPRO-V1 3000.06-A Heat protection.SLDDRW.PDF

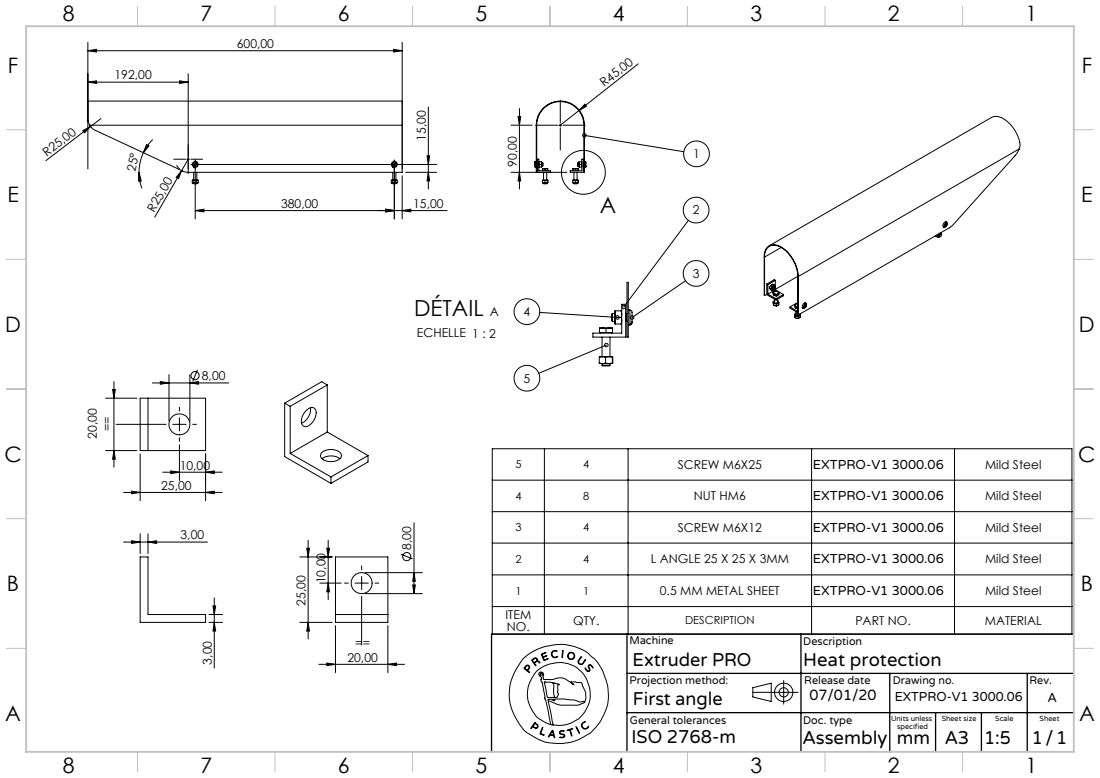
[picture p171: page 1]
DÉTAIL A; ECHELLE 1 : 2; First angle; Projection method:

5 | 4 | SCREW M6X25 | EXTPRO-V1 3000.06 | Mild Steel

4 | 8 | NUT HM6 | EXTPRO-V1 3000.06 | Mild Steel
3 | 4 | SCREW M6X12 | EXTPRO-V1 3000.06 | Mild Steel
2 | 4 | L ANGLE 25 X 25 X 3MM | EXTPRO-V1 3000.06 | Mild Steel

1 | 1 | 0.5 MM METAL SHEET | EXTPRO-V1 3000.06 | Mild Steel
ITEM NO. | QTY. | DESCRIPTION | PART NO. | MATERIAL

Machine Extruder PRO | Description Heat protection

Release date 07/01/20 | Drawing no. EXTPRO-V1 3000.06 | Rev. A

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
