ONEARMY/Precious-plastic-starterkit-extrusion/1. Learn about plastic/Visual-Properties_A1.pdf

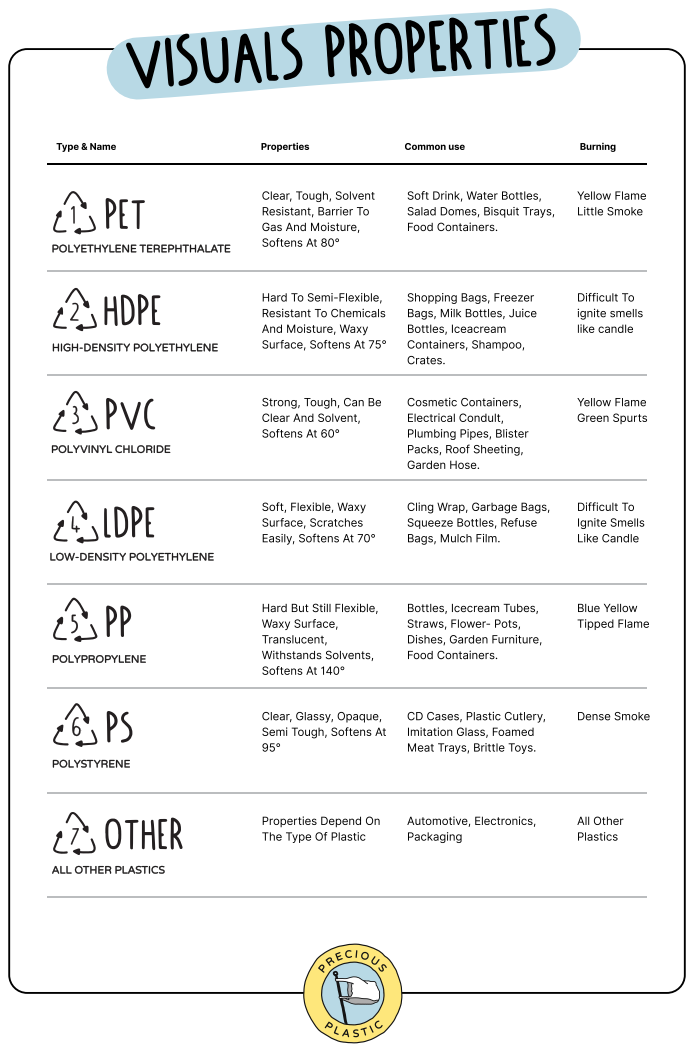
[picture p172: page 1]
visuals properties; POLYVINYL CHLORIDE; POLYPROPYLENE; POLYSTYRENE; POLYETHYLENE TEREPHTHALATE; Type & Name; Properties; Common use; Burning; yellow flame little smoke; Difficult To ignite smells like candle; yellow flame green spurts; difficult to ignite smells like candle; blue yellow tipped flame; dense smoke; automotive, electronics, packaging; all other plastics

clear, tough, solvent
resistant, barrier to
gas and moisture,
softens at 80°

Soft drink, water bottles,
salad domes, bisquit trays,
food containers.

Hard to semi-flexible,
resistant to chemicals
and moisture, waxy
surface, softens at 75°

Shopping bags, freezer
bags, milk bottles, juice
bottles, iceacream
containers, shampoo,
crates.

HIGH-DENSITY POLYETHYLENE

Strong, tough, can be
clear and solvent,
softens at 60°

Cosmetic containers,
electrical condult,
plumbing pipes, blister
packs, roof sheeting,
garden hose.

Soft, flexible, waxy
surface, scratches
easily, softens at 70°

Cling wrap, garbage bags,
squeeze bottles, refuse
bags, mulch film.

LOW-DENSITY POLYETHYLENE

Hard but still flexible,
waxy surface,
translucent,
withstands solvents,
softens at 140°

Bottles, icecream tubes,
straws, flower- pots,
dishes, garden furniture,

Clear, glassy, opaque,
semi tough, softens at

CD cases, plastic cutlery,
imitation glass, foamed
meat trays, brittle toys.

Properties depend on
the type of plastic

ALL OTHER PLASTICS
