ONEARMY/Precious-plastic-starterkit-extrusion/4. Set up the space/Blueprints/00_shredded plastic storage_EXT.PDF

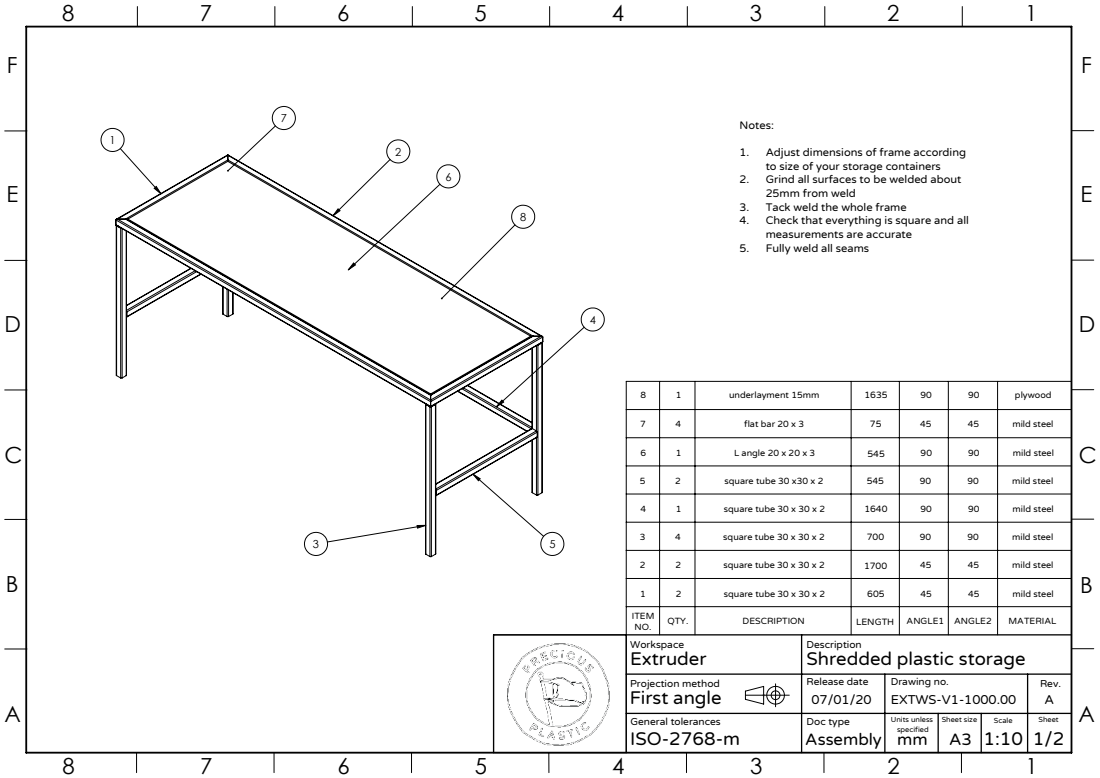
[picture p173: page 1]
First angle

1. Adjust dimensions of frame according
to size of your storage containers
2. Grind all surfaces to be welded about
25mm from weld
3. Tack weld the whole frame
4. Check that everything is square and all
measurements are accurate
5. Fully weld all seams

8 | 1 | underlayment 15mm | 1635 | 90 | 90 | plywood

7 | 4 | flat bar 20 x 3 | 75 | 45 | 45 | mild steel

6 | 1 | L angle 20 x 20 x 3 | 545 | 90 | 90 | mild steel

5 | 2 | square tube 30 x30 x 2 | 545 | 90 | 90 | mild steel

4 | 1 | square tube 30 x 30 x 2 | 1640 | 90 | 90 | mild steel

3 | 4 | square tube 30 x 30 x 2 | 700 | 90 | 90 | mild steel

2 | 2 | square tube 30 x 30 x 2 | 1700 | 45 | 45 | mild steel

1 | 2 | square tube 30 x 30 x 2 | 605 | 45 | 45 | mild steel
NO. | QTY. | DESCRIPTION ITEM | LENGTH | ANGLE1 | ANGLE2 | MATERIAL

Workspace Extruder | Description Shredded plastic storage

Projection method | | Release date 07/01/20 | Drawing no. EXTWS-V1-1000.00 | Rev. A
General tolerances ISO-2768-m | Doc type Assembly | Units unless specified mm | Sheet size A3 | Scale 1:10 | Sheet 1/2

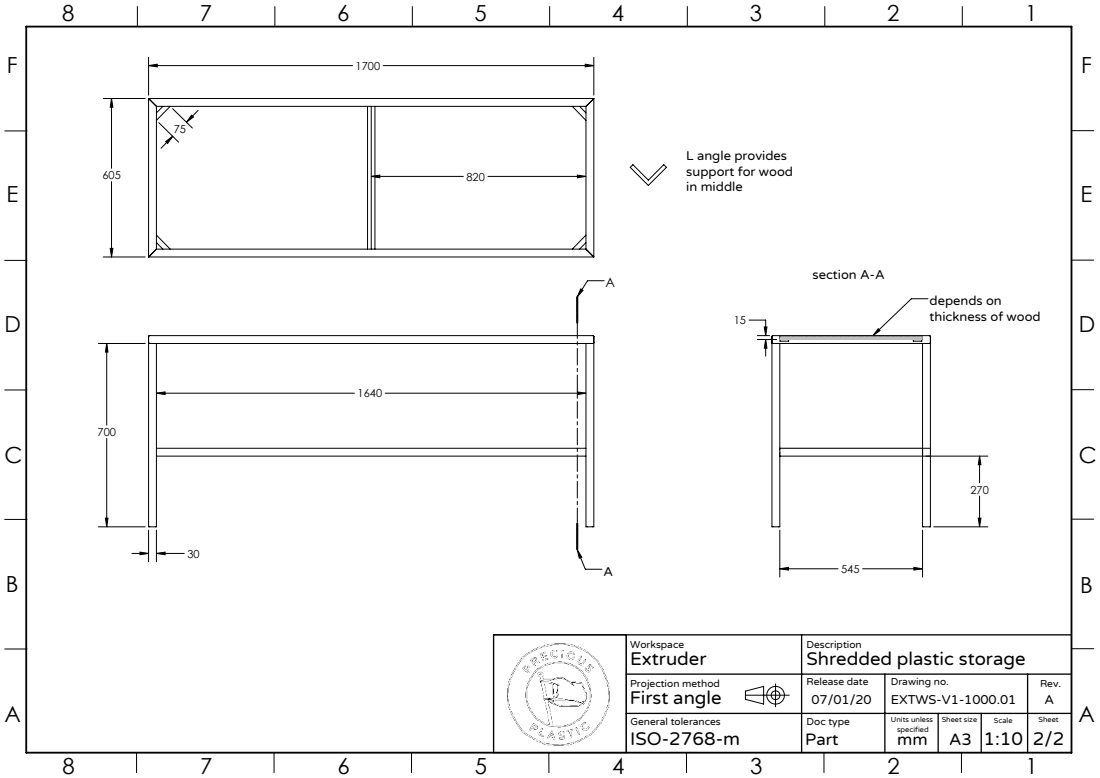
[picture p174: page 2]
section A-A; First angle

L angle provides
support for wood
in middle

depends on
thickness of wood

Workspace Extruder | Description Shredded plastic storage

Projection method | | Release date 07/01/20 | Drawing no. EXTWS-V1-1000.01 | Rev. A
General tolerances ISO-2768-m | Doc type Part | Units unless specified mm | Sheet size A3 | Scale 1:10 | Sheet 2/2
