ONEARMY/Precious-plastic-starterkit-extrusion/4. Set up the space/Blueprints/01_workbench_EXT.PDF

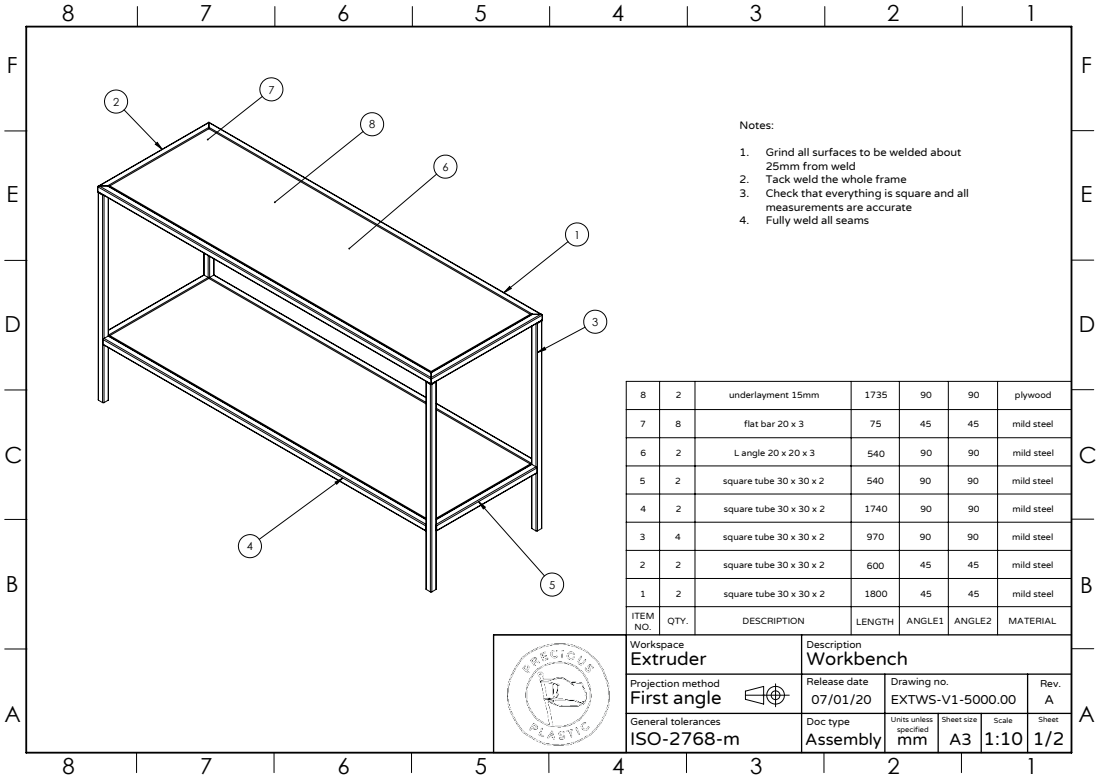
[picture p175: page 1]
First angle

1. Grind all surfaces to be welded about
25mm from weld
2. Tack weld the whole frame
3. Check that everything is square and all
measurements are accurate
4. Fully weld all seams

8 | 2 | underlayment 15mm | 1735 | 90 | 90 | plywood

7 | 8 | flat bar 20 x 3 | 75 | 45 | 45 | mild steel

6 | 2 | L angle 20 x 20 x 3 | 540 | 90 | 90 | mild steel

5 | 2 | square tube 30 x 30 x 2 | 540 | 90 | 90 | mild steel

4 | 2 | square tube 30 x 30 x 2 | 1740 | 90 | 90 | mild steel

3 | 4 | square tube 30 x 30 x 2 | 970 | 90 | 90 | mild steel

2 | 2 | square tube 30 x 30 x 2 | 600 | 45 | 45 | mild steel

1 | 2 | square tube 30 x 30 x 2 | 1800 | 45 | 45 | mild steel
NO. | QTY. | DESCRIPTION ITEM | LENGTH | ANGLE1 | ANGLE2 | MATERIAL

Workspace Extruder | Description Workbench

Projection method | | Release date 07/01/20 | Drawing no. EXTWS-V1-5000.00 | Rev. A
General tolerances ISO-2768-m | Doc type Assembly | Units unless specified mm | Sheet size A3 | Scale 1:10 | Sheet 1/2

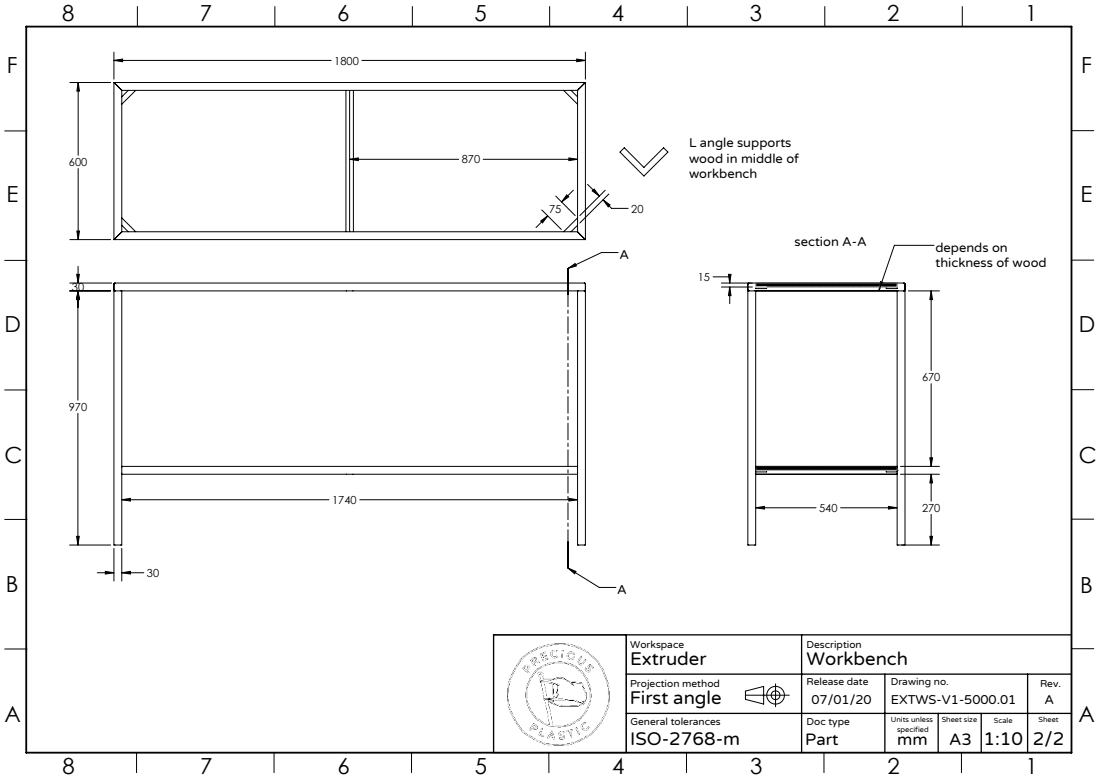
[picture p176: page 2]
section A-A; First angle

L angle supports
wood in middle of
workbench

depends on
thickness of wood

Workspace Extruder | Description Workbench

Projection method | | Release date 07/01/20 | Drawing no. EXTWS-V1-5000.01 | Rev. A
General tolerances ISO-2768-m | Doc type Part | Units unless specified mm | Sheet size A3 | Scale 1:10 | Sheet 2/2
