ONEARMY/Precious-plastic-starterkit-extrusion/4. Set up the space/Blueprints/02_shredded plastic trolley_EXT.PDF

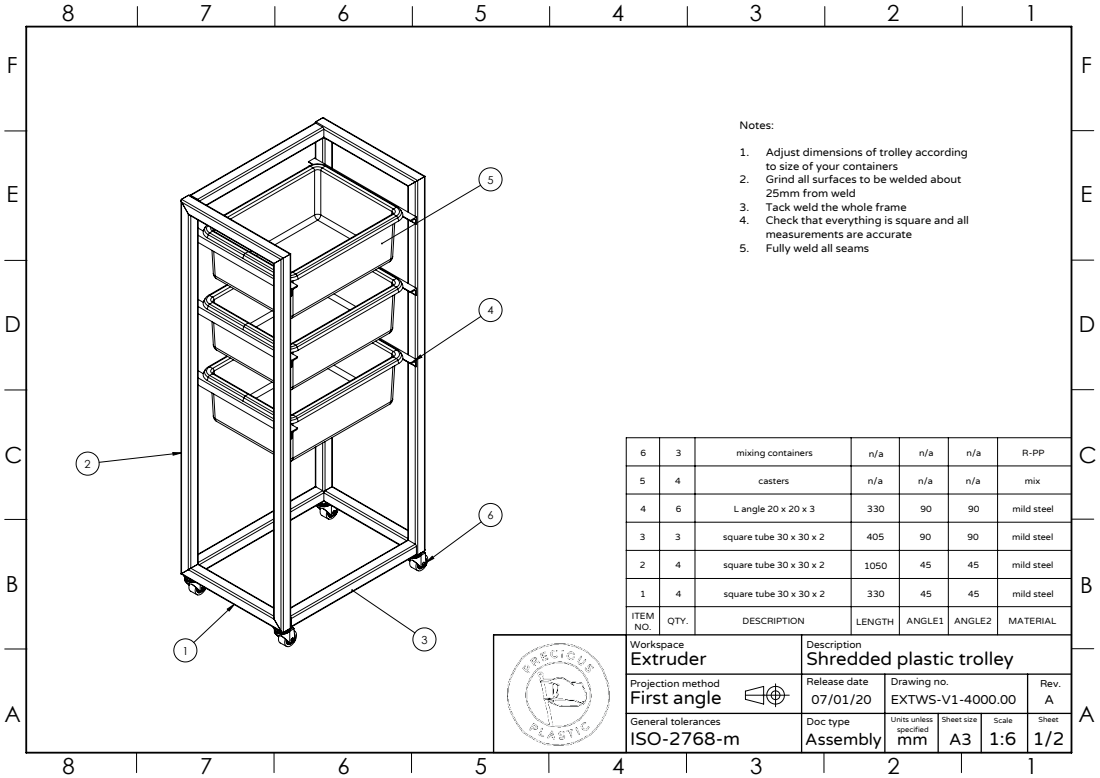
[picture p177: page 1]
First angle

1. Adjust dimensions of trolley according
to size of your containers
2. Grind all surfaces to be welded about
25mm from weld
3. Tack weld the whole frame
4. Check that everything is square and all
measurements are accurate
5. Fully weld all seams

6 | 3 | mixing containers | n/a | n/a | n/a | R-PP

5 | 4 | casters | n/a | n/a | n/a | mix

4 | 6 | L angle 20 x 20 x 3 | 330 | 90 | 90 | mild steel

3 | 3 | square tube 30 x 30 x 2 | 405 | 90 | 90 | mild steel

2 | 4 | square tube 30 x 30 x 2 | 1050 | 45 | 45 | mild steel

1 | 4 | square tube 30 x 30 x 2 | 330 | 45 | 45 | mild steel
NO. | QTY. | DESCRIPTION ITEM | LENGTH | ANGLE1 | ANGLE2 | MATERIAL

Workspace Extruder | Description Shredded plastic trolley

Projection method | | Release date 07/01/20 | Drawing no. EXTWS-V1-4000.00 | Rev. A
General tolerances ISO-2768-m | Doc type Assembly | Units unless specified mm | Sheet size A3 | Scale 1:6 | Sheet 1/2

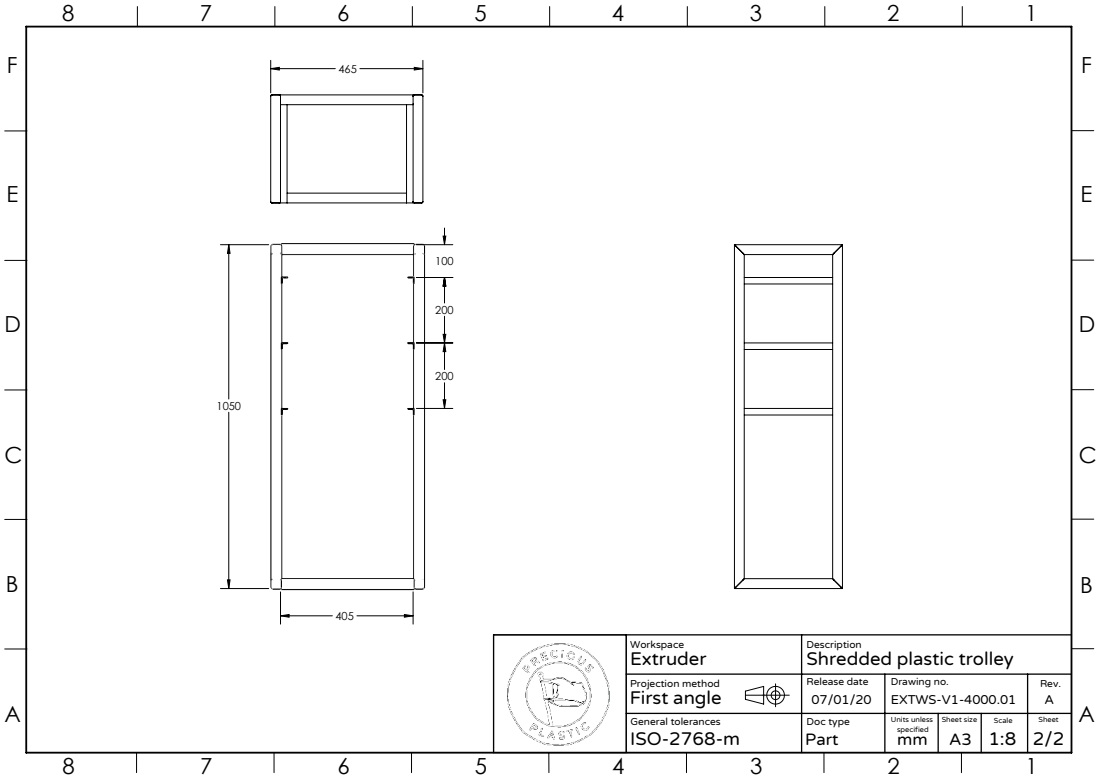
[picture p178: page 2]
First angle

Workspace Extruder | Description Shredded plastic trolley

Projection method | | Release date 07/01/20 | Drawing no. EXTWS-V1-4000.01 | Rev. A
General tolerances ISO-2768-m | Doc type Part | Units unless specified mm | Sheet size A3 | Scale 1:8 | Sheet 2/2
