ONEARMY/Precious-plastic-starterkit-extrusion/4. Set up the space/Blueprints/03_mobile tool station_EXT.PDF

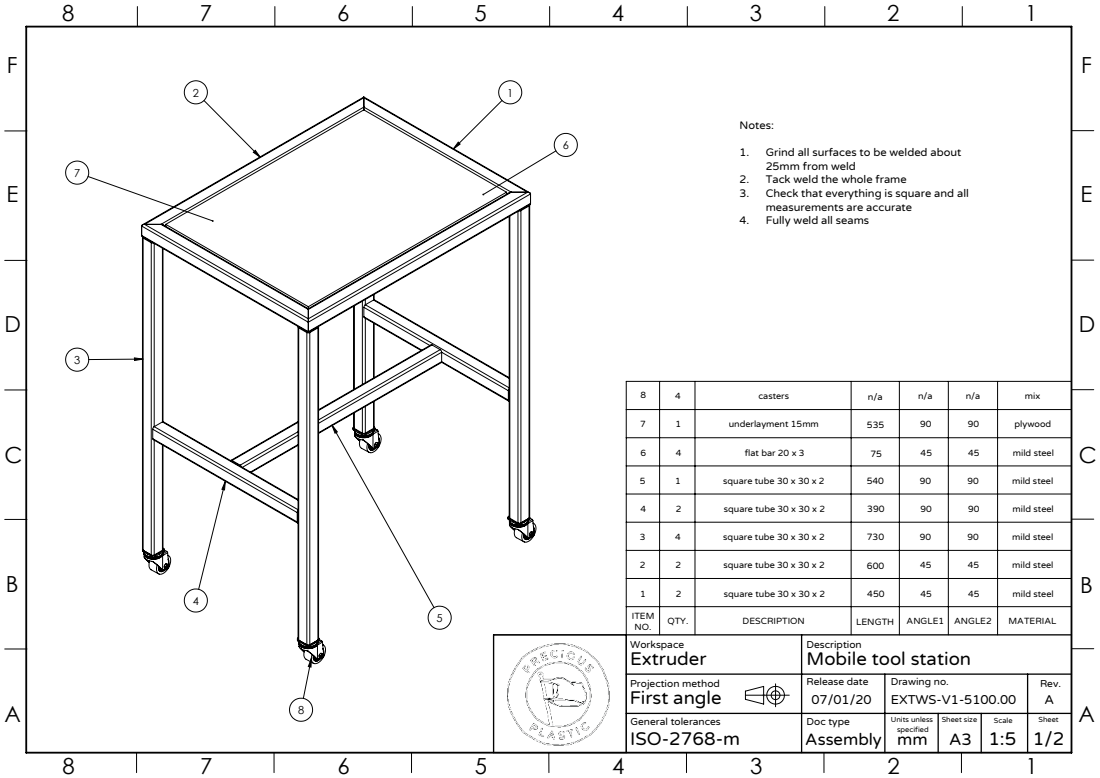
[picture p179: page 1]
First angle

1. Grind all surfaces to be welded about
25mm from weld
2. Tack weld the whole frame
3. Check that everything is square and all
measurements are accurate
4. Fully weld all seams

8 | 4 | casters | n/a | n/a | n/a | mix

7 | 1 | underlayment 15mm | 535 | 90 | 90 | plywood

6 | 4 | flat bar 20 x 3 | 75 | 45 | 45 | mild steel

5 | 1 | square tube 30 x 30 x 2 | 540 | 90 | 90 | mild steel

4 | 2 | square tube 30 x 30 x 2 | 390 | 90 | 90 | mild steel

3 | 4 | square tube 30 x 30 x 2 | 730 | 90 | 90 | mild steel

2 | 2 | square tube 30 x 30 x 2 | 600 | 45 | 45 | mild steel

1 | 2 | square tube 30 x 30 x 2 | 450 | 45 | 45 | mild steel
NO. | QTY. | DESCRIPTION ITEM | LENGTH | ANGLE1 | ANGLE2 | MATERIAL

Workspace Extruder | Description Mobile tool station

Projection method | | Release date 07/01/20 | Drawing no. EXTWS-V1-5100.00 | Rev. A
General tolerances ISO-2768-m | Doc type Assembly | Units unless specified mm | Sheet size A3 | Scale 1:5 | Sheet 1/2

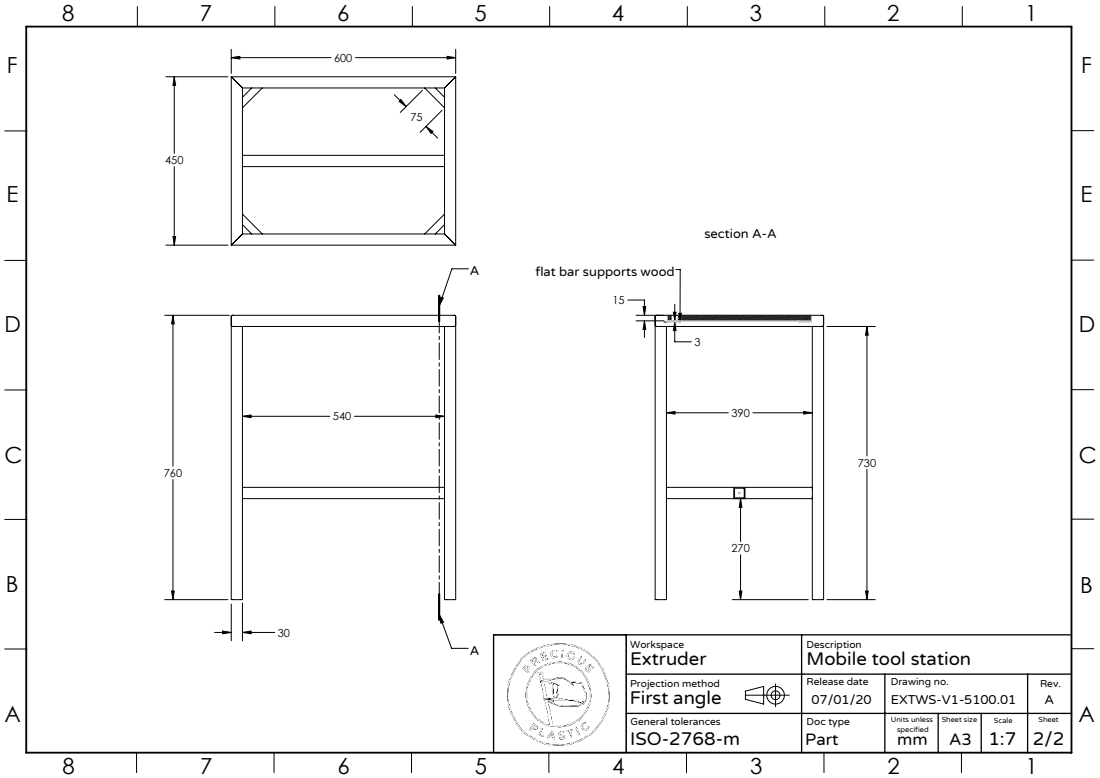
[picture p180: page 2]
flat bar supports wood; section A-A; First angle

Workspace Extruder | Description Mobile tool station

Projection method | | Release date 07/01/20 | Drawing no. EXTWS-V1-5100.01 | Rev. A
General tolerances ISO-2768-m | Doc type Part | Units unless specified mm | Sheet size A3 | Scale 1:7 | Sheet 2/2
