ONEARMY/Precious-plastic-starterkit-extrusion/4. Set up the space/Blueprints/04_beam storage rack_EXT.PDF

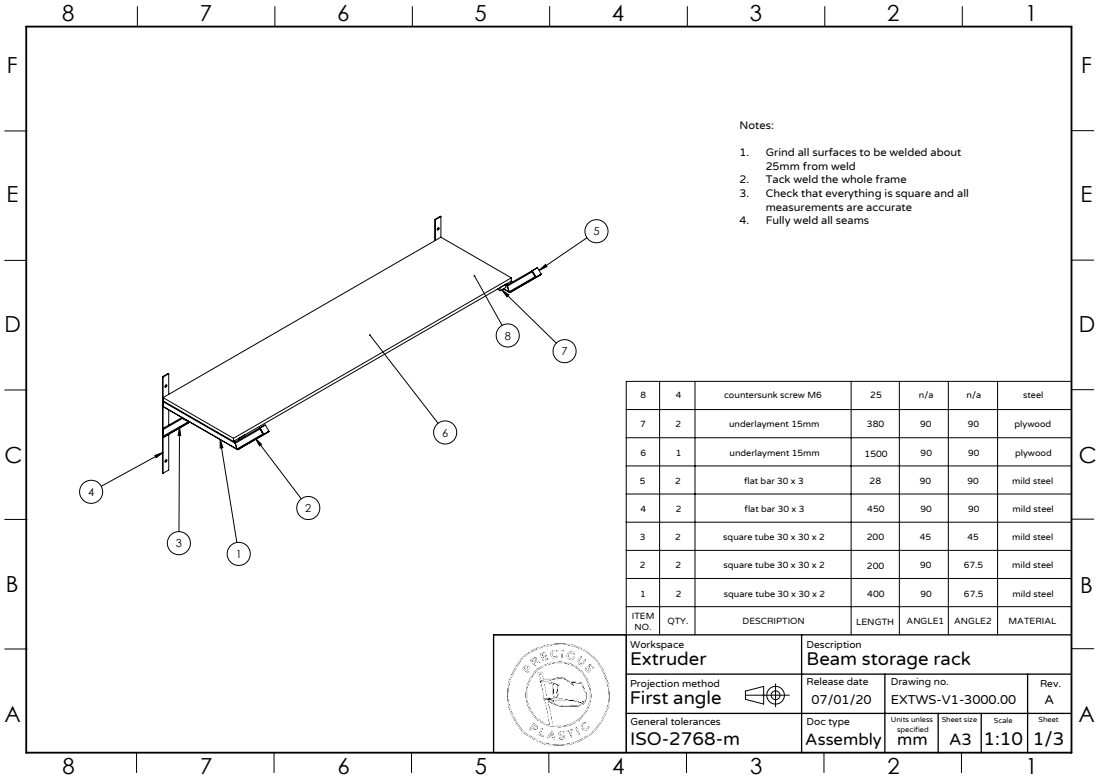
[picture p181: page 1]
First angle

1. Grind all surfaces to be welded about
25mm from weld
2. Tack weld the whole frame
3. Check that everything is square and all
measurements are accurate
4. Fully weld all seams

8 | 4 | countersunk screw M6 | 25 | n/a | n/a | steel

7 | 2 | underlayment 15mm | 380 | 90 | 90 | plywood

6 | 1 | underlayment 15mm | 1500 | 90 | 90 | plywood

5 | 2 | flat bar 30 x 3 | 28 | 90 | 90 | mild steel

4 | 2 | flat bar 30 x 3 | 450 | 90 | 90 | mild steel

3 | 2 | square tube 30 x 30 x 2 | 200 | 45 | 45 | mild steel

2 | 2 | square tube 30 x 30 x 2 | 200 | 90 | 67.5 | mild steel

1 | 2 | square tube 30 x 30 x 2 | 400 | 90 | 67.5 | mild steel
NO. | QTY. | DESCRIPTION ITEM | LENGTH | ANGLE1 | ANGLE2 | MATERIAL

Workspace Extruder | Description Beam storage rack

Projection method | | Release date 07/01/20 | Drawing no. EXTWS-V1-3000.00 | Rev. A
General tolerances ISO-2768-m | Doc type Assembly | Units unless specified mm | Sheet size A3 | Scale 1:10 | Sheet 1/3

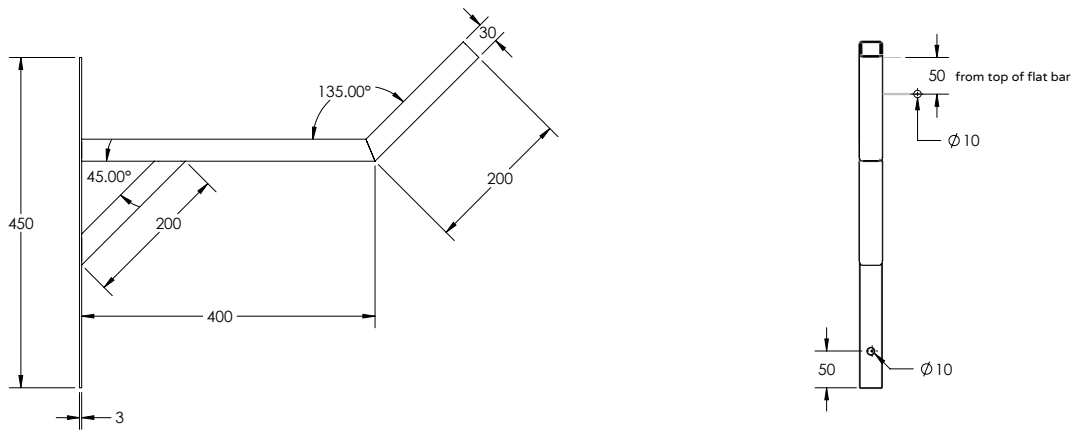
[picture p182: page 2]
First angle

50 from top of flat bar

Workspace Extruder | Description Beam storage rack

Projection method | | Release date 07/01/20 | Drawing no. EXTWS-V1-3000.01 | Rev. A

ISO-2768-m | Part | mm | A3 | 1:10 | 2/3

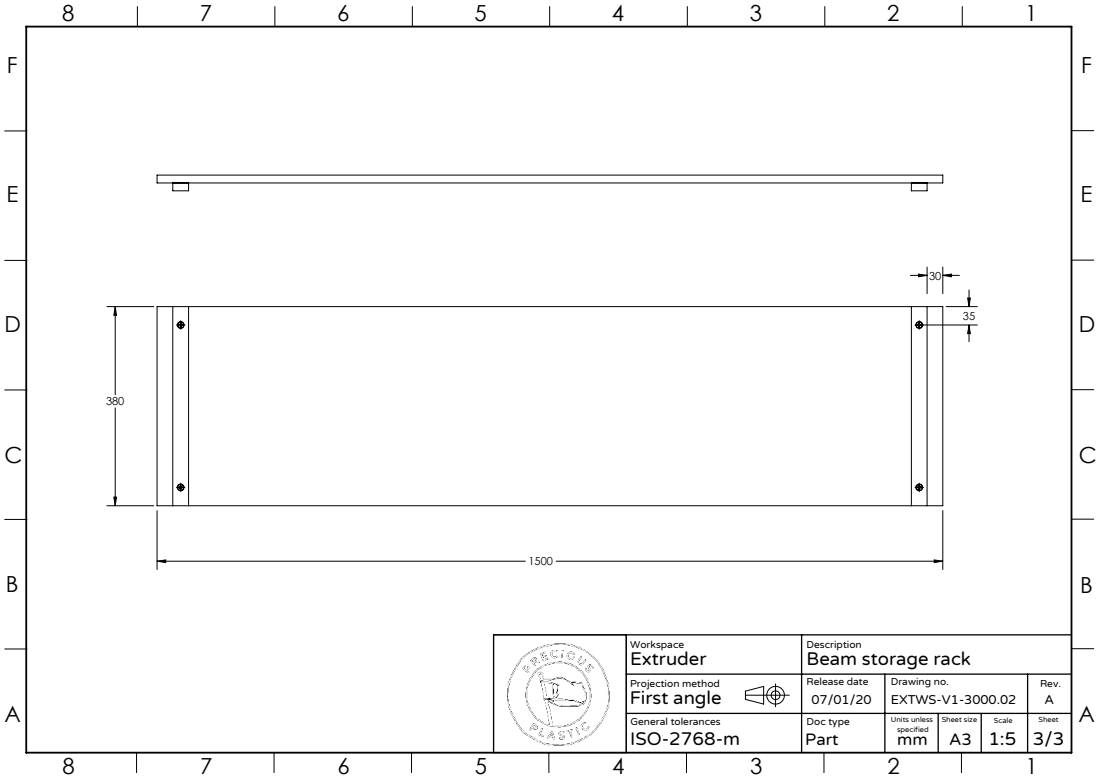
[picture p183: page 3]
First angle

Workspace Extruder | Description Beam storage rack

Projection method | | Release date 07/01/20 | Drawing no. EXTWS-V1-3000.02 | Rev. A

ISO-2768-m | Part | mm | A3 | 1:5 | 3/3
