ONEARMY/Precious-plastic-starterkit-extrusion/4. Set up the space/Blueprints/05_beam mould hanger_EXT.PDF

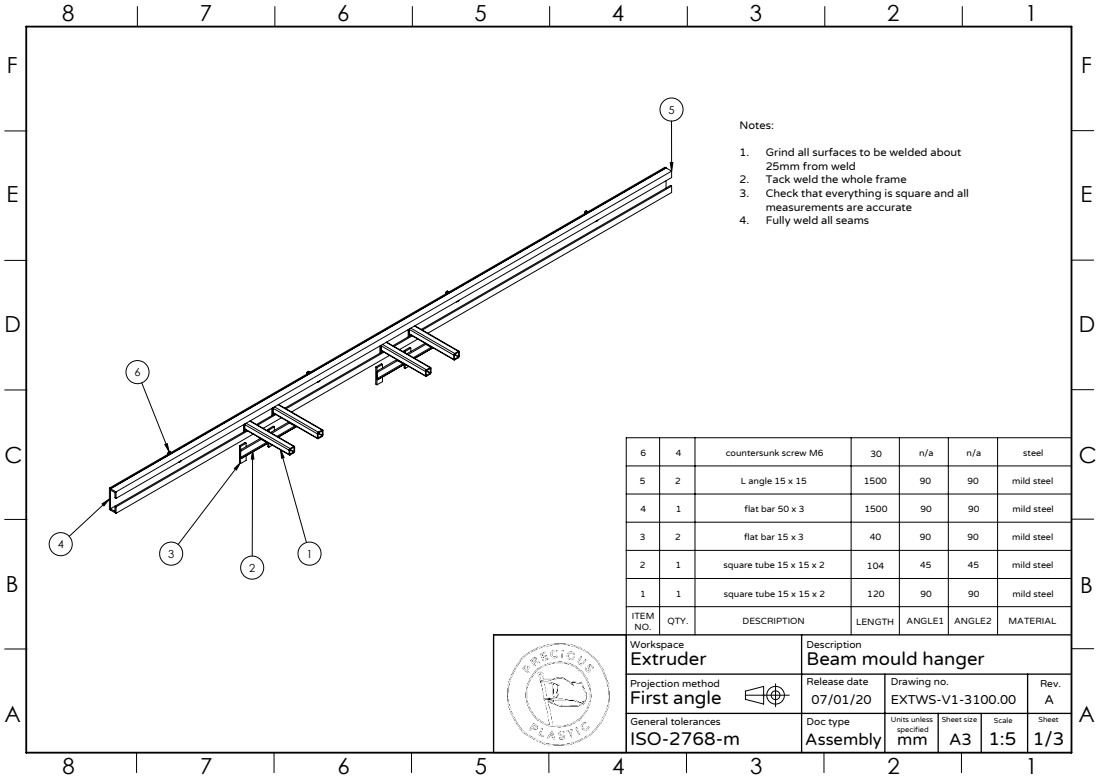
[picture p184: page 1]
First angle

1. Grind all surfaces to be welded about
25mm from weld
2. Tack weld the whole frame
3. Check that everything is square and all
measurements are accurate
4. Fully weld all seams

6 | 4 | countersunk screw M6 | 30 | n/a | n/a | steel

5 | 2 | L angle 15 x 15 | 1500 | 90 | 90 | mild steel

4 | 1 | flat bar 50 x 3 | 1500 | 90 | 90 | mild steel

3 | 2 | flat bar 15 x 3 | 40 | 90 | 90 | mild steel

2 | 1 | square tube 15 x 15 x 2 | 104 | 45 | 45 | mild steel

1 | 1 | square tube 15 x 15 x 2 | 120 | 90 | 90 | mild steel
NO. | QTY. | DESCRIPTION ITEM | LENGTH | ANGLE1 | ANGLE2 | MATERIAL

Workspace Extruder | Description Beam mould hanger

Projection method | | Release date 07/01/20 | Drawing no. EXTWS-V1-3100.00 | Rev. A
General tolerances ISO-2768-m | Doc type Assembly | Units unless specified mm | Sheet size A3 | Scale 1:5 | Sheet 1/3

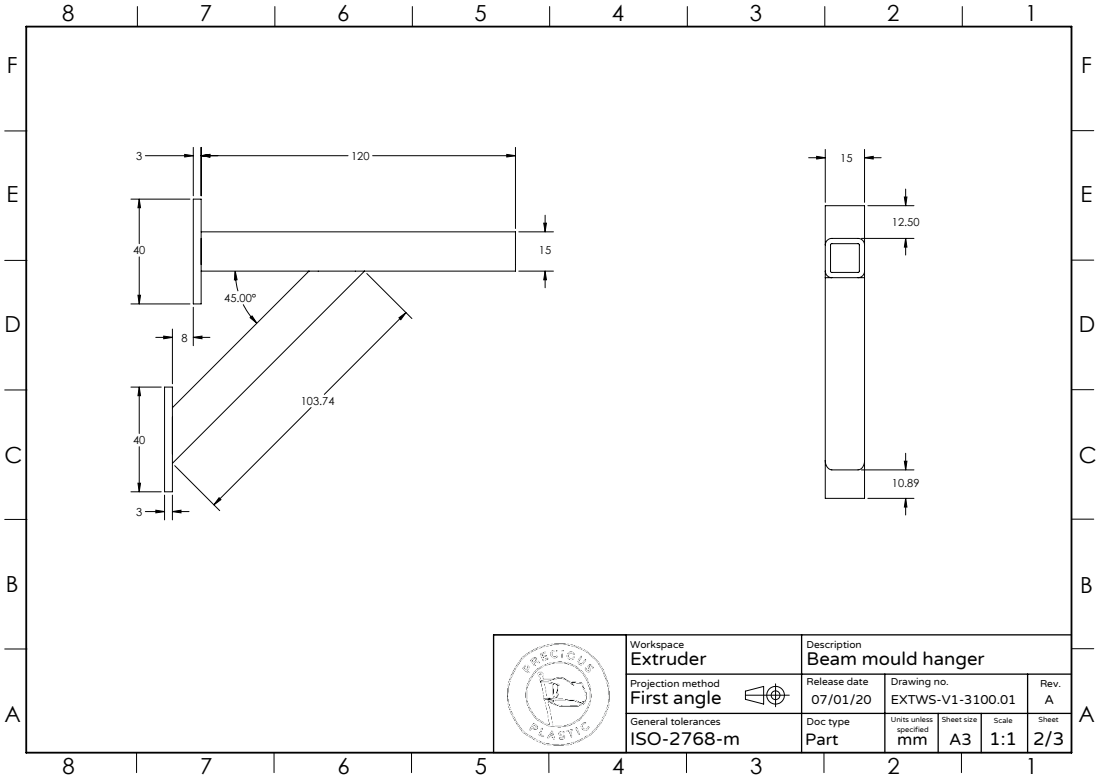
[picture p185: page 2]
First angle

Workspace Extruder | Description Beam mould hanger

Projection method | | Release date 07/01/20 | Drawing no. EXTWS-V1-3100.01 | Rev. A

ISO-2768-m | Part | mm | A3 | 1:1 | 2/3

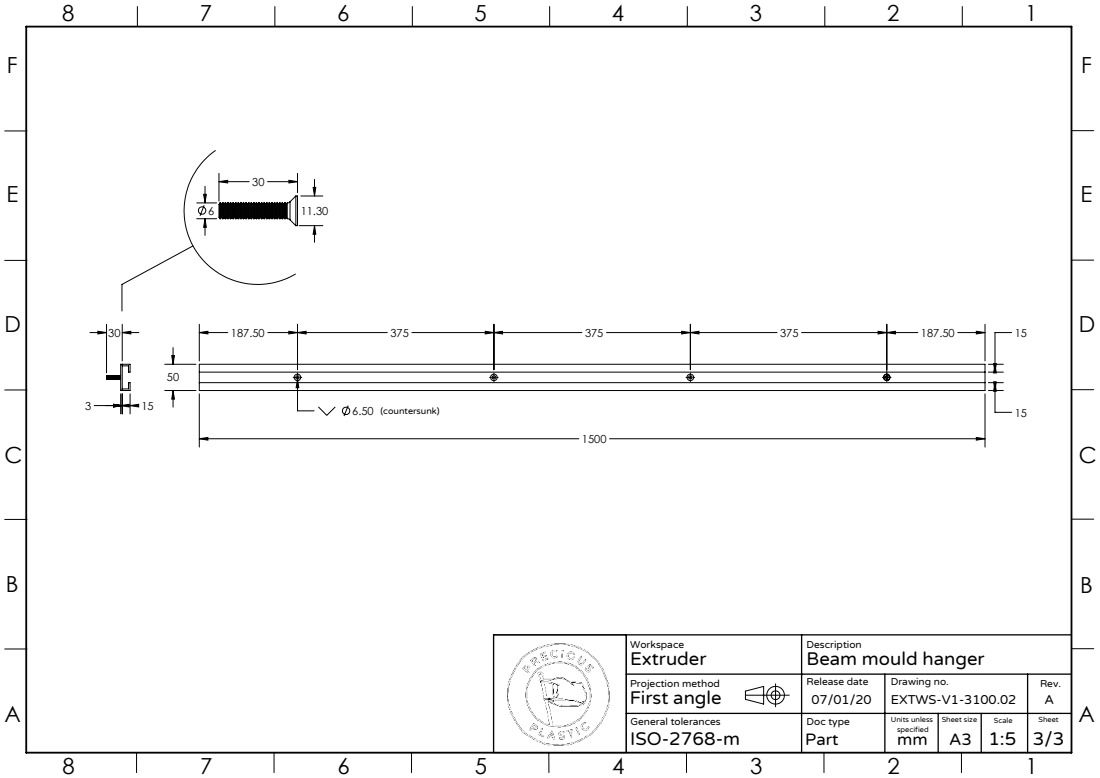
[picture p186: page 3]
First angle

Workspace Extruder | Description Beam mould hanger

Projection method | | Release date 07/01/20 | Drawing no. EXTWS-V1-3100.02 | Rev. A

ISO-2768-m | Part | mm | A3 | 1:5 | 3/3
