ONEARMY/Precious-plastic-starterkit-extrusion/4. Set up the space/Blueprints/06_adjustmable mold support surface_EXT.PDF

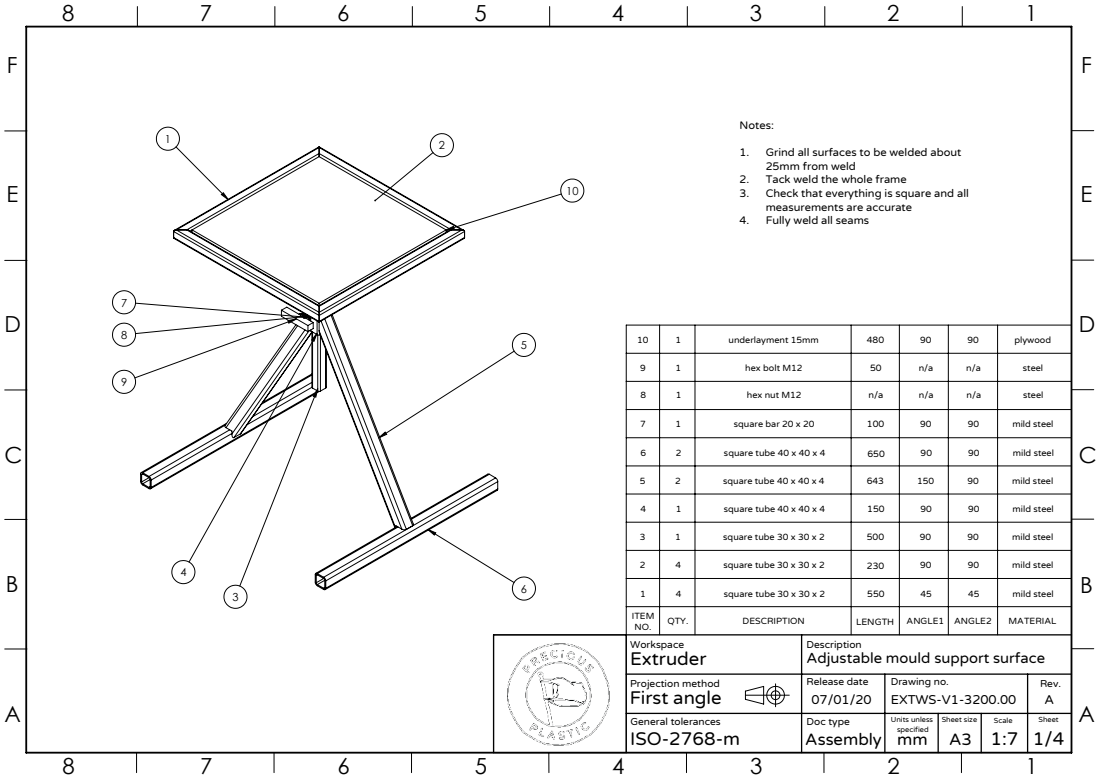
[picture p187: page 1]
First angle

1. Grind all surfaces to be welded about
25mm from weld
2. Tack weld the whole frame
3. Check that everything is square and all
measurements are accurate
4. Fully weld all seams

10 | 1 | underlayment 15mm | 480 | 90 | 90 | plywood

9 | 1 | hex bolt M12 | 50 | n/a | n/a | steel

8 | 1 | hex nut M12 | n/a | n/a | n/a | steel

General tolerances | 2 1 4 1 4 1 2 | square tube 40 x 40 x 4 square tube 30 x 30 x 2 square tube 30 x 30 x 2 square tube 30 x 30 x 2 square tube 40 x 40 x 4 square tube 40 x 40 x 4 square bar 20 x 20 | 643 500 230 100 550 150 650 | 150 90 90 90 45 90 90 Sheet size | 90 90 90 90 45 90 90 Scale | mild steel 6 mild steel 4 mild steel 3 mild steel mild steel 2 mild steel 5 mild steel 7 Sheet 1

NO. | QTY. | DESCRIPTION ITEM | LENGTH | ANGLE1 | ANGLE2 | MATERIAL

Workspace Extruder | Description Adjustable mould support surface

Projection method | | Release date 07/01/20 | Drawing no. EXTWS-V1-3200.00 | Rev. A
ISO-2768-m | Doc type Assembly | Units unless specified mm | A3 | 1:7 | 1/4

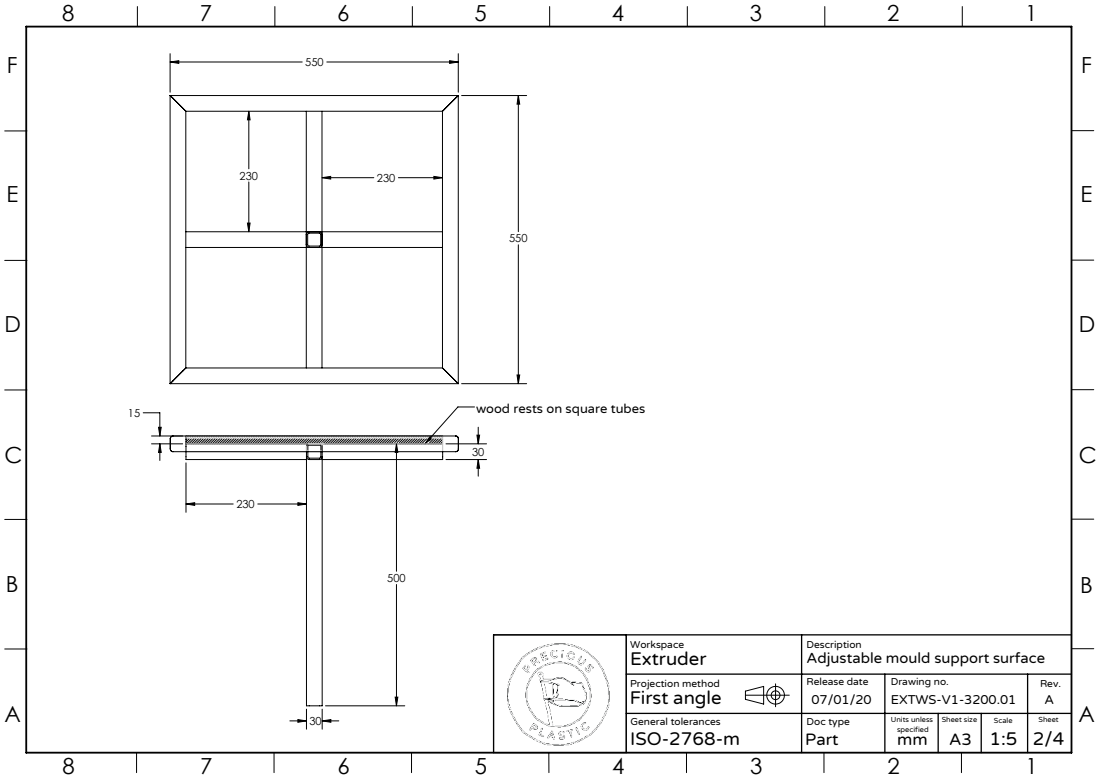
[picture p188: page 2]
wood rests on square tubes; First angle

Workspace Extruder | Description Adjustable mould support surface

Projection method | | Release date 07/01/20 | Drawing no. EXTWS-V1-3200.01 | Rev. A
General tolerances ISO-2768-m | Part | mm | Sheet size A3 | Scale 1:5 | Sheet 2/4

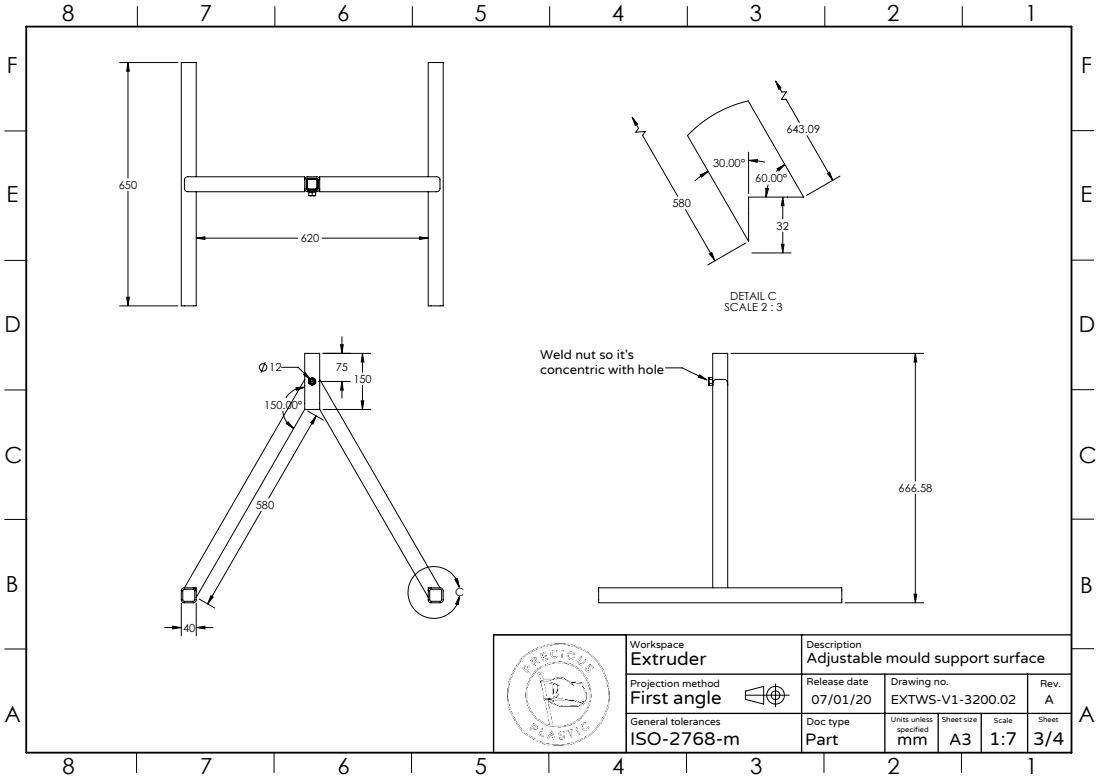
[picture p189: page 3]
DETAIL C SCALE 2 : 3; First angle

Weld nut so it's
concentric with hole

Workspace Extruder | Description Adjustable mould support surface

Projection method | | Release date 07/01/20 | Drawing no. EXTWS-V1-3200.02 | Rev. A

ISO-2768-m | Part | mm | A3 | 1:7 | 3/4

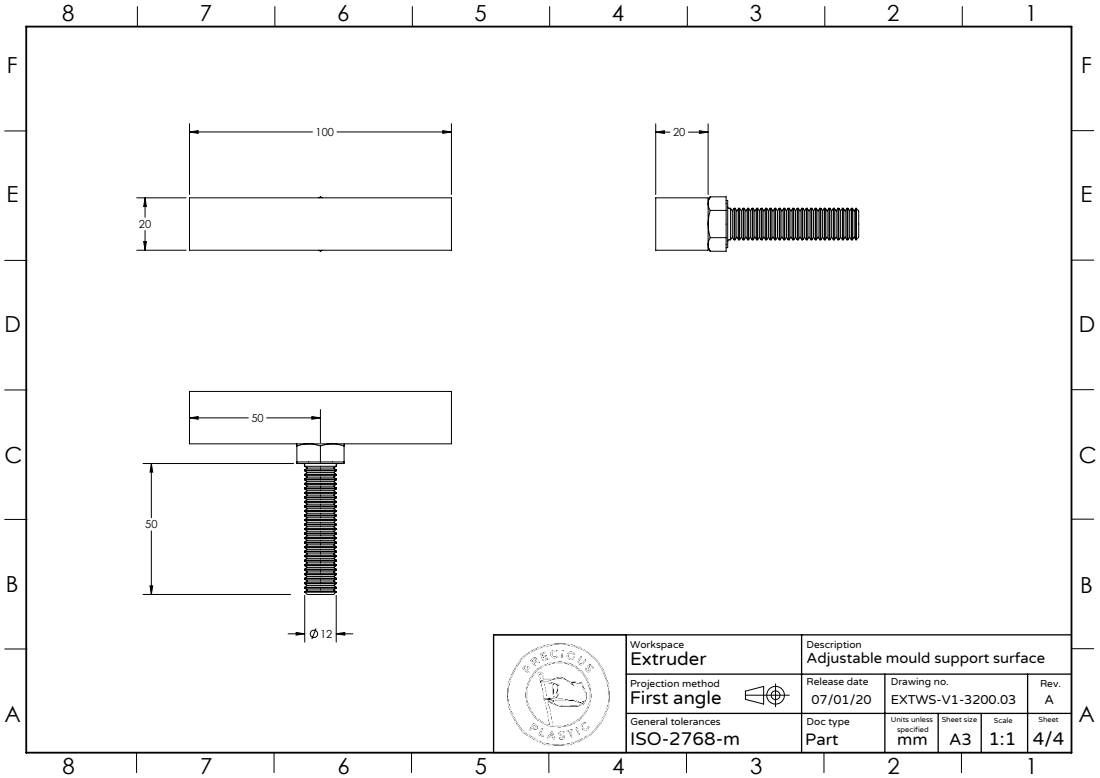
[picture p190: page 4]
First angle

Workspace Extruder | Description Adjustable mould support surface

Projection method | | Release date 07/01/20 | Drawing no. EXTWS-V1-3200.03 | Rev. A

ISO-2768-m | Part | mm | A3 | 1:1 | 4/4
