ONEARMY/Precious-plastic-starterkit-extrusion/4. Set up the space/Blueprints/07_ventilation caddy_EXT.PDF

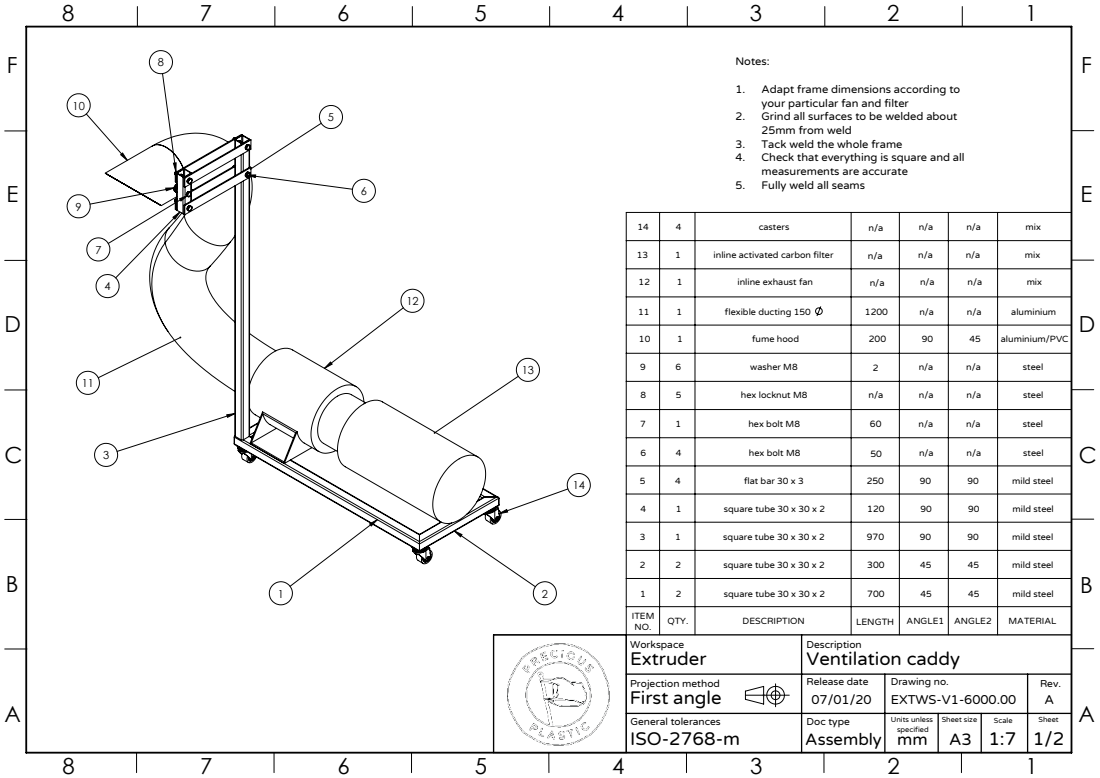
[picture p191: page 1]
First angle

1. Adapt frame dimensions according to
your particular fan and filter
2. Grind all surfaces to be welded about
25mm from weld
3. Tack weld the whole frame
4. Check that everything is square and all
measurements are accurate
5. Fully weld all seams

14 | 4 | casters | n/a | n/a | n/a | mix

13 | 1 | inline activated carbon filter | n/a | n/a | n/a | mix

12 | 1 | inline exhaust fan | n/a | n/a | n/a | mix

11 | 1 | flexible ducting 150 | 1200 | n/a | n/a | aluminium

10 | 1 | fume hood | 200 | 90 | 45 | aluminium/PVC

9 | 6 | washer M8 | 2 | n/a | n/a | steel

8 | 5 | hex locknut M8 | n/a | n/a | n/a | steel

General tolerances | 4 1 2 1 2 1 4 | square tube 30 x 30 x 2 square tube 30 x 30 x 2 square tube 30 x 30 x 2 square tube 30 x 30 x 2 flat bar 30 x 3 hex bolt M8 hex bolt M8 | 250 970 700 300 120 60 50 | n/a n/a 90 90 45 45 90 Sheet size | n/a 90 6 90 45 45 90 Scale | mild steel 4 mild steel 3 mild steel 2 mild steel 5 steel steel 7 Sheet 1

mild steel

NO. | QTY. | DESCRIPTION ITEM | LENGTH | ANGLE1 | ANGLE2 | MATERIAL

Workspace Extruder | Description Ventilation caddy

Projection method | | Release date 07/01/20 | Drawing no. EXTWS-V1-6000.00 | Rev. A
ISO-2768-m | Doc type Assembly | Units unless specified mm | A3 | 1:7 | 1/2

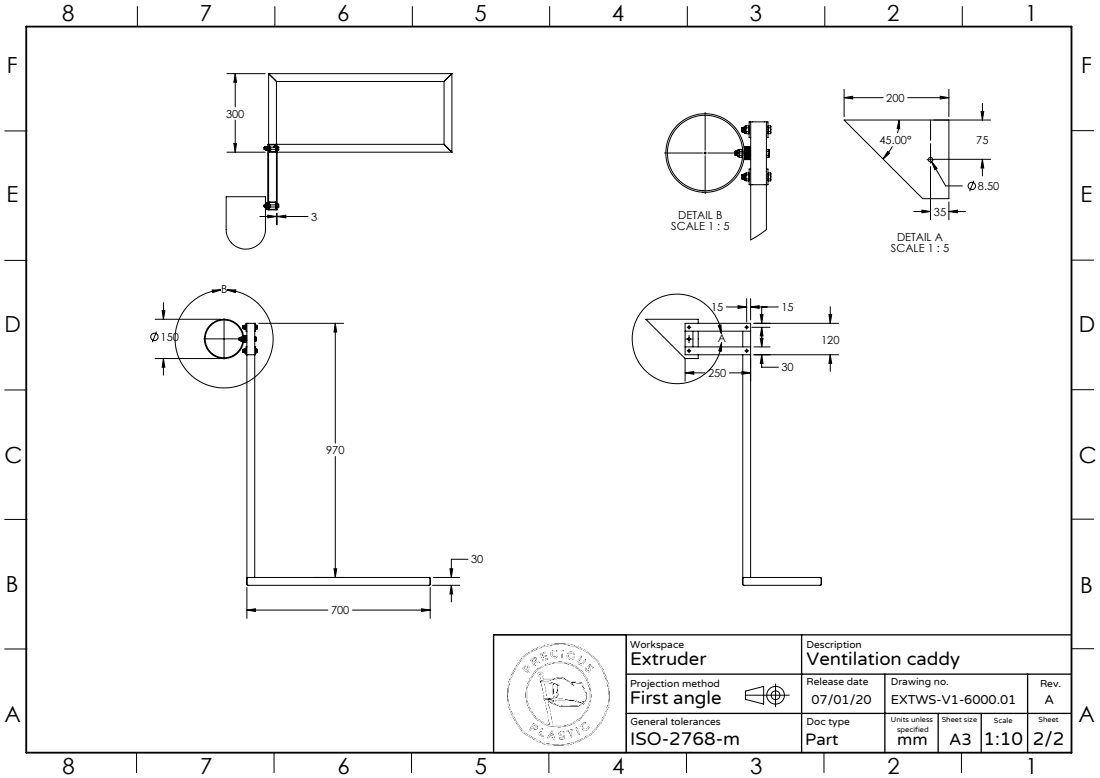
[picture p192: page 2]
DETAIL A SCALE 1 : 5; DETAIL B SCALE 1 : 5; First angle

Workspace Extruder | Description Ventilation caddy

Projection method | | Release date 07/01/20 | Drawing no. EXTWS-V1-6000.01 | Rev. A
General tolerances ISO-2768-m | Doc type Part | Units unless specified mm | Sheet size A3 | Scale 1:10 | Sheet 2/2
